dragland/Smart_Home/html/res/posters/0vNBeXZ.png

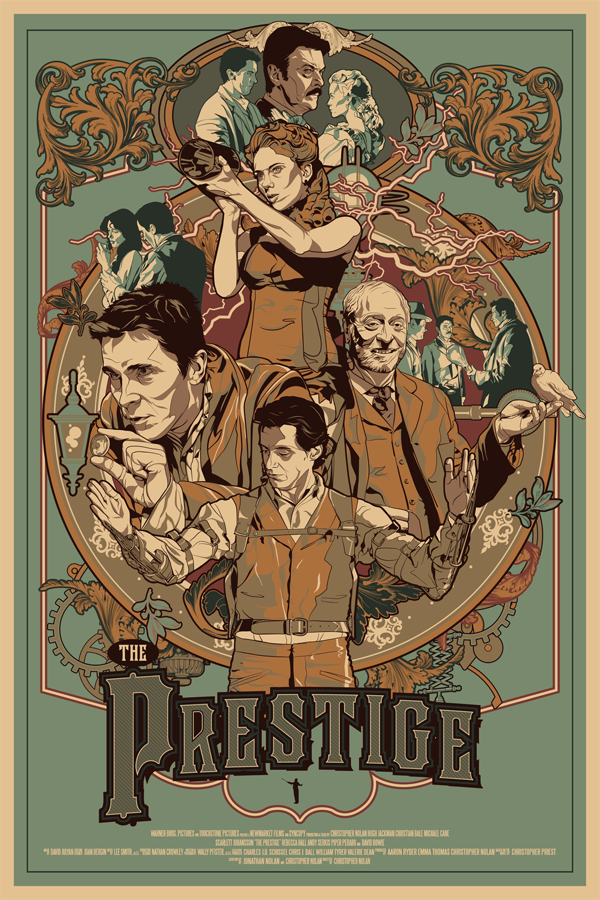
html/res/posters/0vNBeXZ.png
