dragland/Smart_Home/html/res/posters/1m5z1brr5z6y.jpg

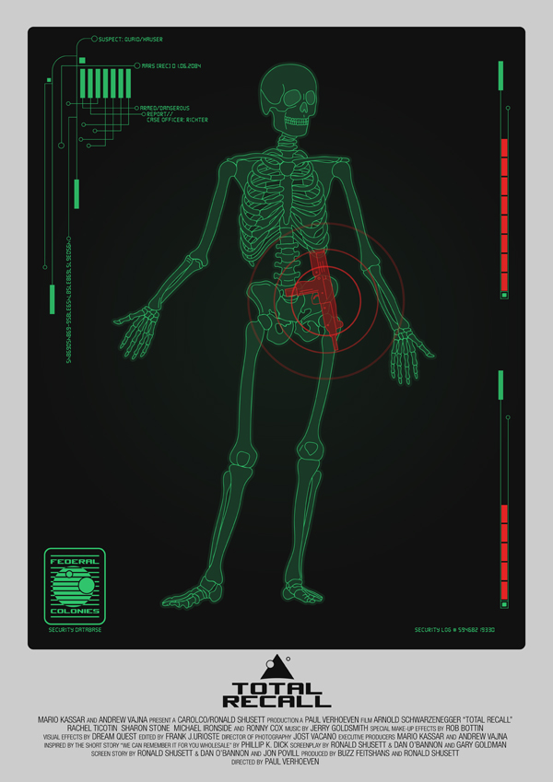
html/res/posters/1m5z1brr5z6y.jpg
