dragland/Smart_Home/html/res/posters/2OzRsxW.jpg

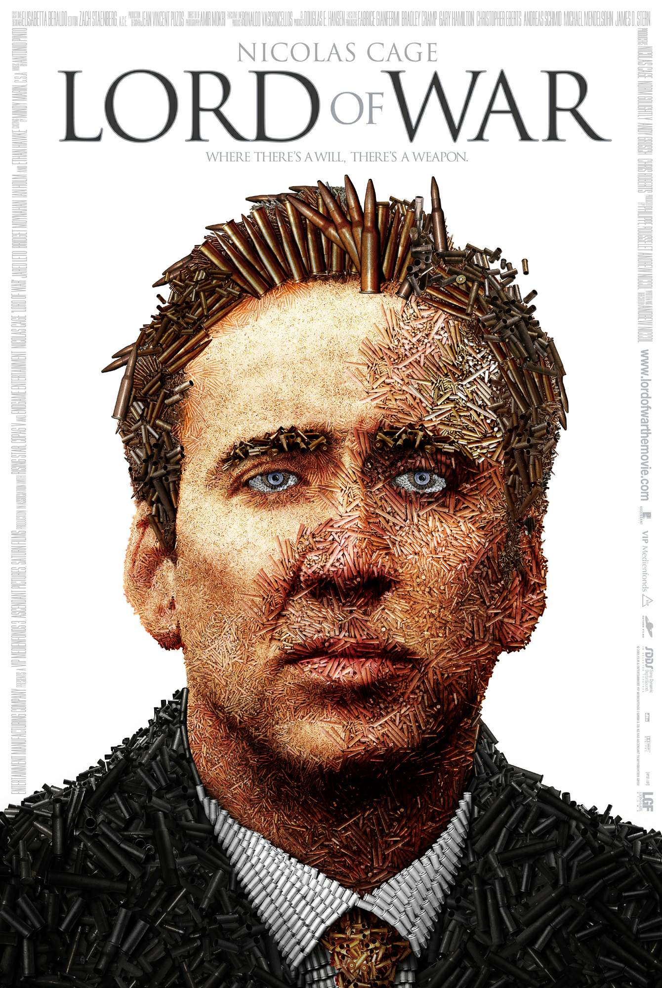
html/res/posters/2OzRsxW.jpg
