dragland/Smart_Home/html/res/posters/3QKCHwL.jpg

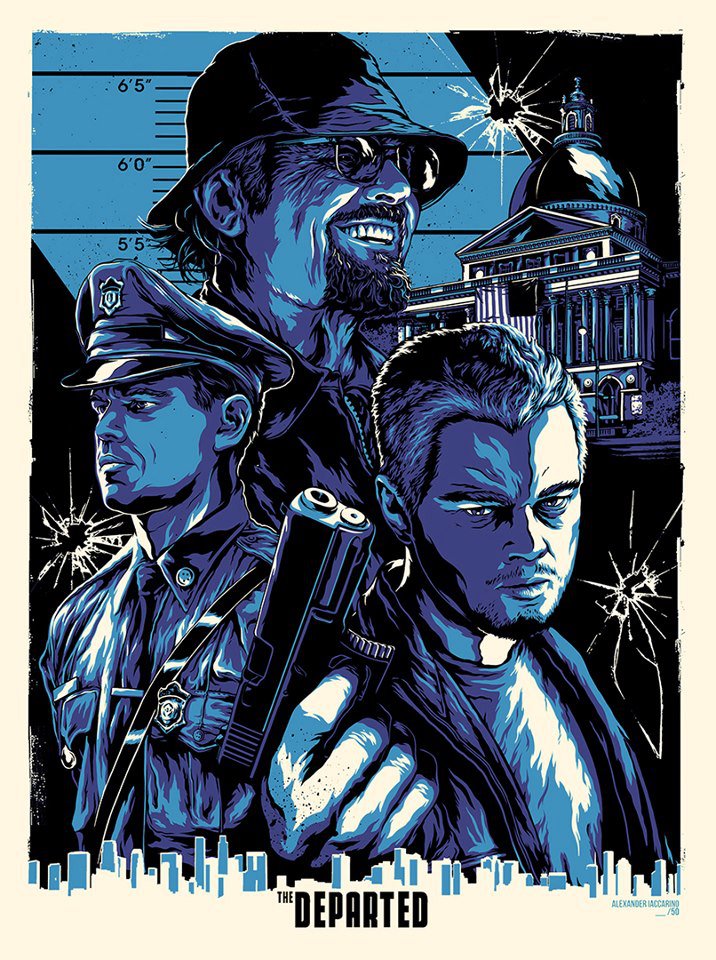
html/res/posters/3QKCHwL.jpg
