dragland/Smart_Home/html/res/posters/3xilfjxztxby.jpg

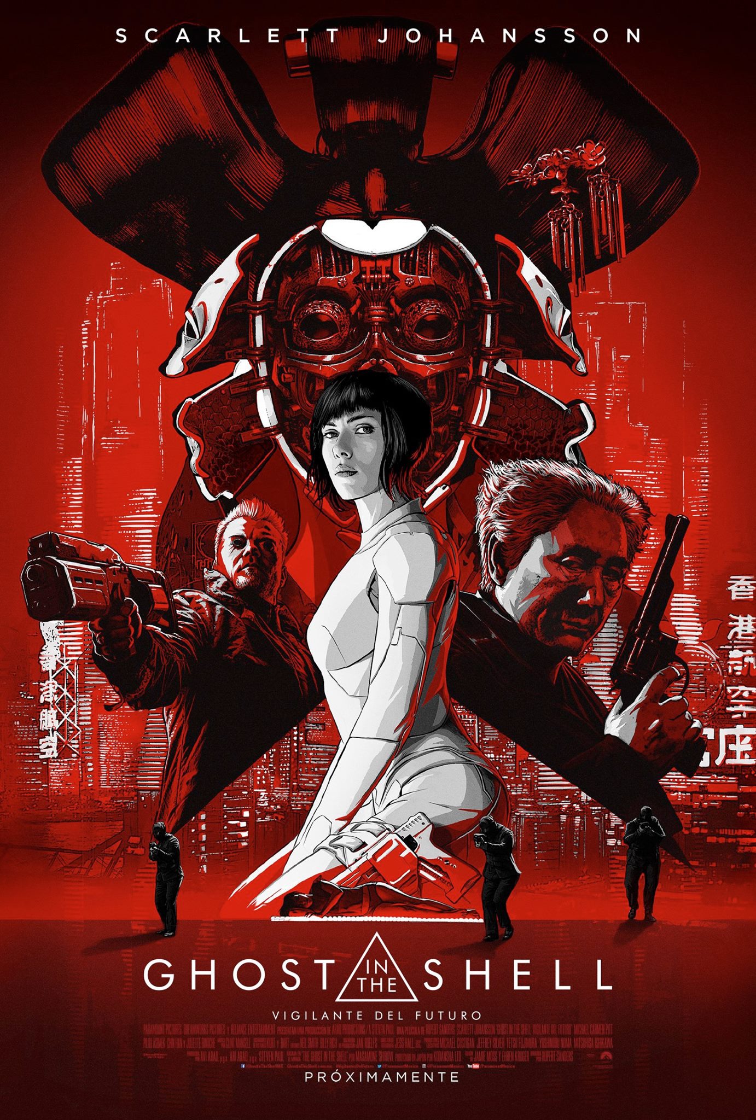
html/res/posters/3xilfjxztxby.jpg
