dragland/Smart_Home/html/res/posters/5fl5qlx6eaix.jpg

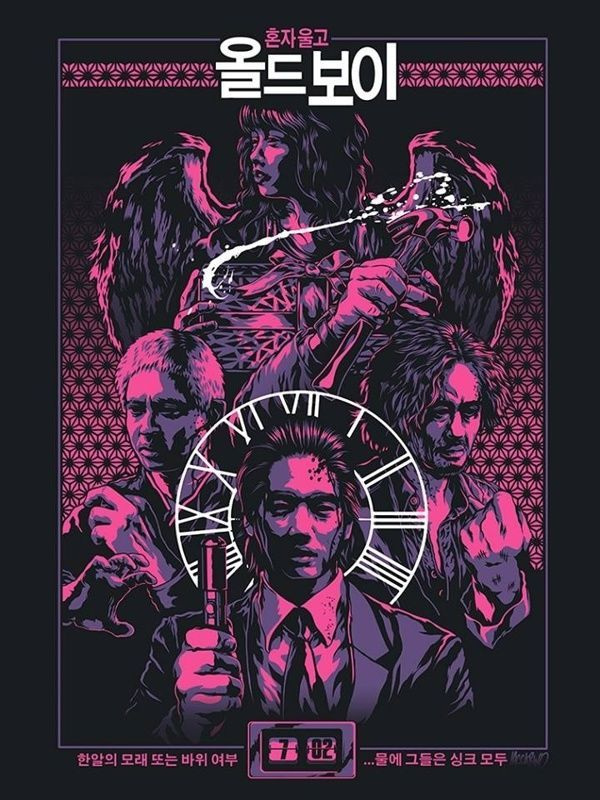
html/res/posters/5fl5qlx6eaix.jpg
