dragland/Smart_Home/html/res/posters/5FTenCP.jpg

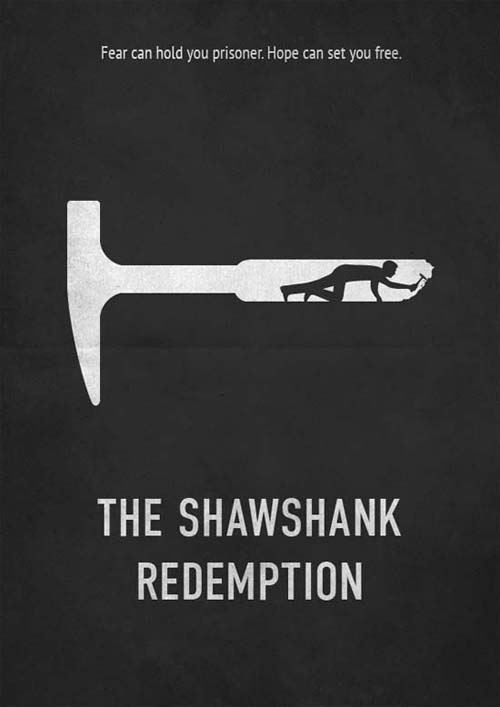
html/res/posters/5FTenCP.jpg
