dragland/Smart_Home/html/res/posters/5hzxofixnedz.jpg

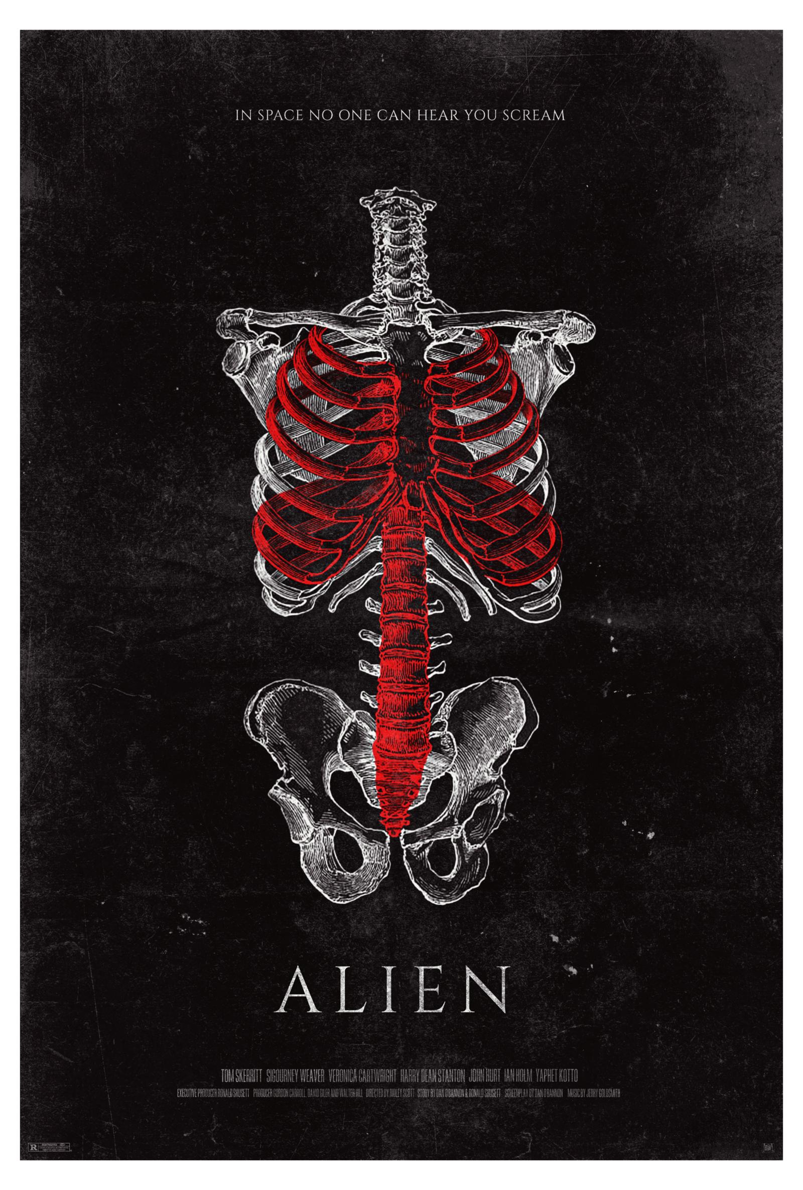
html/res/posters/5hzxofixnedz.jpg
