dragland/Smart_Home/html/res/posters/5mkgyaa8v3fy.jpg

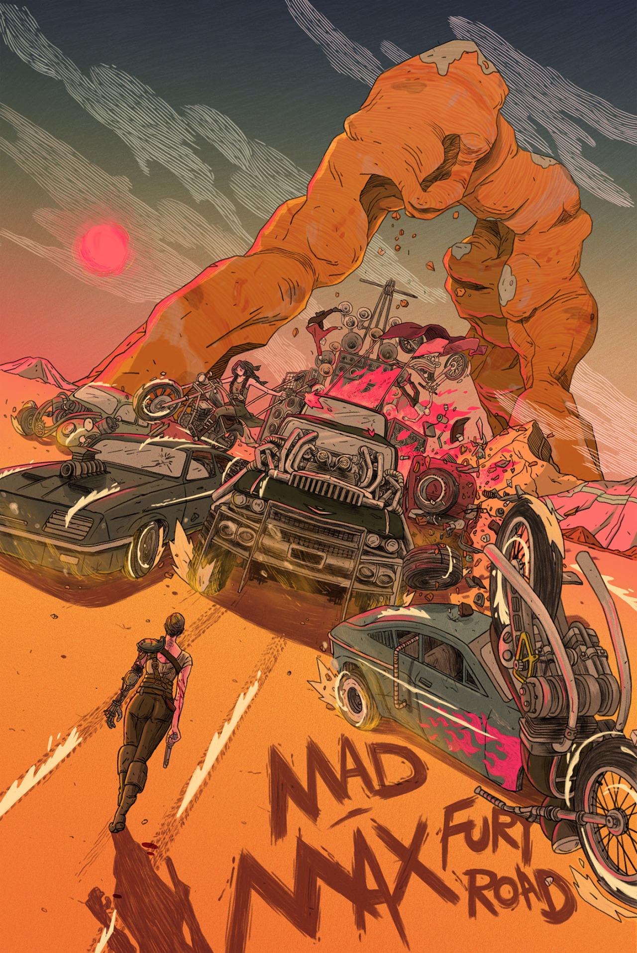
html/res/posters/5mkgyaa8v3fy.jpg
