dragland/Smart_Home/html/res/posters/5u4q2ypwrbdy.jpg

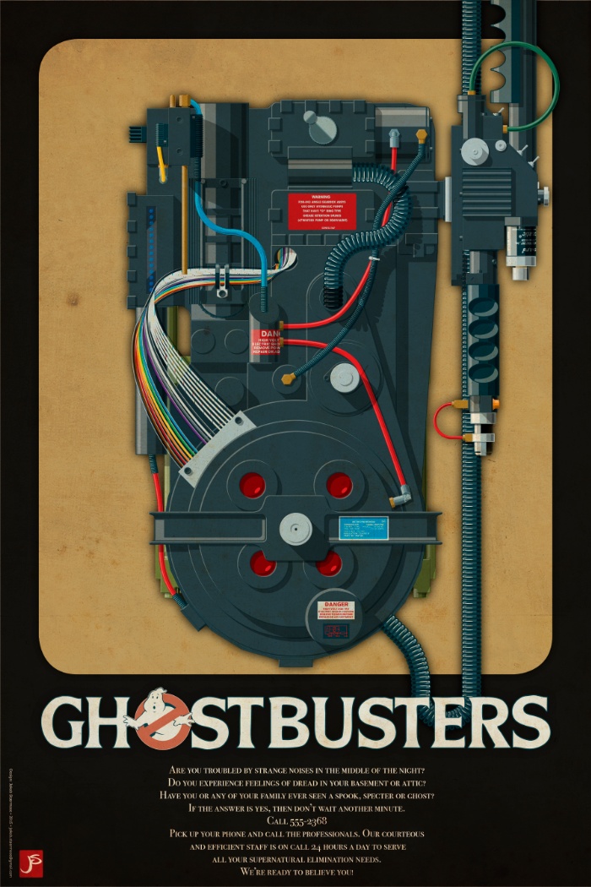
html/res/posters/5u4q2ypwrbdy.jpg
