dragland/Smart_Home/html/res/posters/6rzdQ8F.jpg

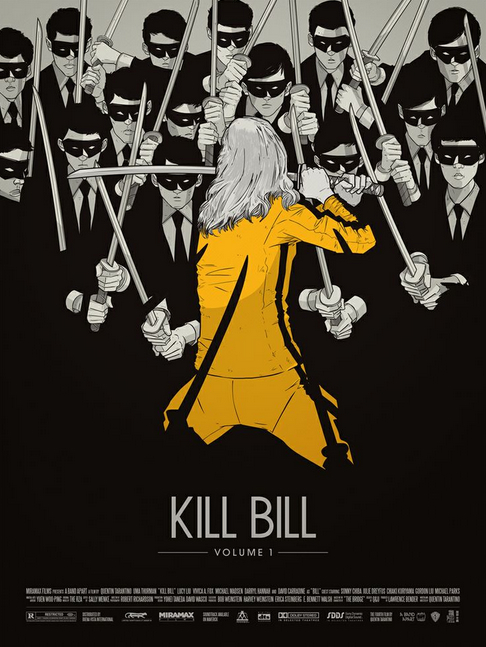
html/res/posters/6rzdQ8F.jpg
