dragland/Smart_Home/html/res/posters/7GJIbHS.jpg

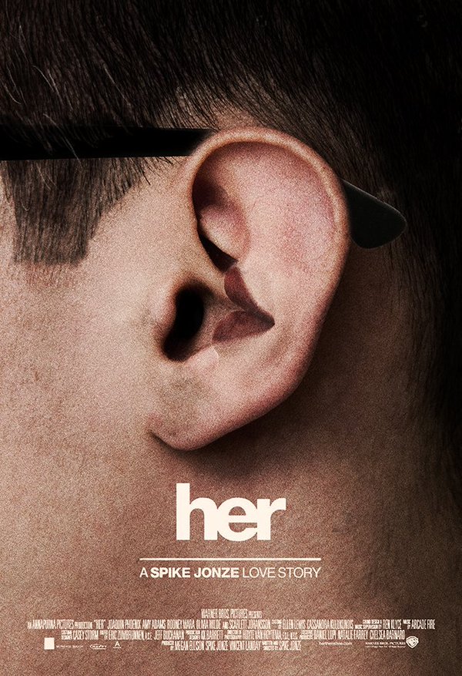
html/res/posters/7GJIbHS.jpg
