dragland/Smart_Home/html/res/posters/7szZ7dO.jpg

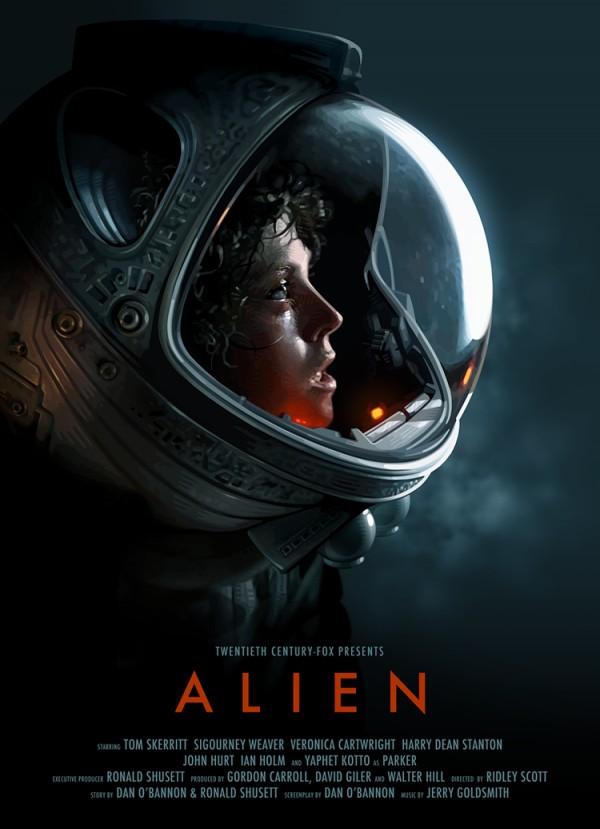
html/res/posters/7szZ7dO.jpg
