dragland/Smart_Home/html/res/posters/7UIQOzs.jpg

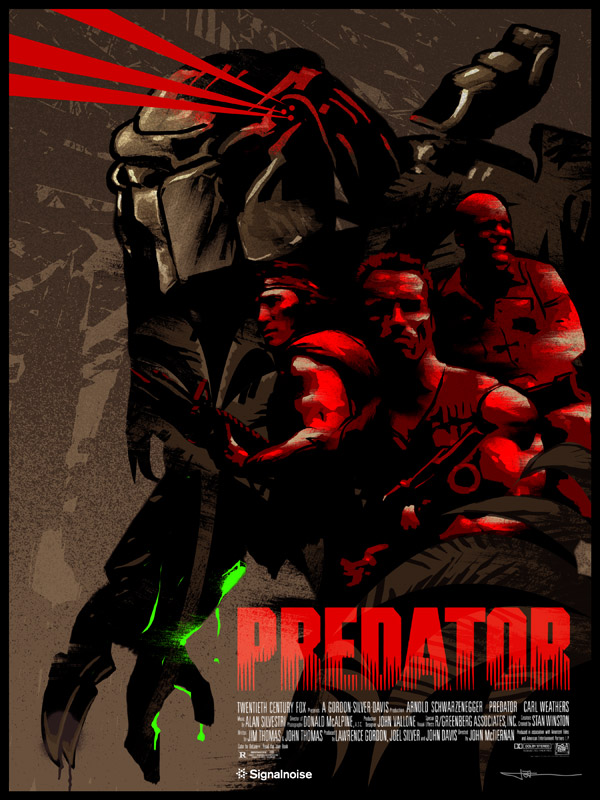
html/res/posters/7UIQOzs.jpg
