dragland/Smart_Home/html/res/posters/8h3PNZk.jpg

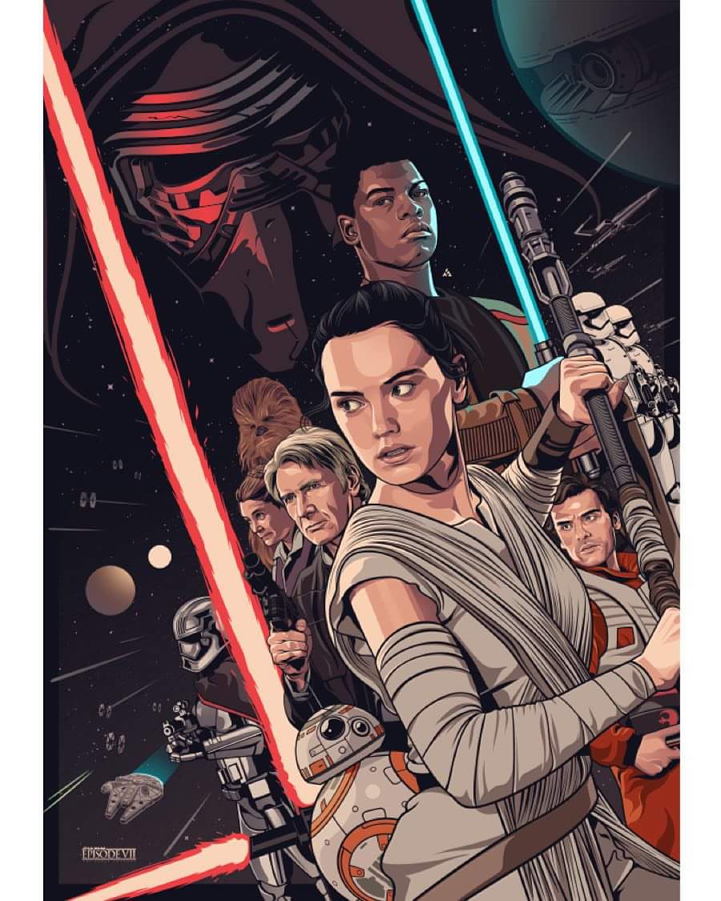
html/res/posters/8h3PNZk.jpg
