dragland/Smart_Home/html/res/posters/8u6Kgh6.jpg

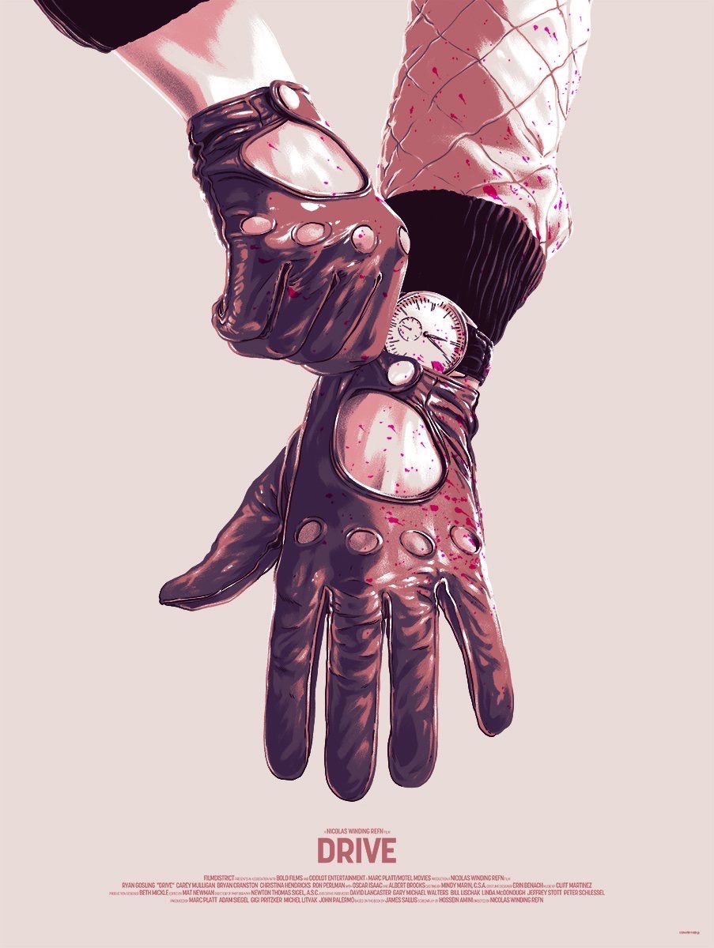
html/res/posters/8u6Kgh6.jpg
