dragland/Smart_Home/html/res/posters/8v36jp2fifhx.jpg

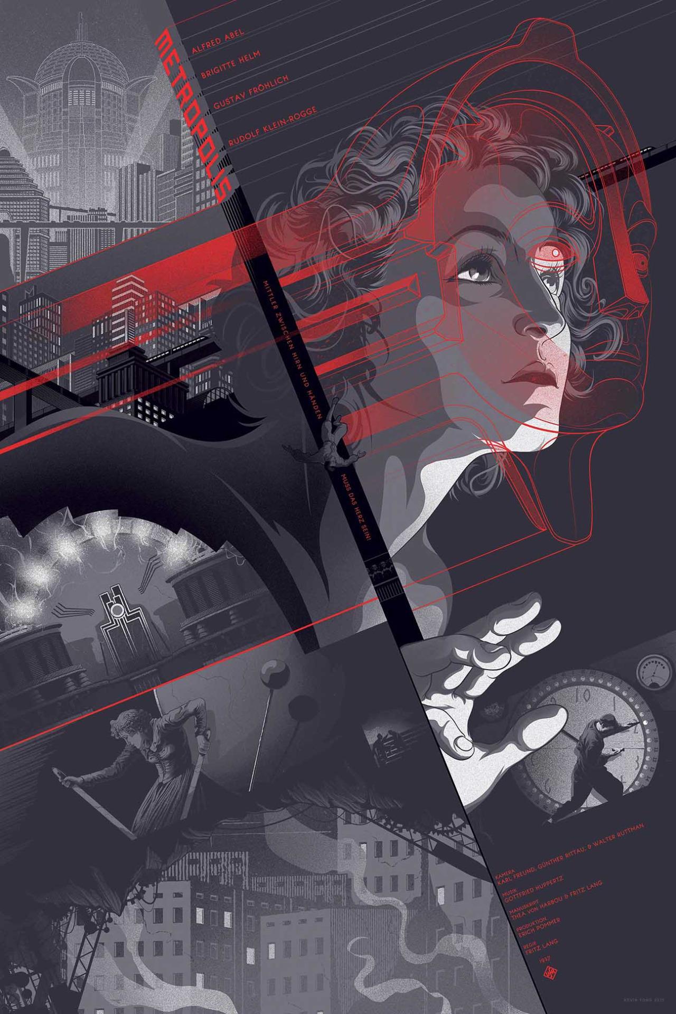
html/res/posters/8v36jp2fifhx.jpg
