dragland/Smart_Home/html/res/posters/8YTfZOx.jpg

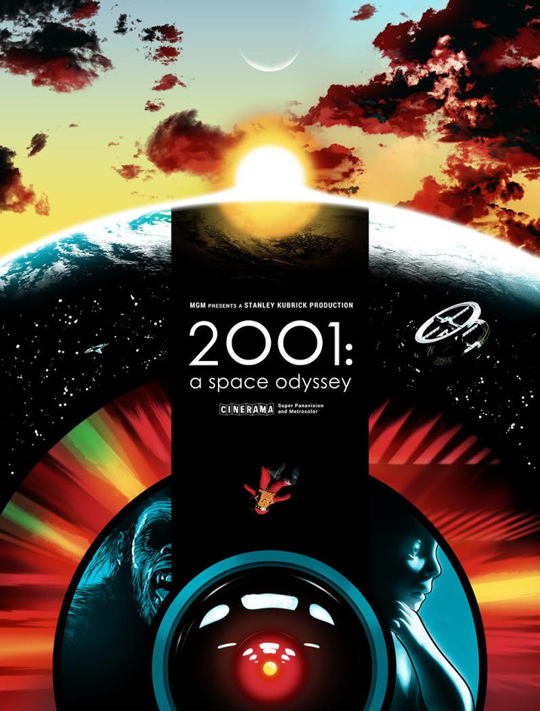
html/res/posters/8YTfZOx.jpg
