dragland/Smart_Home/html/res/posters/9OWsjfE.jpg

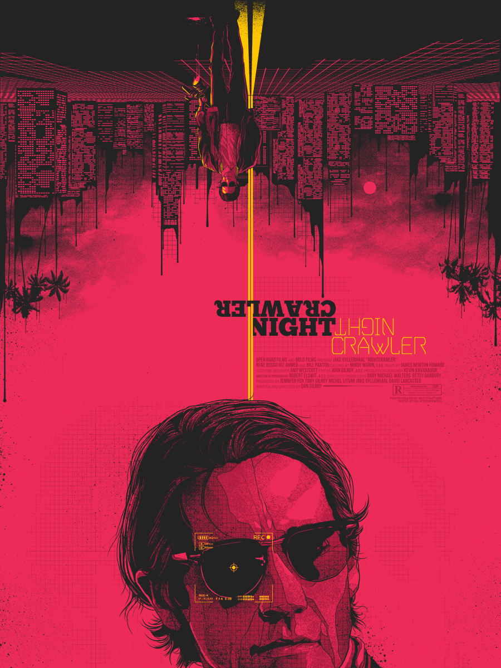
html/res/posters/9OWsjfE.jpg
