dragland/Smart_Home/html/res/posters/17-dorian_gray_1318896471.jpg

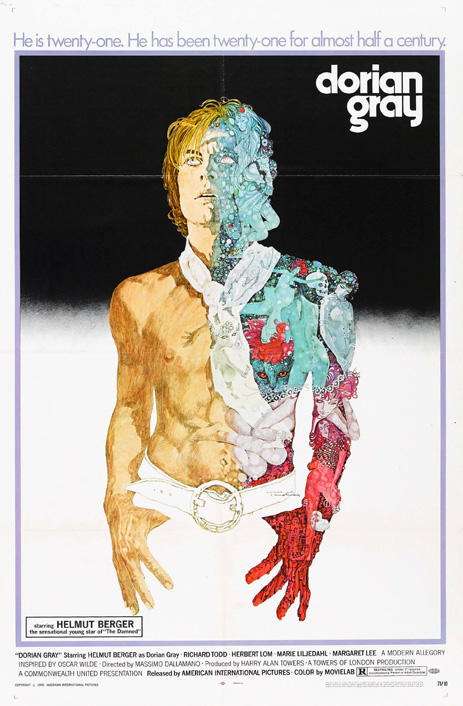
html/res/posters/17-dorian_gray_1318896471.jpg
