dragland/Smart_Home/html/res/posters/22Planet-Terror_1318898957.jpg

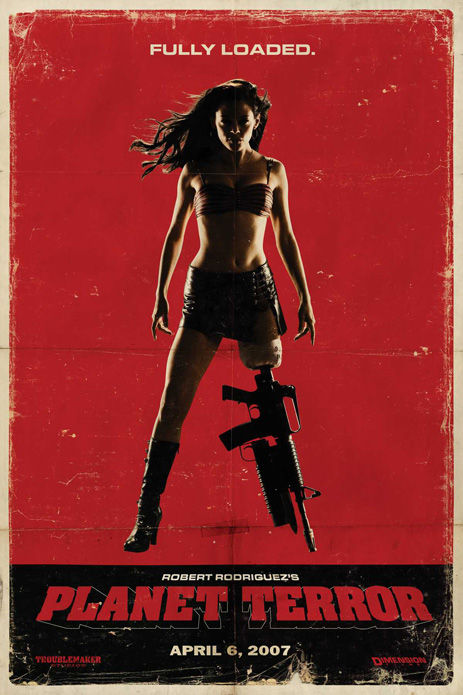
html/res/posters/22Planet-Terror_1318898957.jpg
