dragland/Smart_Home/html/res/posters/95XXI0x.png

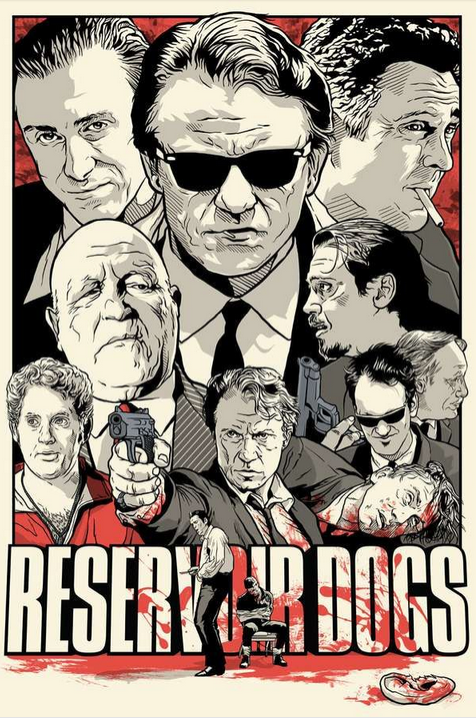
html/res/posters/95XXI0x.png
