dragland/Smart_Home/html/res/posters/97qwrleojhqz.jpg

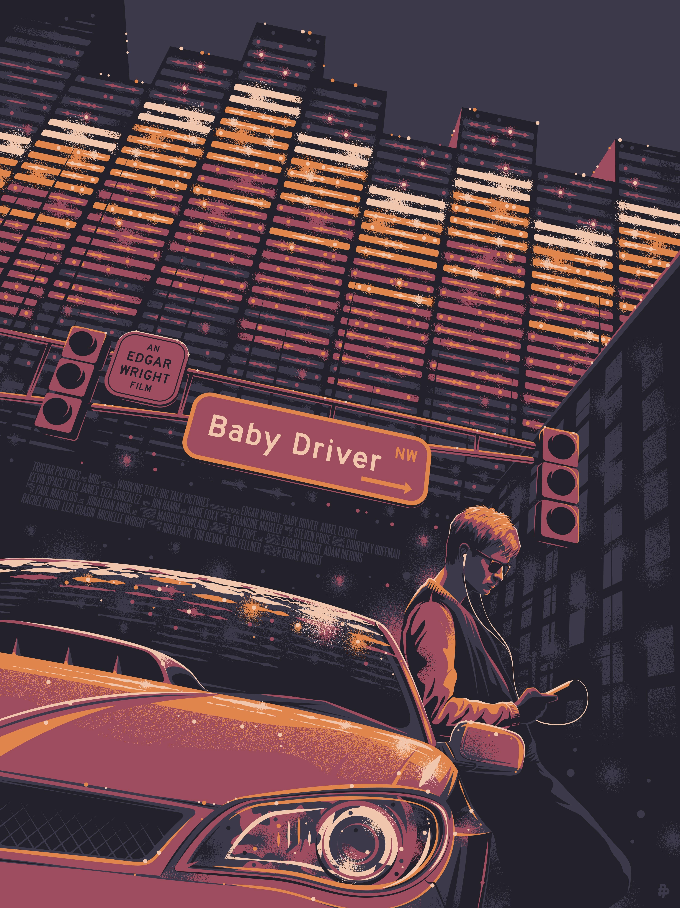
html/res/posters/97qwrleojhqz.jpg
