dragland/Smart_Home/html/res/posters/117d4e74bebbcbab08955fc3b9b594b3.jpg

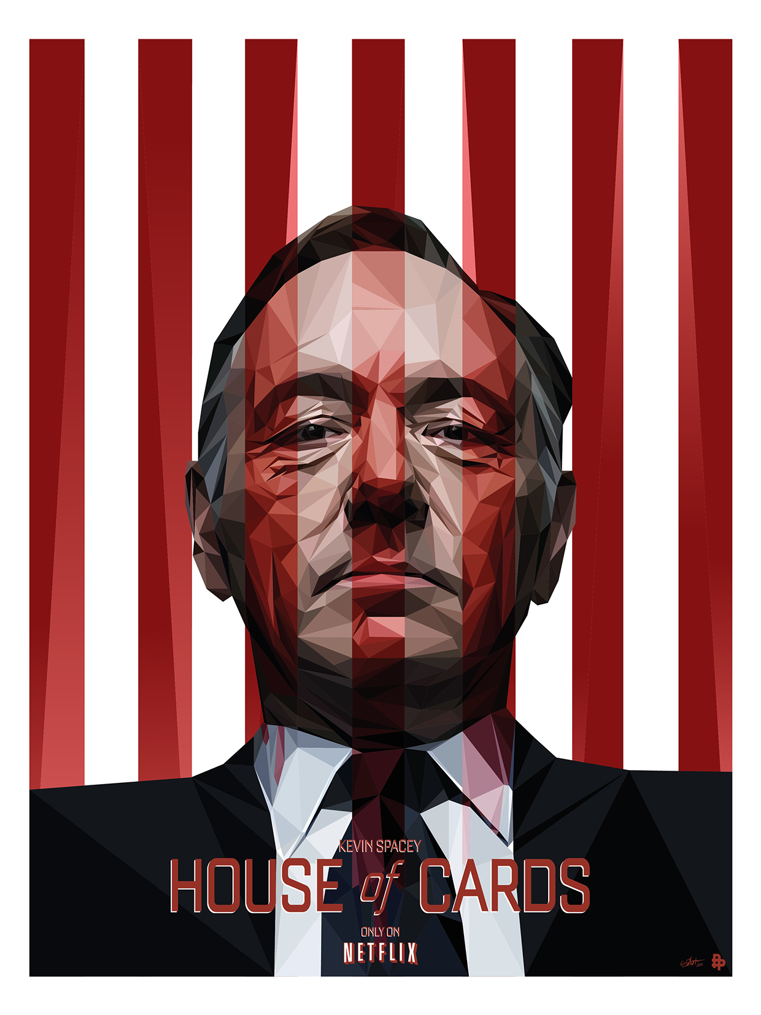
html/res/posters/117d4e74bebbcbab08955fc3b9b594b3.jpg
