dragland/Smart_Home/html/res/posters/243ViFD.jpg

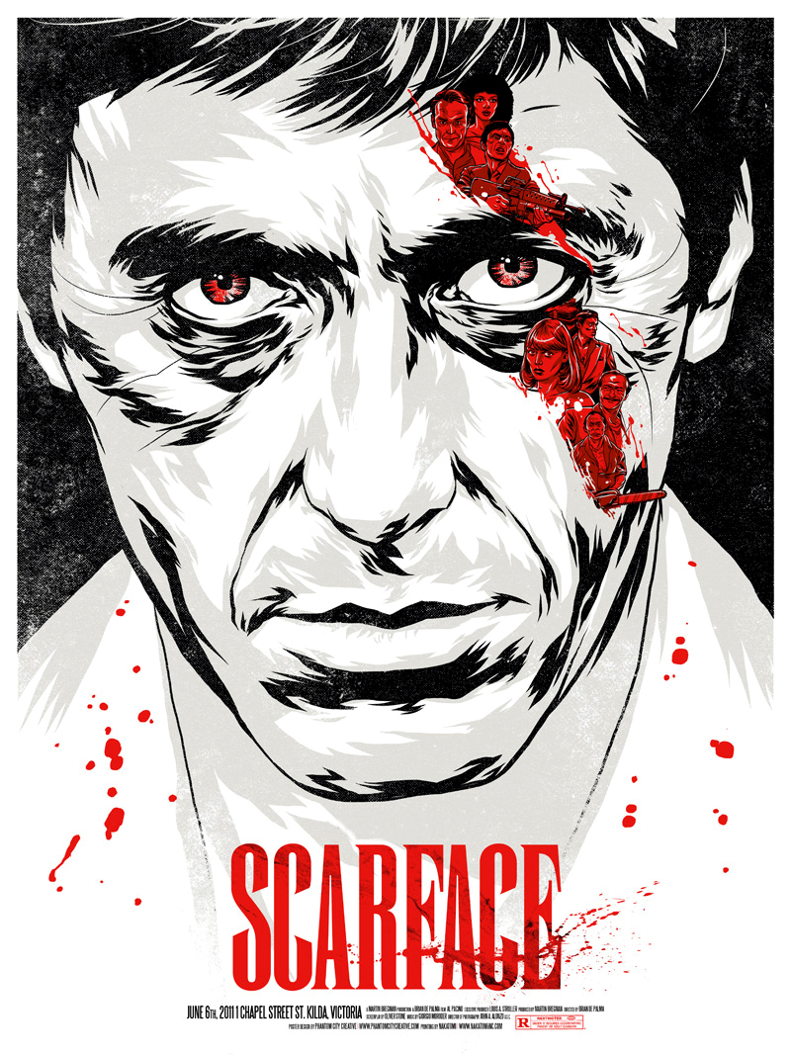
html/res/posters/243ViFD.jpg
