dragland/Smart_Home/html/res/posters/466Aien.jpg

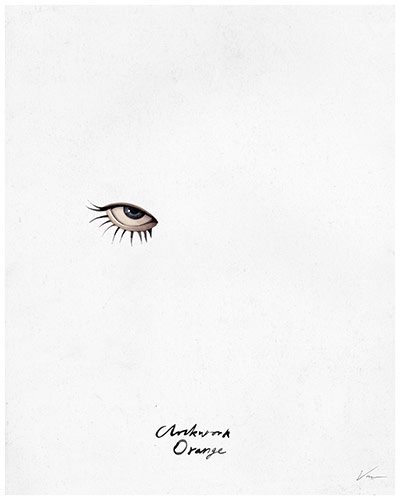
html/res/posters/466Aien.jpg
