dragland/Smart_Home/html/res/posters/2001_colortest14_72.jpg

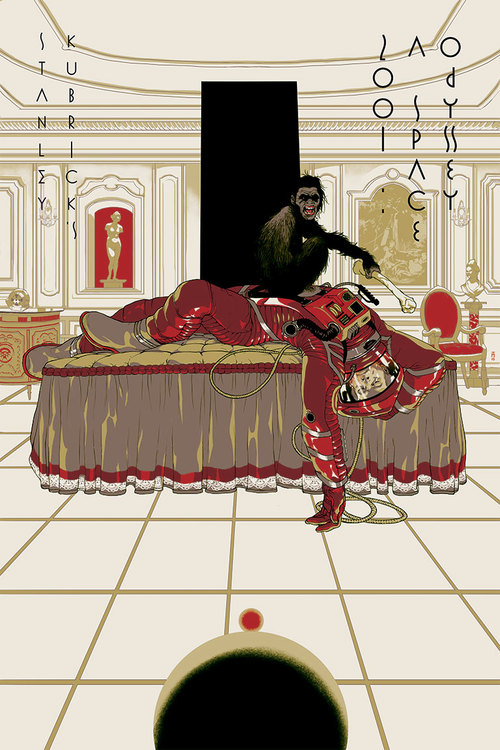
html/res/posters/2001_colortest14_72.jpg
