dragland/Smart_Home/html/res/posters/a6Sbj0L.jpg

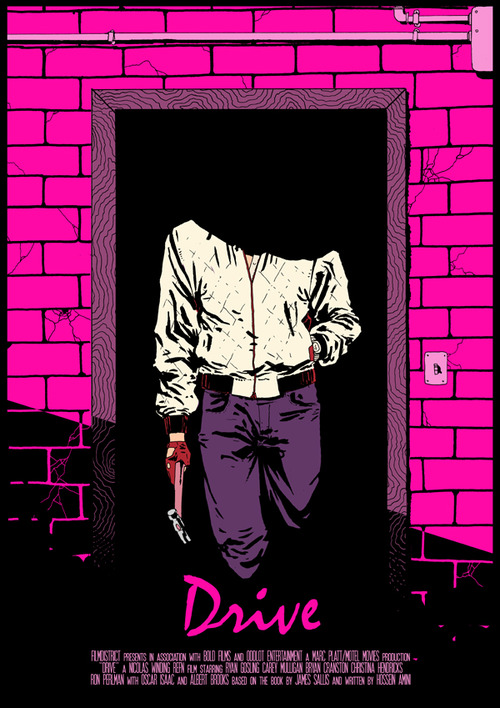
html/res/posters/a6Sbj0L.jpg
