dragland/Smart_Home/html/res/posters/akD52Hh.jpg

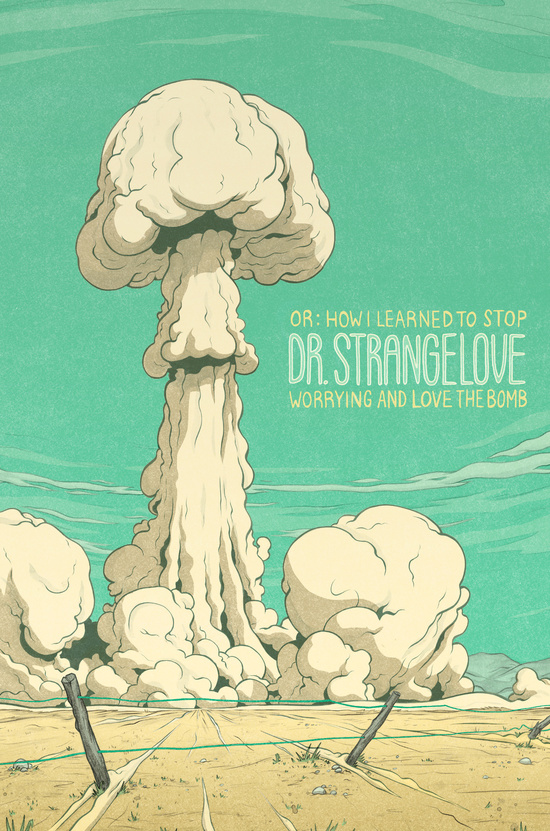
html/res/posters/akD52Hh.jpg
