dragland/Smart_Home/html/res/posters/AUyTsgM.jpg

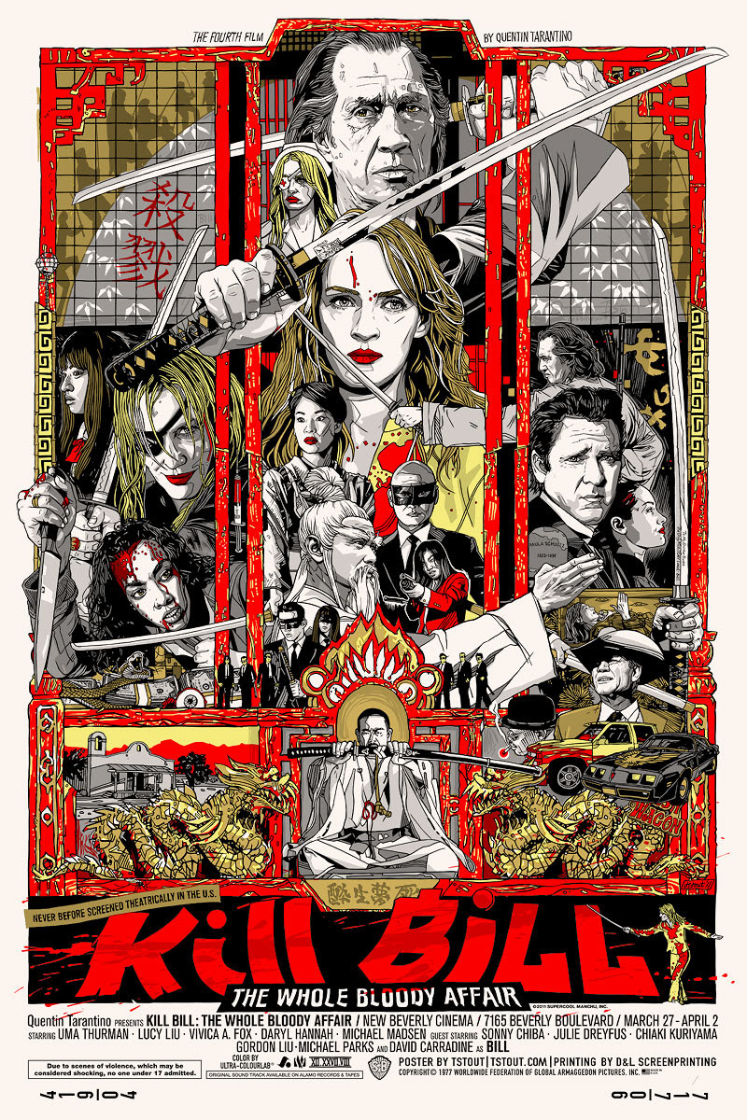
html/res/posters/AUyTsgM.jpg
