dragland/Smart_Home/html/res/posters/AVhfCm4.gif

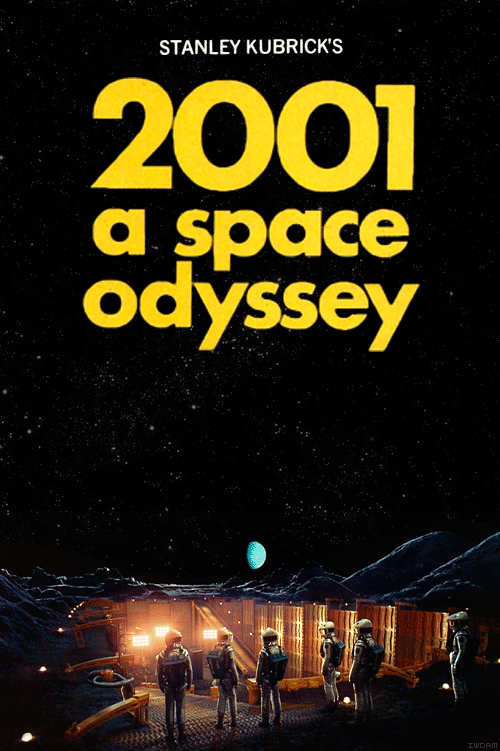
html/res/posters/AVhfCm4.gif
