dragland/Smart_Home/html/res/posters/AxIKC2x.jpg

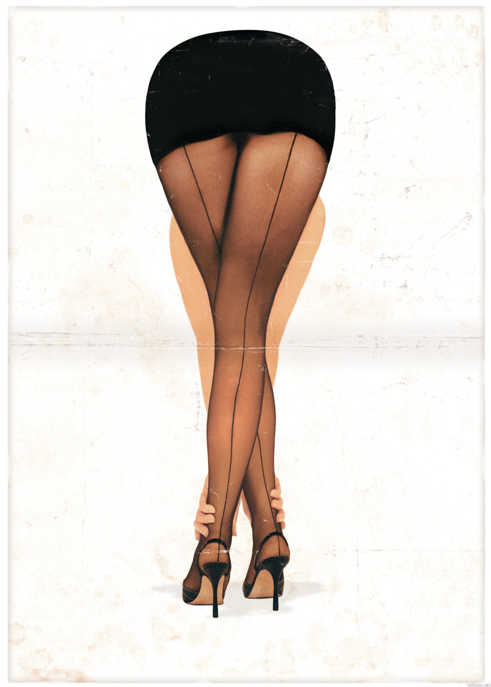
html/res/posters/AxIKC2x.jpg
