dragland/Smart_Home/html/res/posters/B9yhGLI.jpg

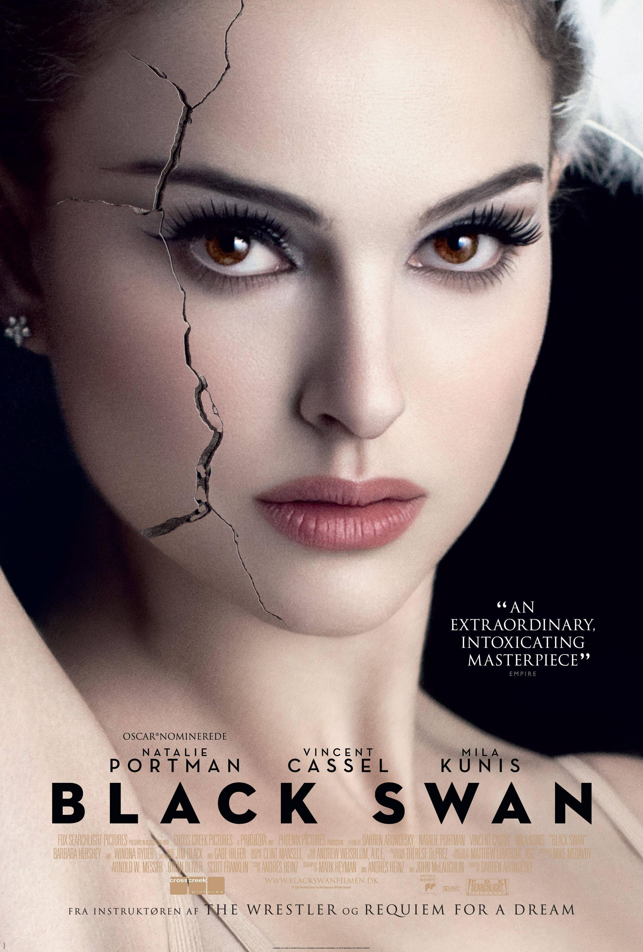
html/res/posters/B9yhGLI.jpg
