dragland/Smart_Home/html/res/posters/bbhpdsby42fy.jpg

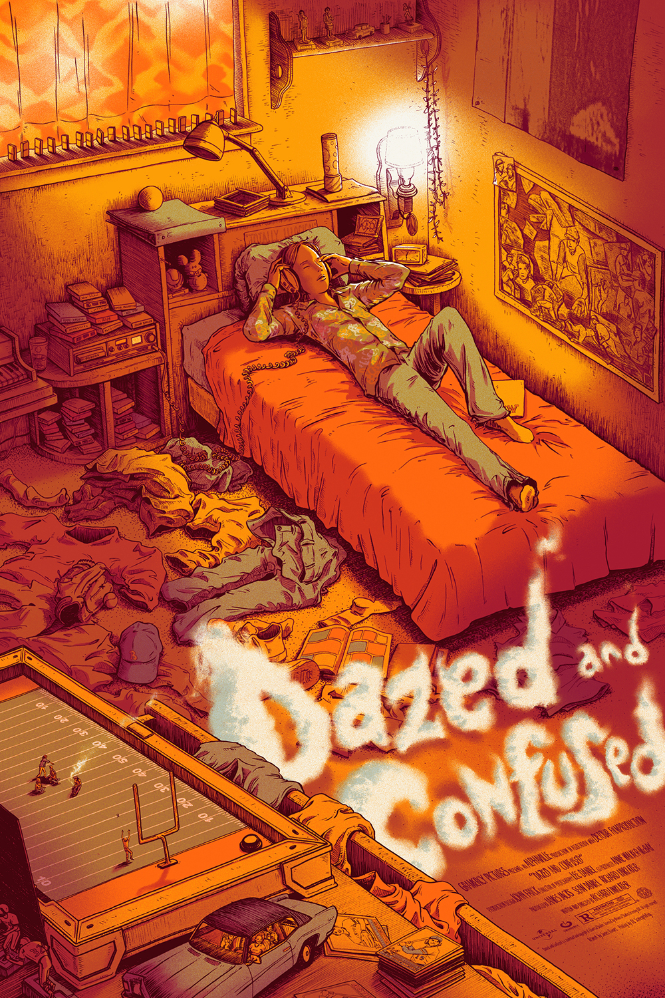
html/res/posters/bbhpdsby42fy.jpg
