dragland/Smart_Home/html/res/posters/BOQX4Tj.jpg

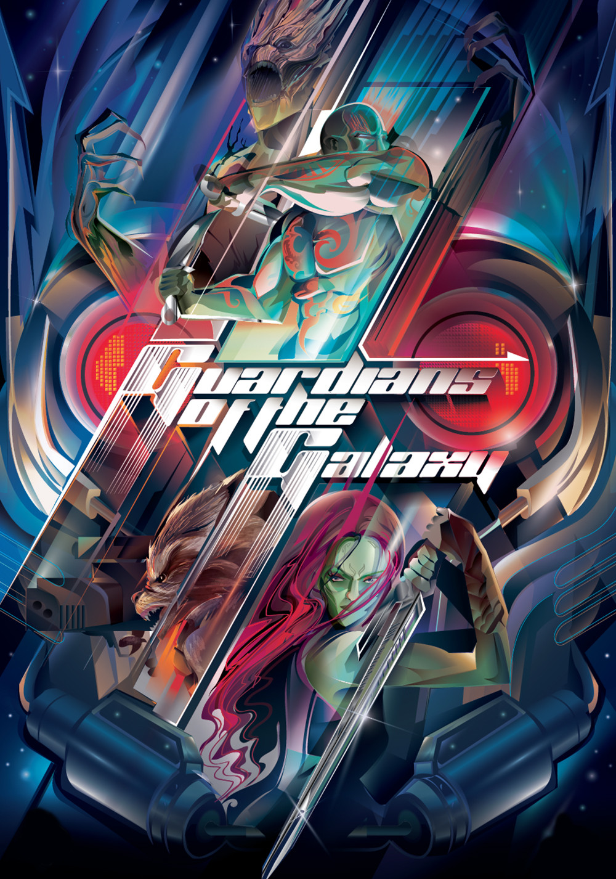
html/res/posters/BOQX4Tj.jpg
