dragland/Smart_Home/html/res/posters/BsjfuuV.jpg

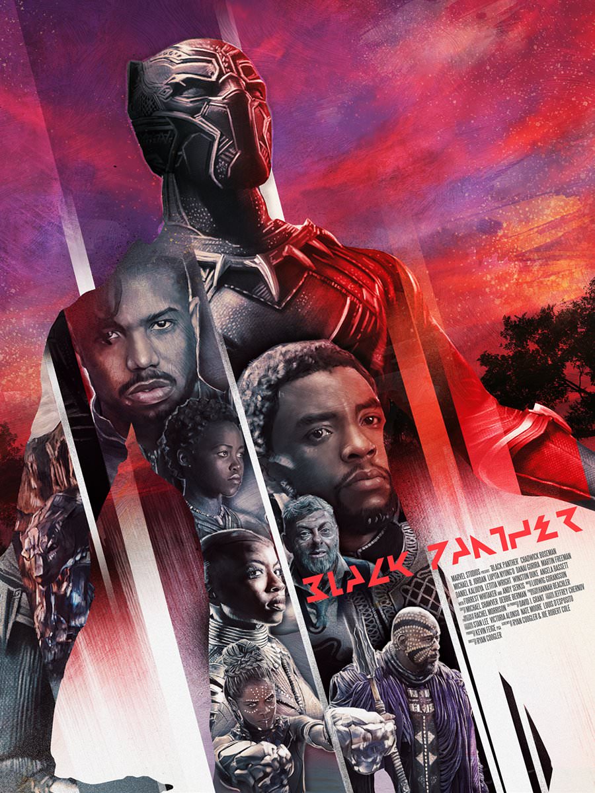
html/res/posters/BsjfuuV.jpg
