dragland/Smart_Home/html/res/posters/BuRFT4l.jpg

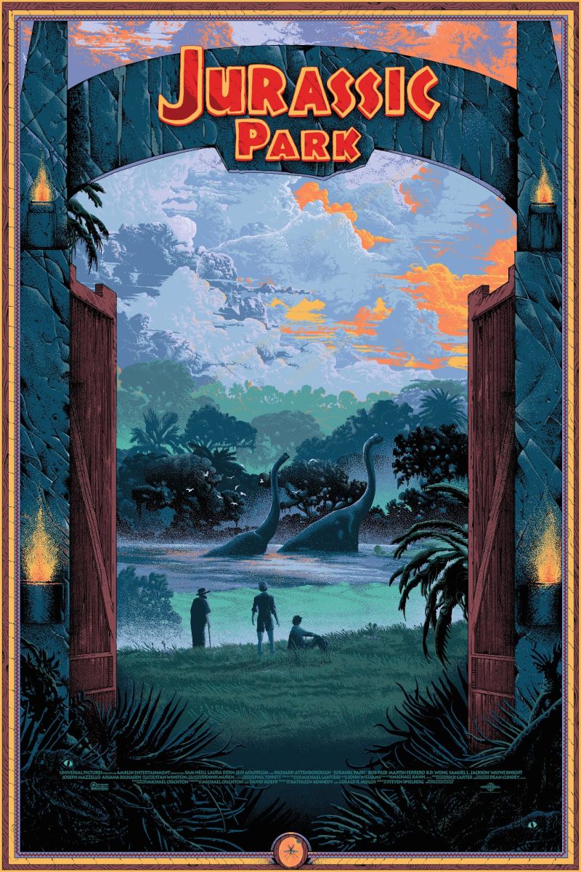
html/res/posters/BuRFT4l.jpg
