dragland/Smart_Home/html/res/posters/BX0jPmZ.jpg

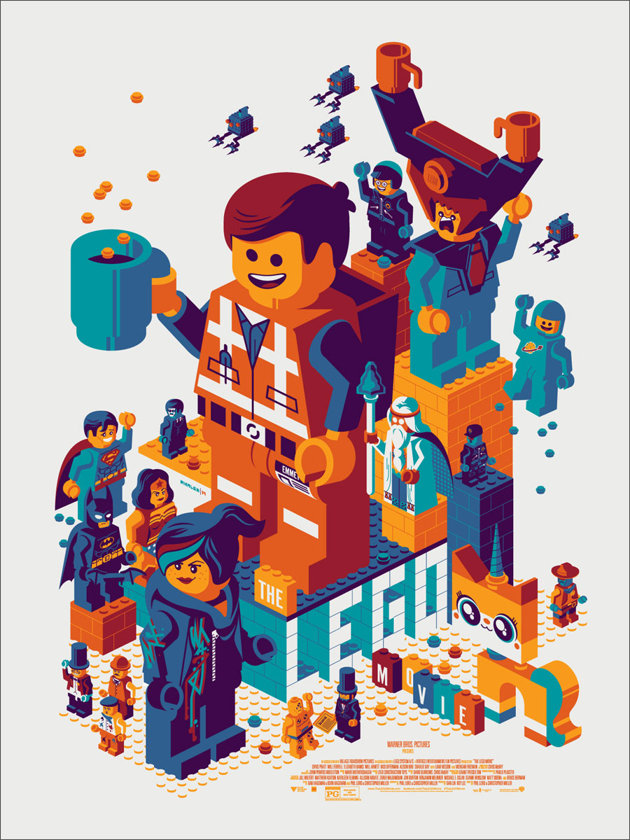
html/res/posters/BX0jPmZ.jpg
