dragland/Smart_Home/html/res/posters/c3B0WUv.jpg

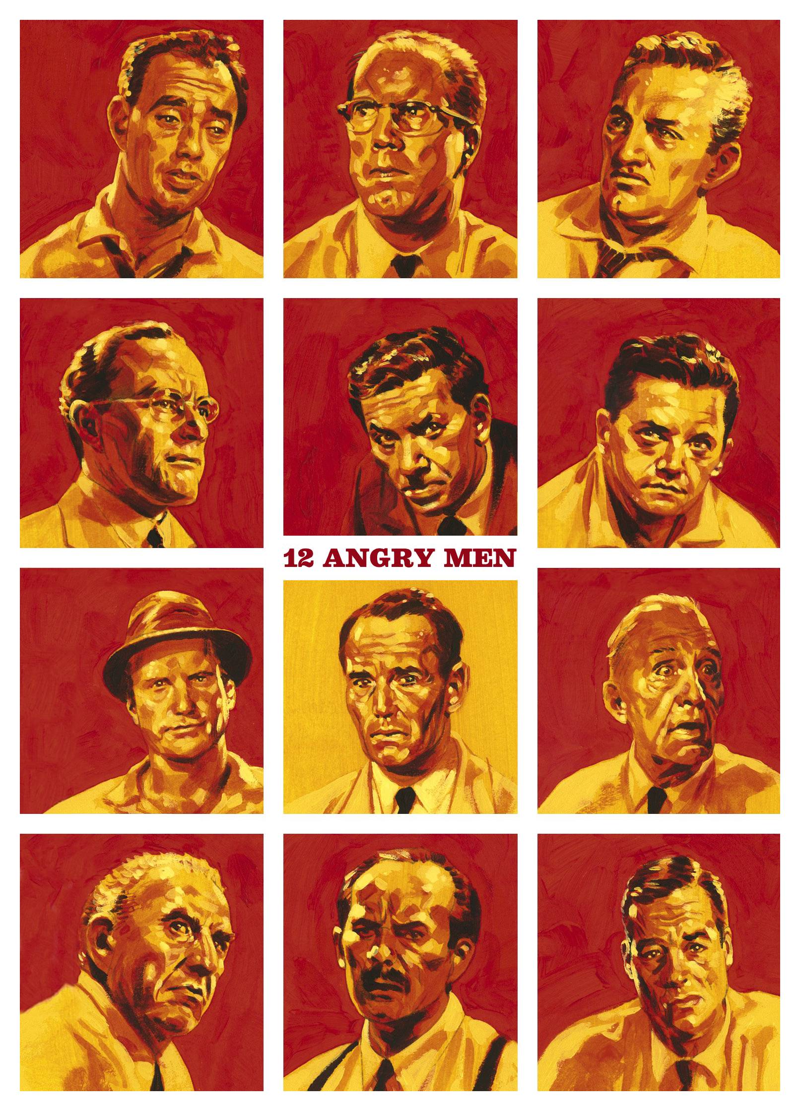
html/res/posters/c3B0WUv.jpg
