dragland/Smart_Home/html/res/posters/C55mEIe.jpg

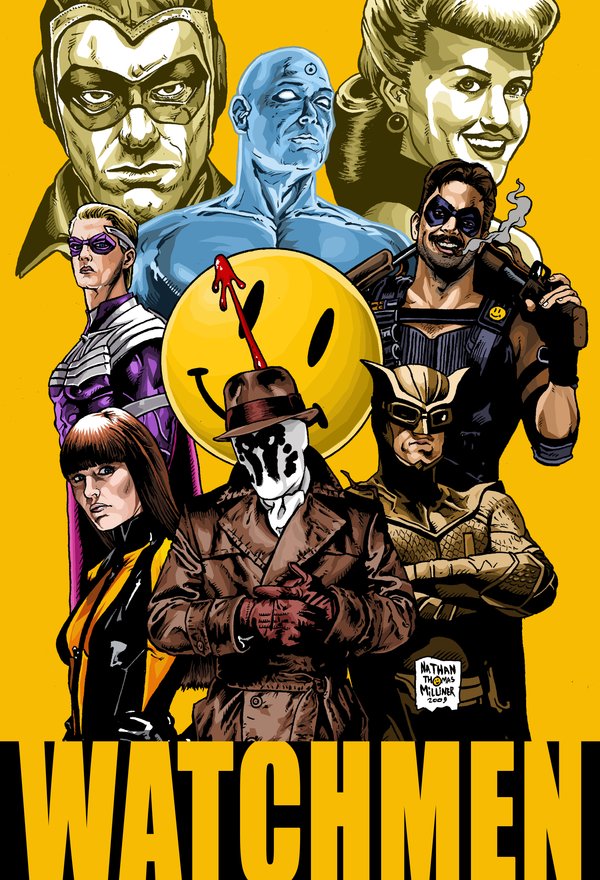
html/res/posters/C55mEIe.jpg
