dragland/Smart_Home/html/res/posters/ca1UNns.jpg

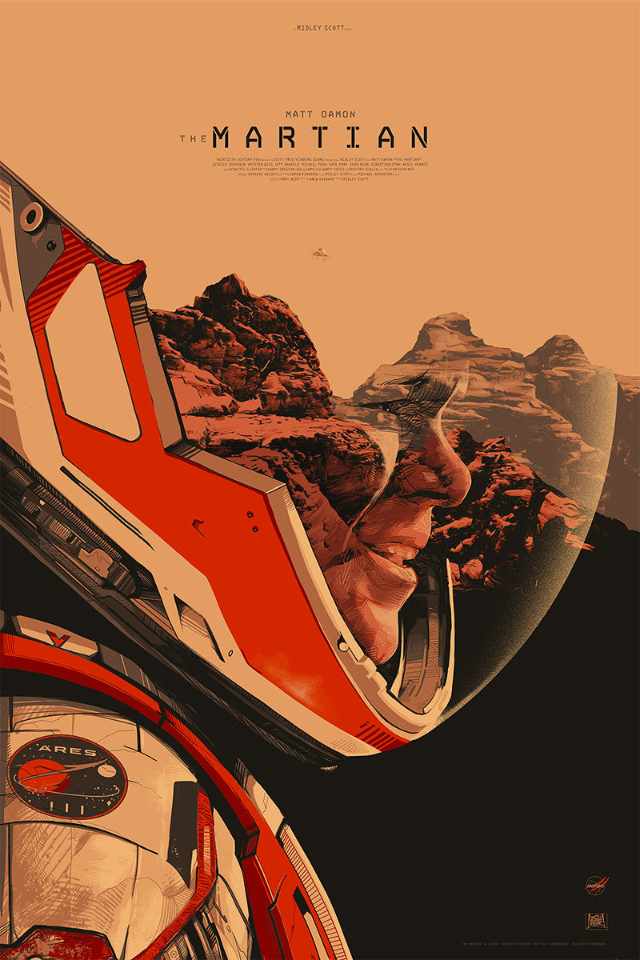
html/res/posters/ca1UNns.jpg
