dragland/Smart_Home/html/res/posters/CDFd3uM.jpg

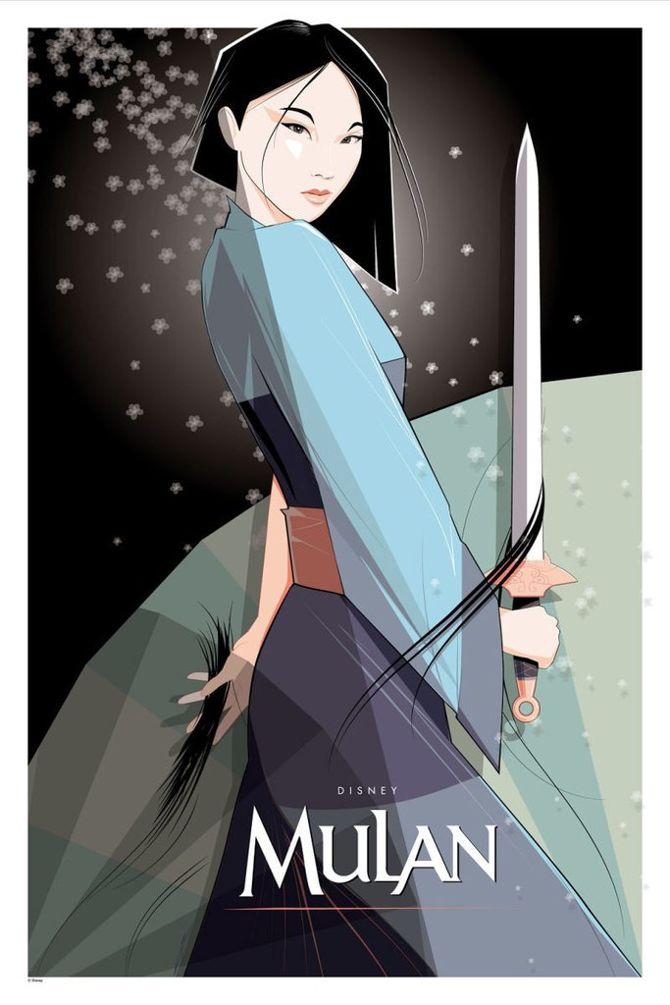
html/res/posters/CDFd3uM.jpg
