dragland/Smart_Home/html/res/posters/CfLugaL.jpg

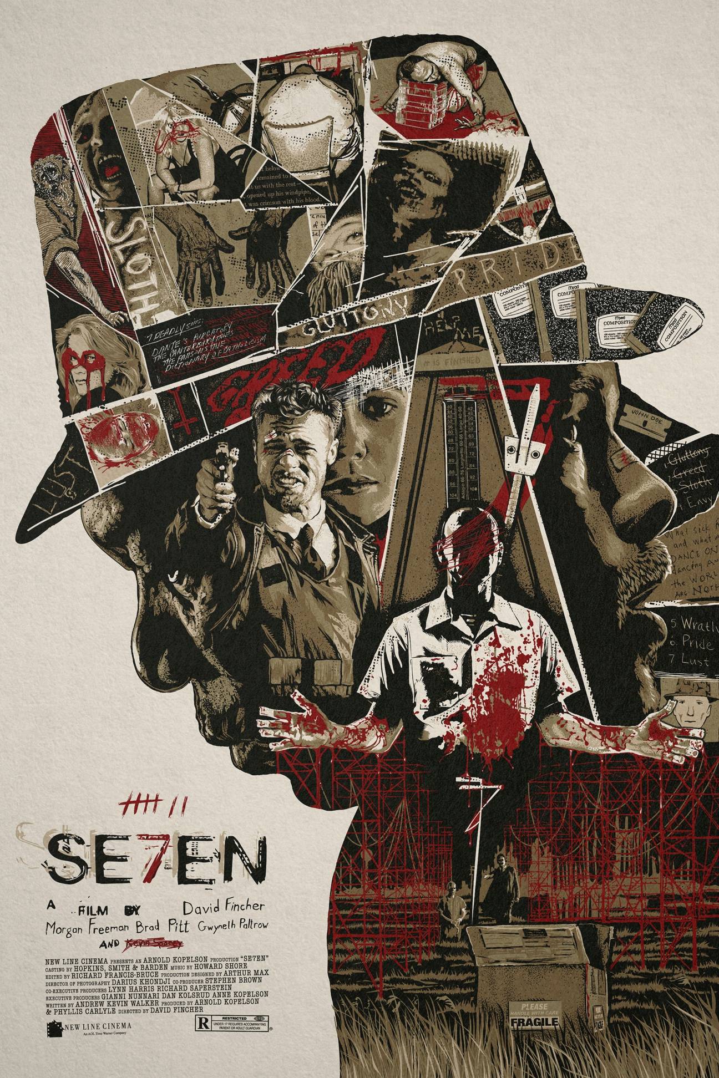
html/res/posters/CfLugaL.jpg
