dragland/Smart_Home/html/res/posters/cGziJeJ.jpg

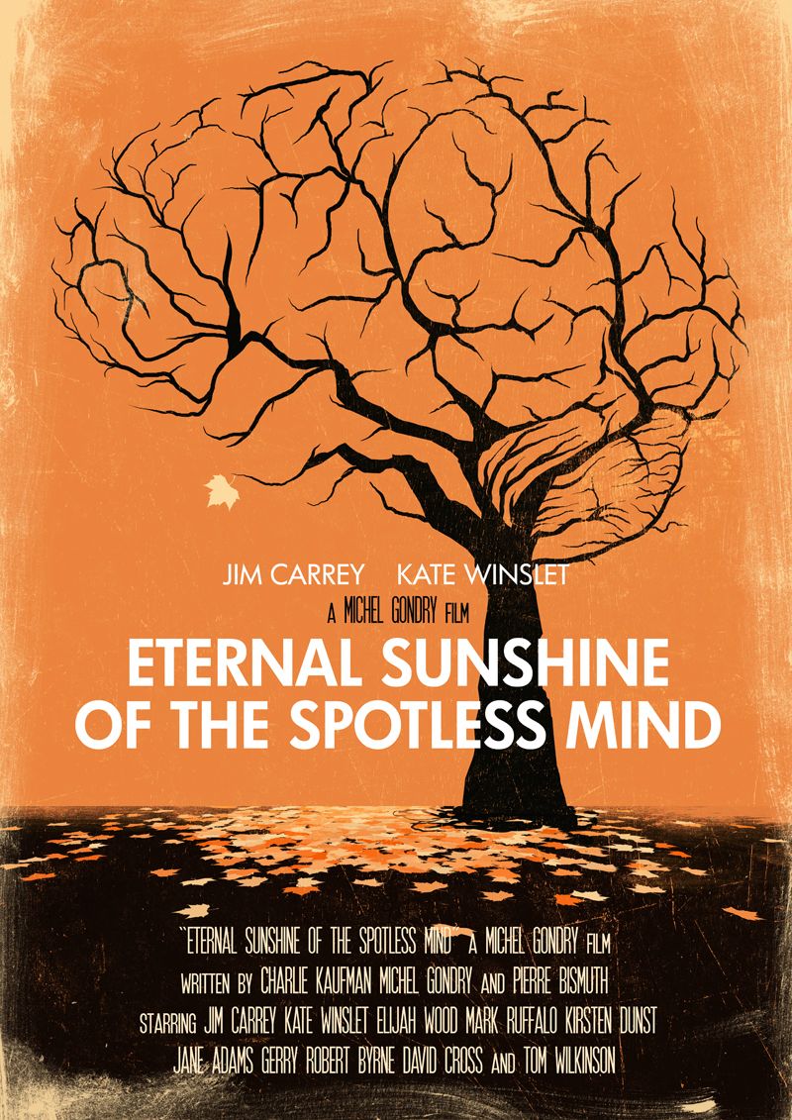
html/res/posters/cGziJeJ.jpg
