dragland/Smart_Home/html/res/posters/CJj4x1b.jpg

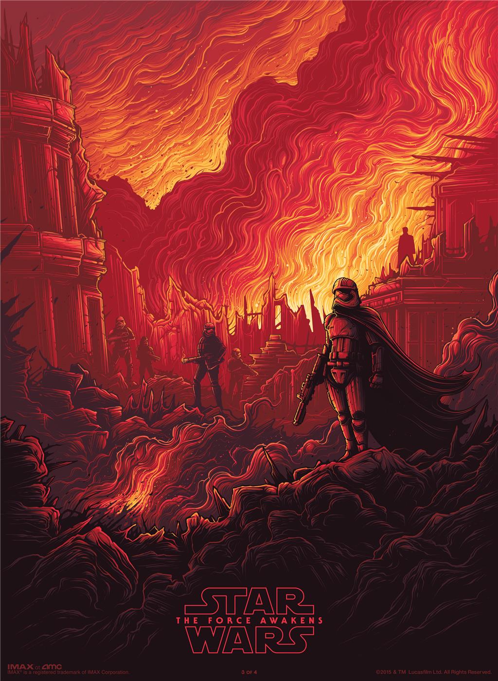
html/res/posters/CJj4x1b.jpg
