dragland/Smart_Home/html/res/posters/CjNTmT0.jpg

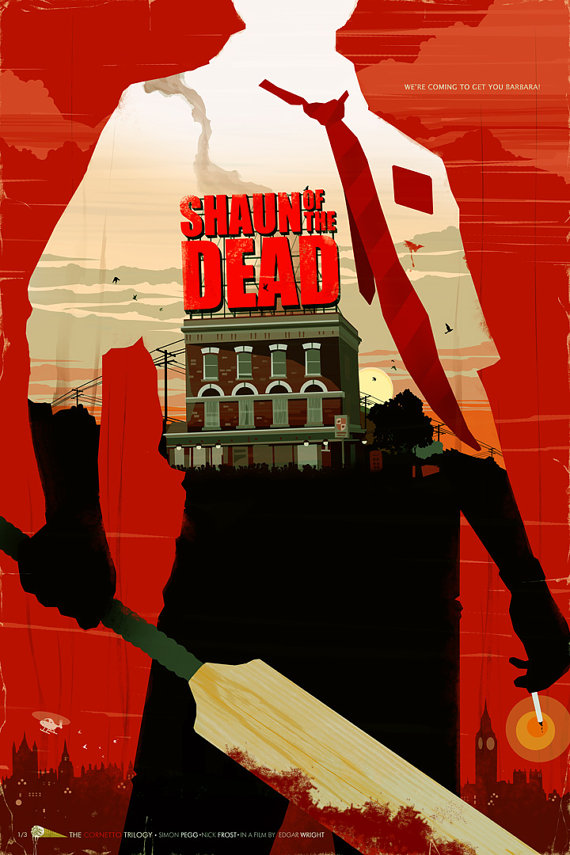
html/res/posters/CjNTmT0.jpg
