dragland/Smart_Home/html/res/posters/CmvlKyt.jpg

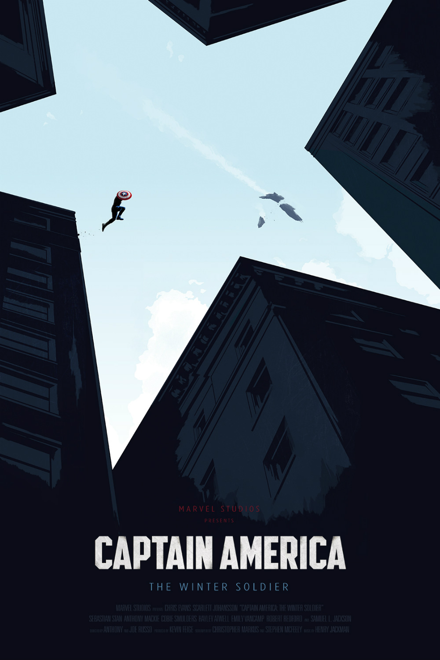
html/res/posters/CmvlKyt.jpg
