dragland/Smart_Home/html/res/posters/d373gbw10s7y.jpg

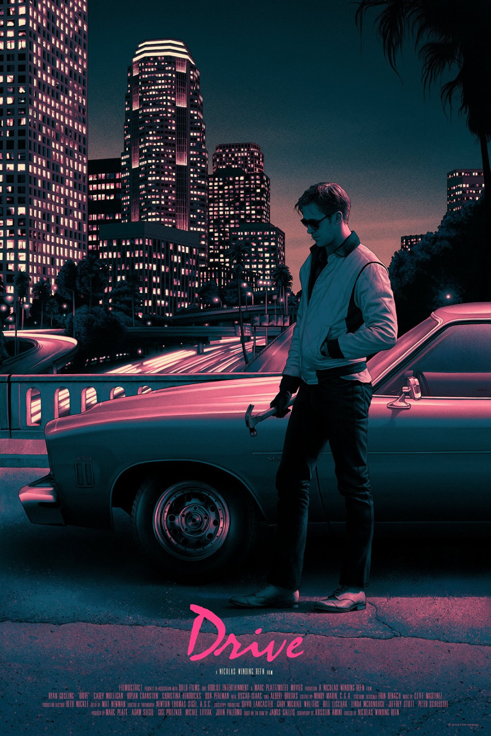
html/res/posters/d373gbw10s7y.jpg
