dragland/Smart_Home/html/res/posters/dG3m8fx.jpg

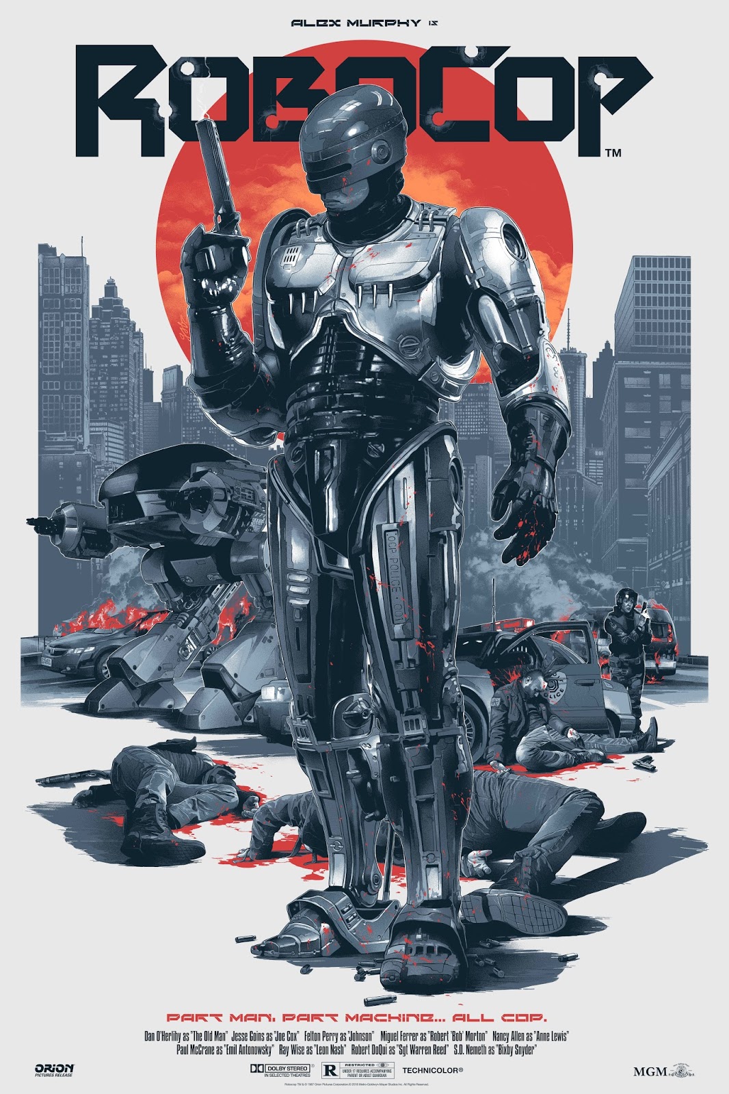
html/res/posters/dG3m8fx.jpg
