dragland/Smart_Home/html/res/posters/drMsYBR.jpg

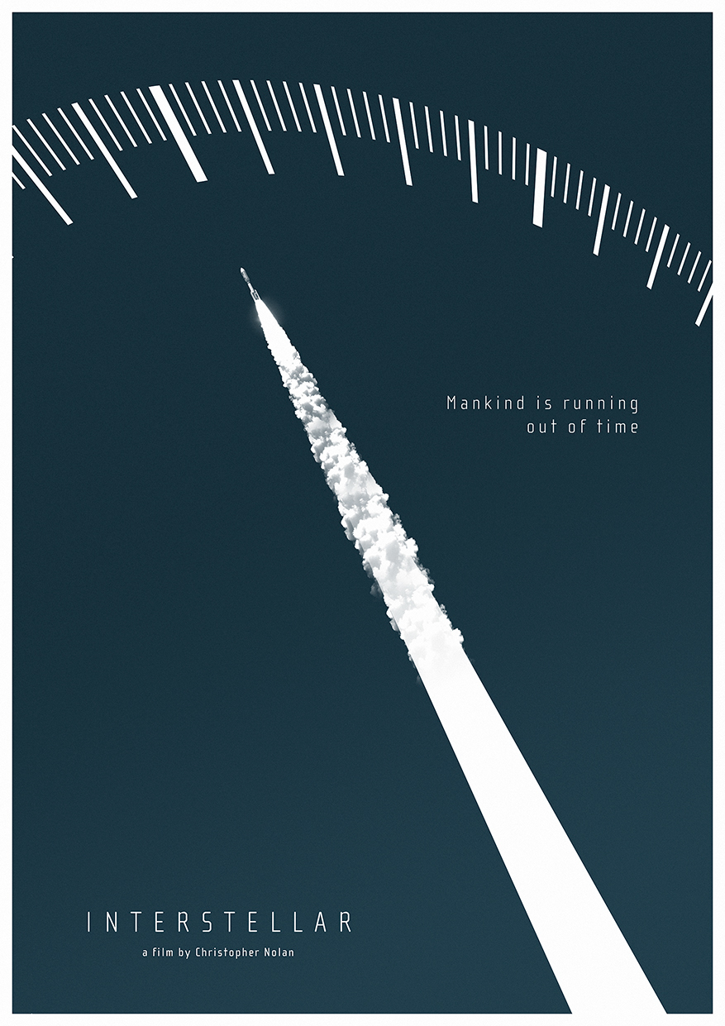
html/res/posters/drMsYBR.jpg
