dragland/Smart_Home/html/res/posters/dSWAhs4.jpg

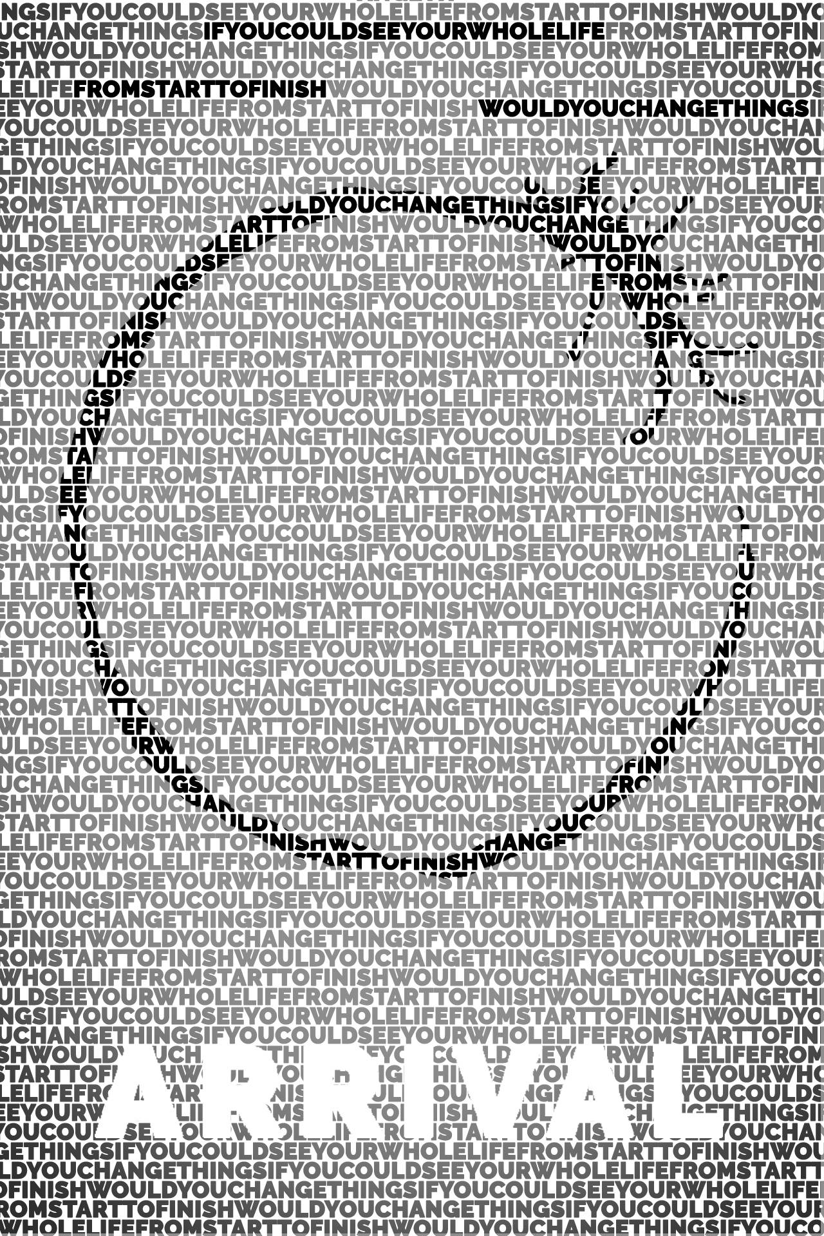
html/res/posters/dSWAhs4.jpg
