dragland/Smart_Home/html/res/posters/dz1m6znmknix.jpg

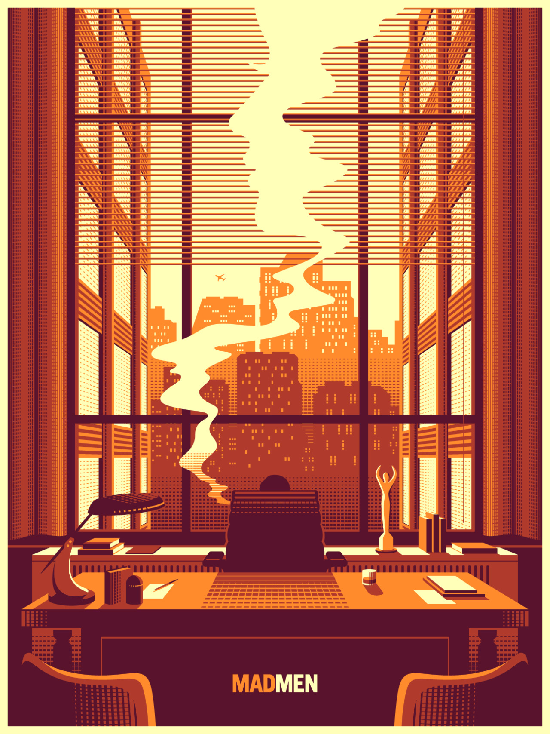
html/res/posters/dz1m6znmknix.jpg
