dragland/Smart_Home/html/res/posters/EiJpCkv.jpg

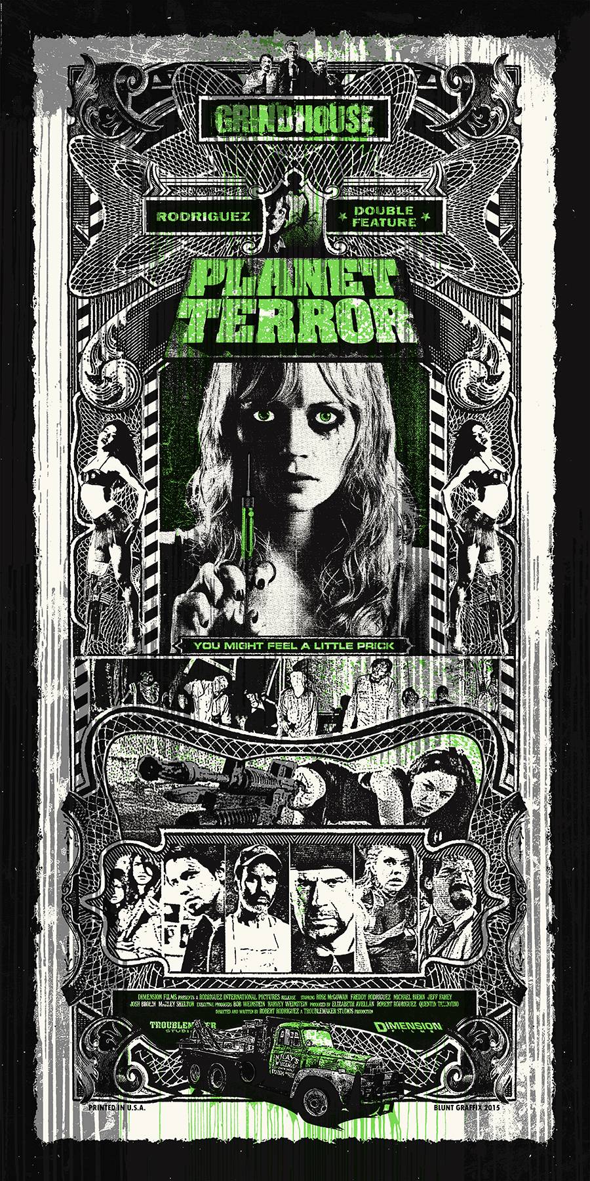
html/res/posters/EiJpCkv.jpg
