dragland/Smart_Home/html/res/posters/eoBPiSy.jpg

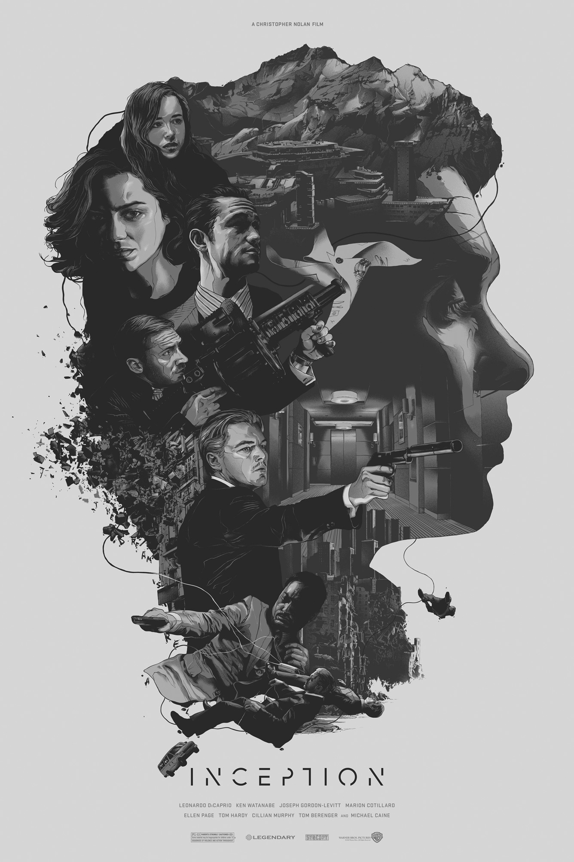
html/res/posters/eoBPiSy.jpg
