dragland/Smart_Home/html/res/posters/fsLKamg.jpg

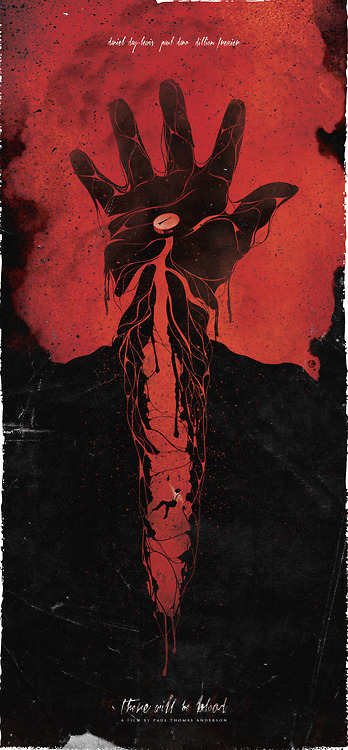
html/res/posters/fsLKamg.jpg
