dragland/Smart_Home/html/res/posters/ft5d8n32cc8y.jpg

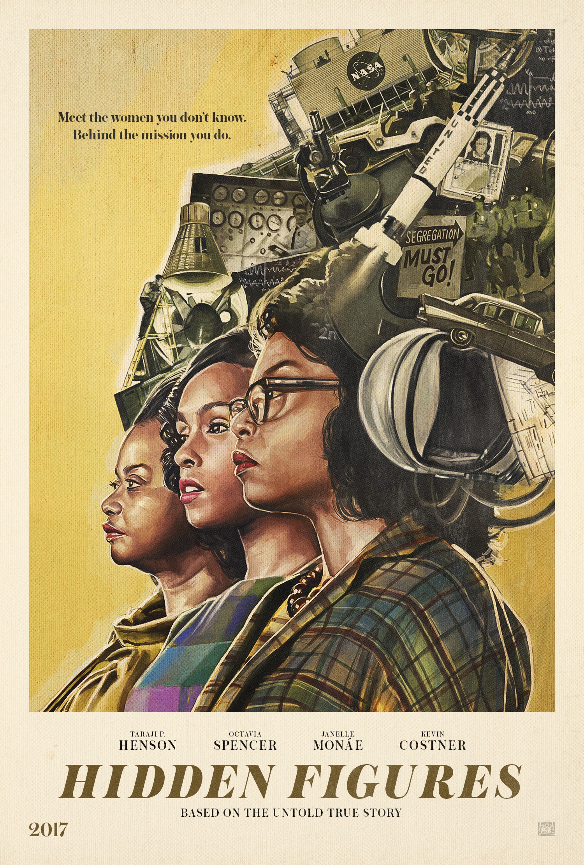
html/res/posters/ft5d8n32cc8y.jpg
