dragland/Smart_Home/html/res/posters/fWNnu.jpg

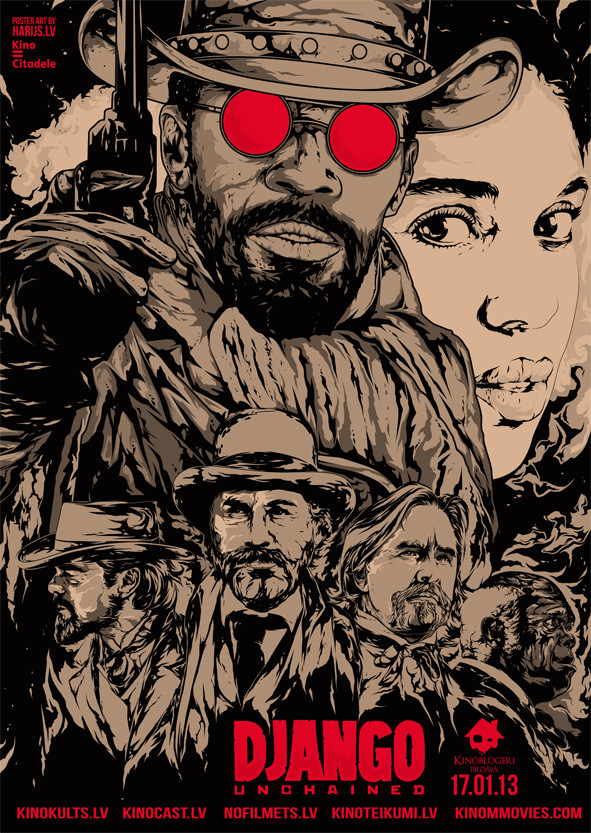
html/res/posters/fWNnu.jpg
