dragland/Smart_Home/html/res/posters/FYa5P.jpg

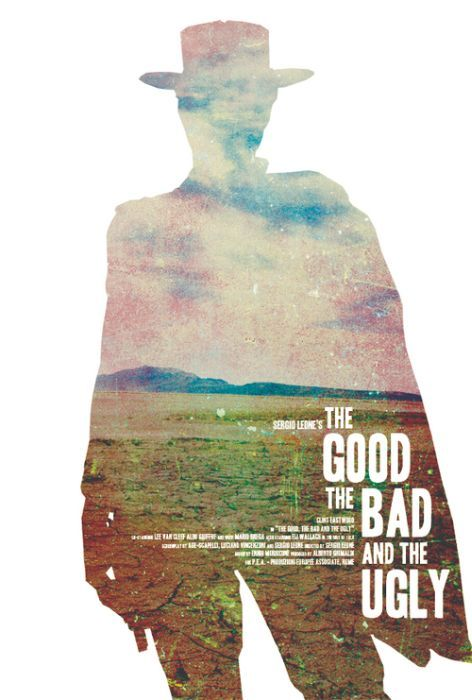
html/res/posters/FYa5P.jpg
