dragland/Smart_Home/html/res/posters/G6PXi5I.jpg

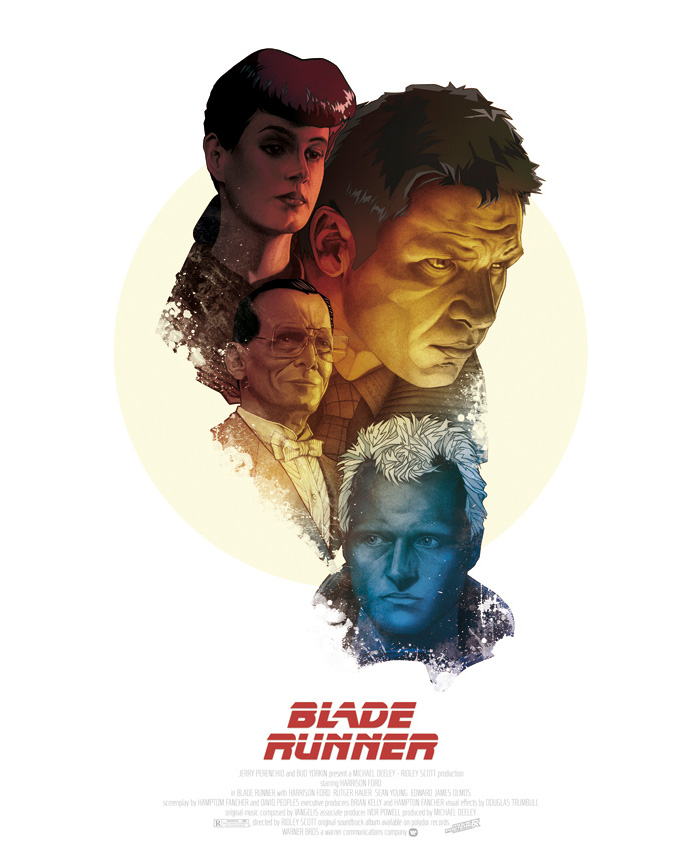
html/res/posters/G6PXi5I.jpg
