dragland/Smart_Home/html/res/posters/GJKLxiT.jpg

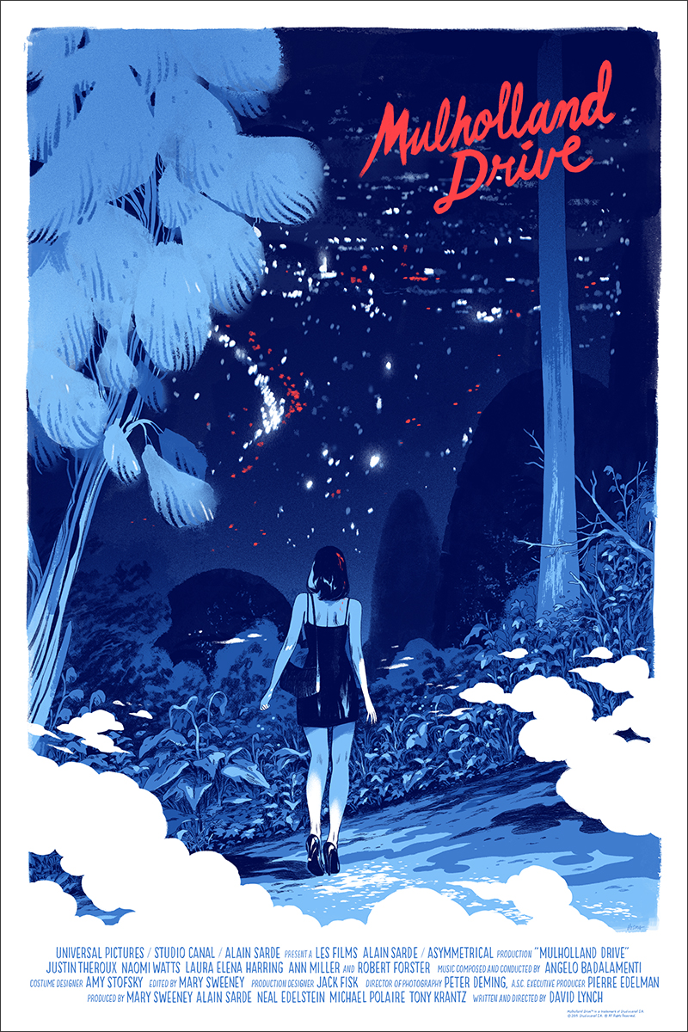
html/res/posters/GJKLxiT.jpg
