dragland/Smart_Home/html/res/posters/Gvbp0a4.jpg

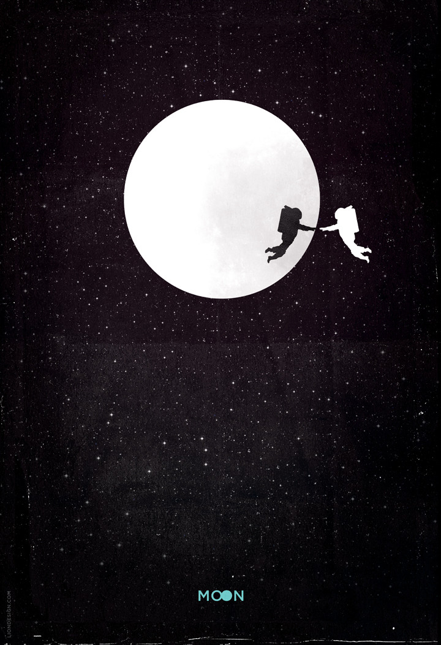
html/res/posters/Gvbp0a4.jpg
