dragland/Smart_Home/html/res/posters/h1Y3gDj.jpg

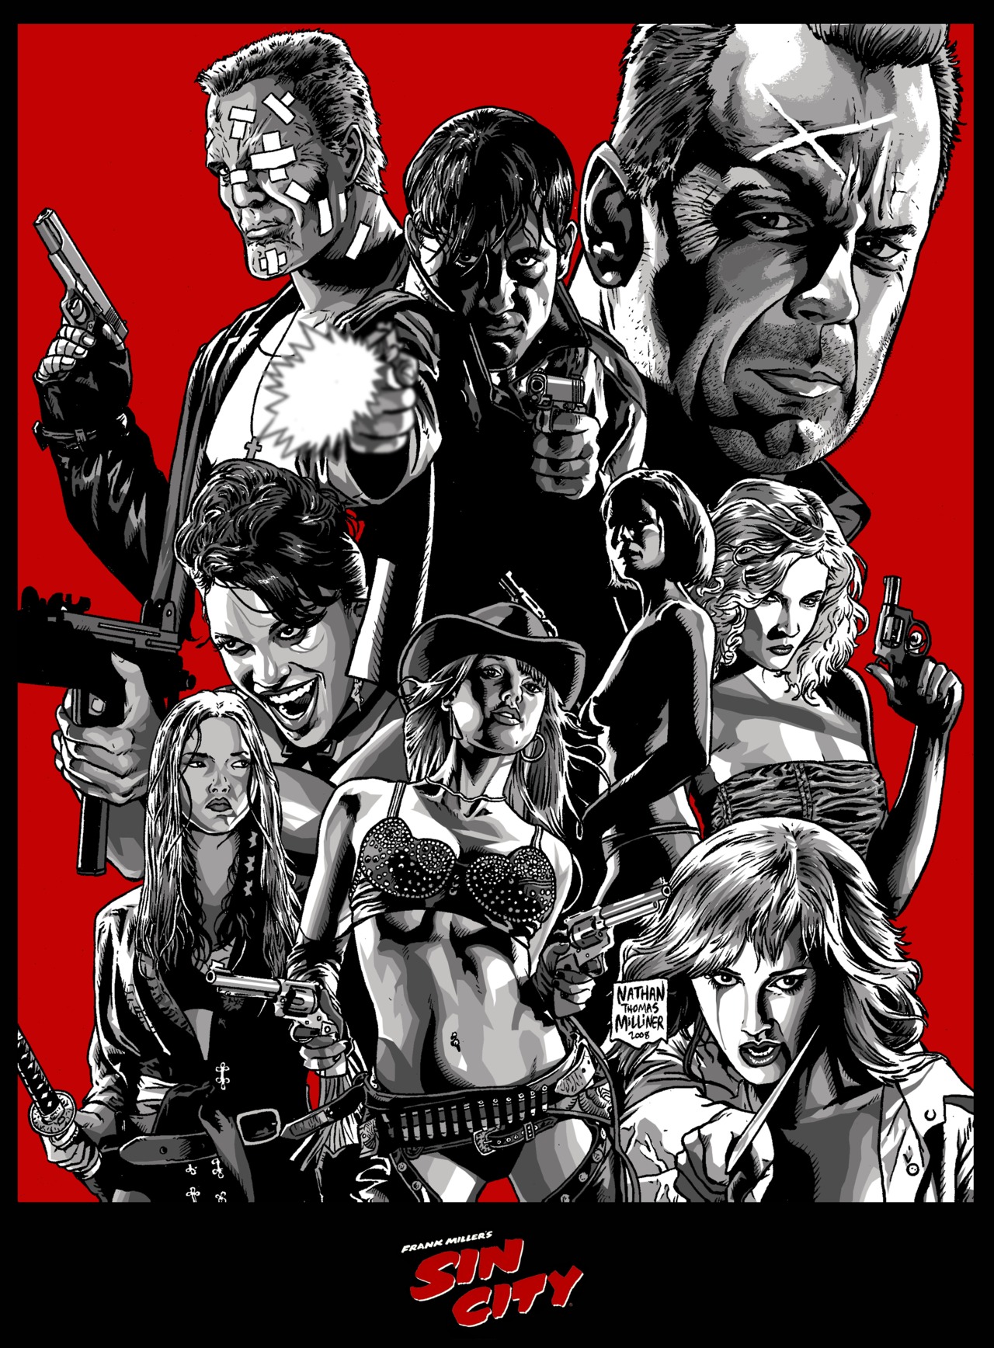
html/res/posters/h1Y3gDj.jpg
