dragland/Smart_Home/html/res/posters/H9eh8nX.gif

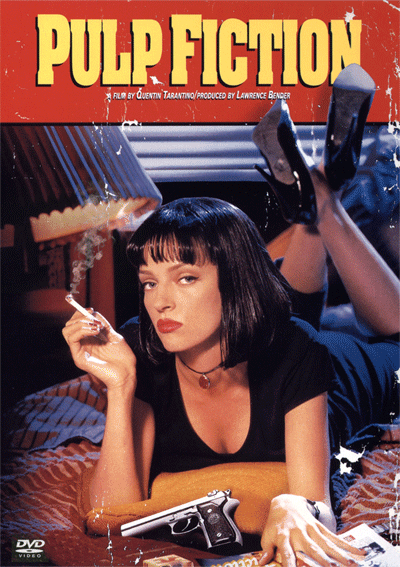
html/res/posters/H9eh8nX.gif
