dragland/Smart_Home/html/res/posters/H9QEdws.jpg

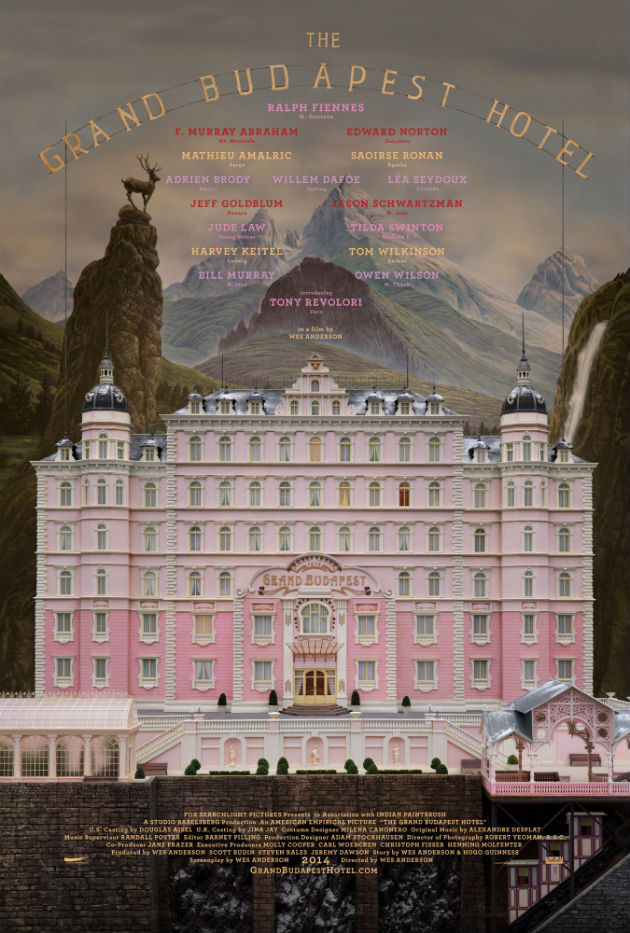
html/res/posters/H9QEdws.jpg
