dragland/Smart_Home/html/res/posters/HIXZ555.jpg

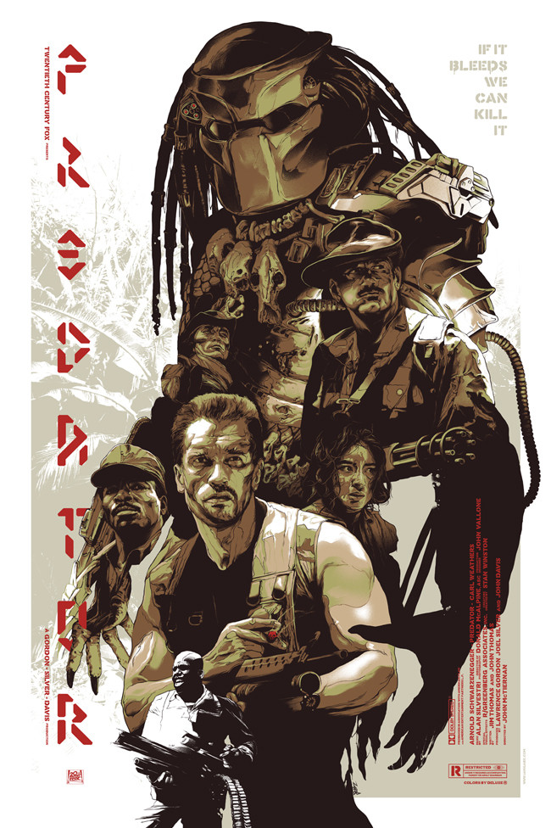
html/res/posters/HIXZ555.jpg
