dragland/Smart_Home/html/res/posters/i9yurd7dcoax.png

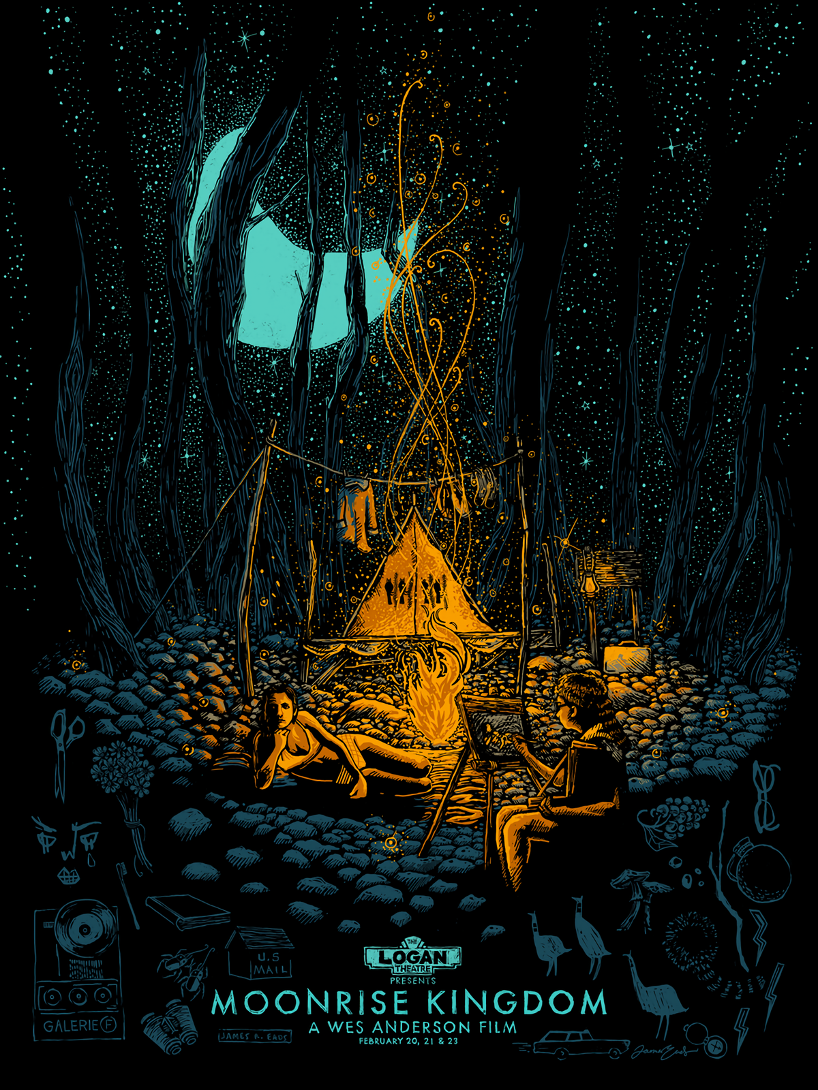
html/res/posters/i9yurd7dcoax.png
