dragland/Smart_Home/html/res/posters/IayzdsU.jpg

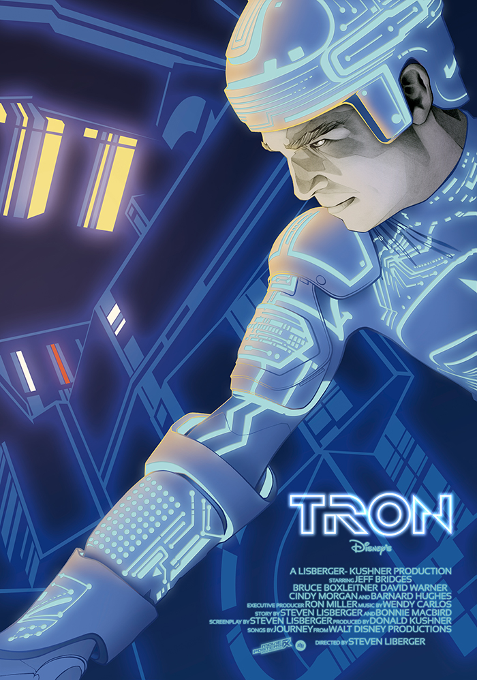
html/res/posters/IayzdsU.jpg
