dragland/Smart_Home/html/res/posters/iSyJcBR.jpg

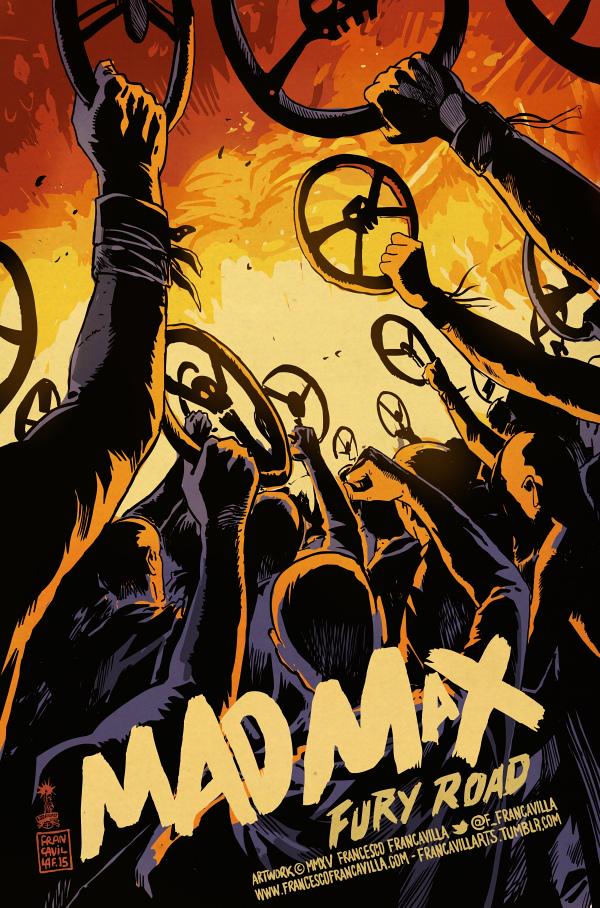
html/res/posters/iSyJcBR.jpg
