dragland/Smart_Home/html/res/posters/j4nu1c6sus1y.jpg

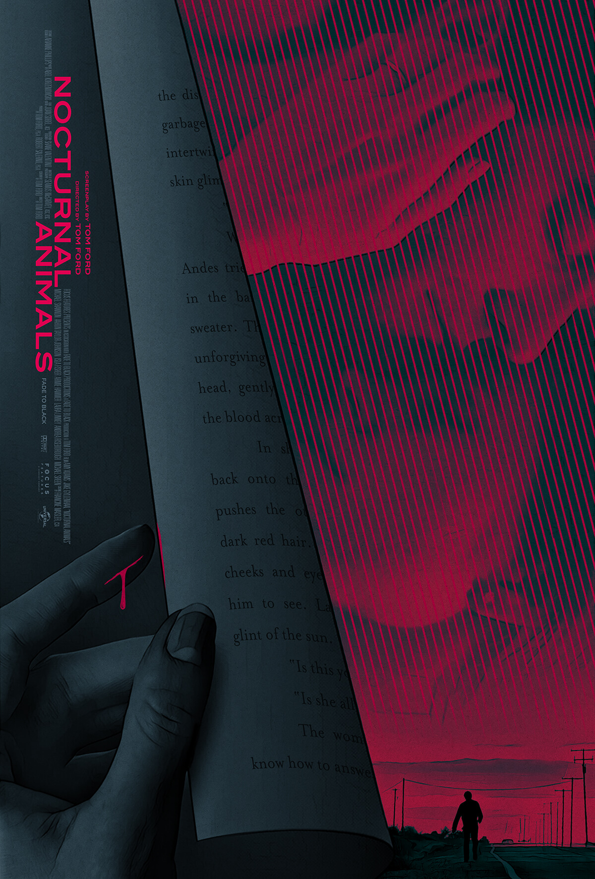
html/res/posters/j4nu1c6sus1y.jpg
