dragland/Smart_Home/html/res/posters/jg7p8ejho2jy.png

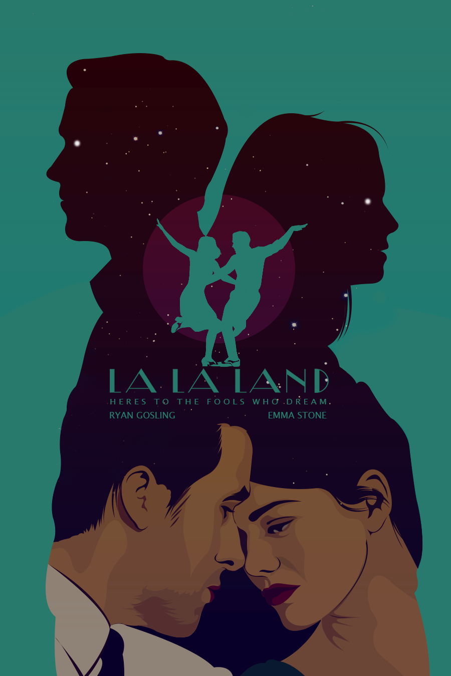
html/res/posters/jg7p8ejho2jy.png
