dragland/Smart_Home/html/res/posters/jlagk5pa3jdy.png

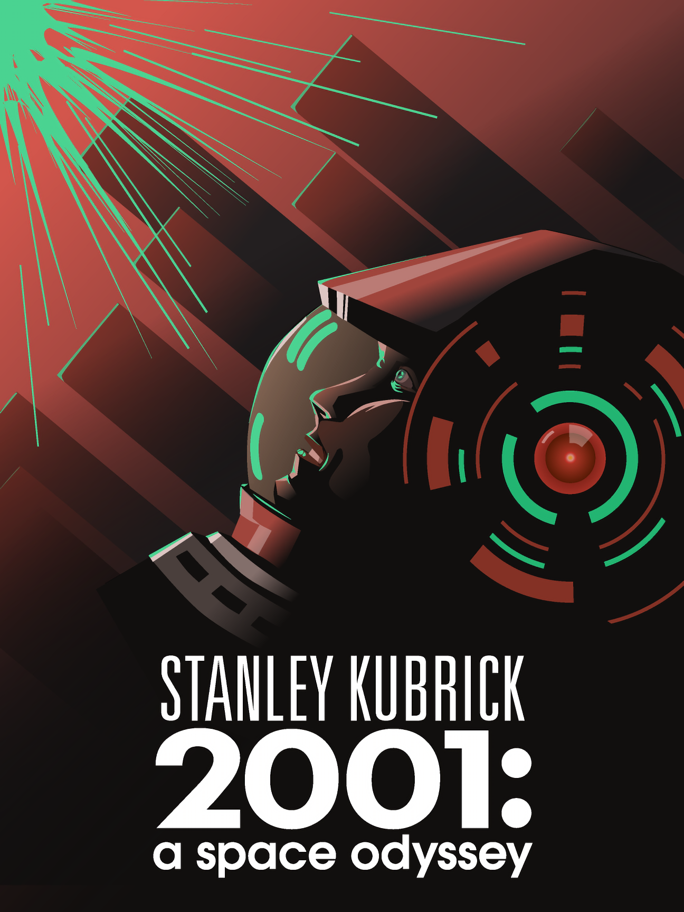
html/res/posters/jlagk5pa3jdy.png
