dragland/Smart_Home/html/res/posters/jrPekYr.jpg

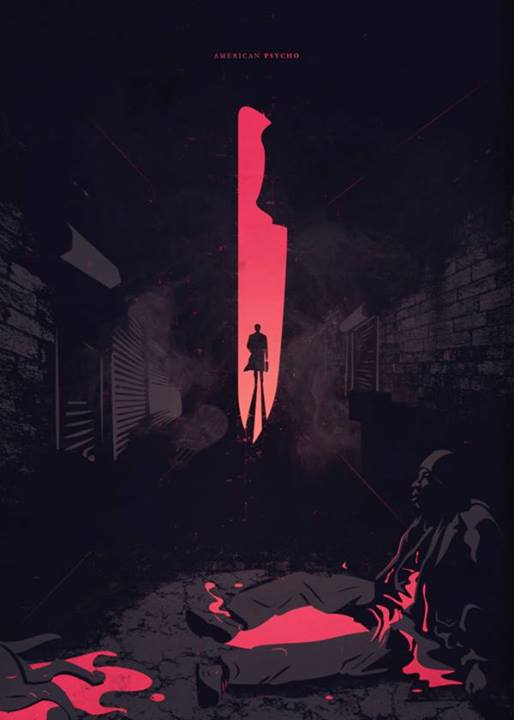
html/res/posters/jrPekYr.jpg
