dragland/Smart_Home/html/res/posters/jSOY6bm.jpg

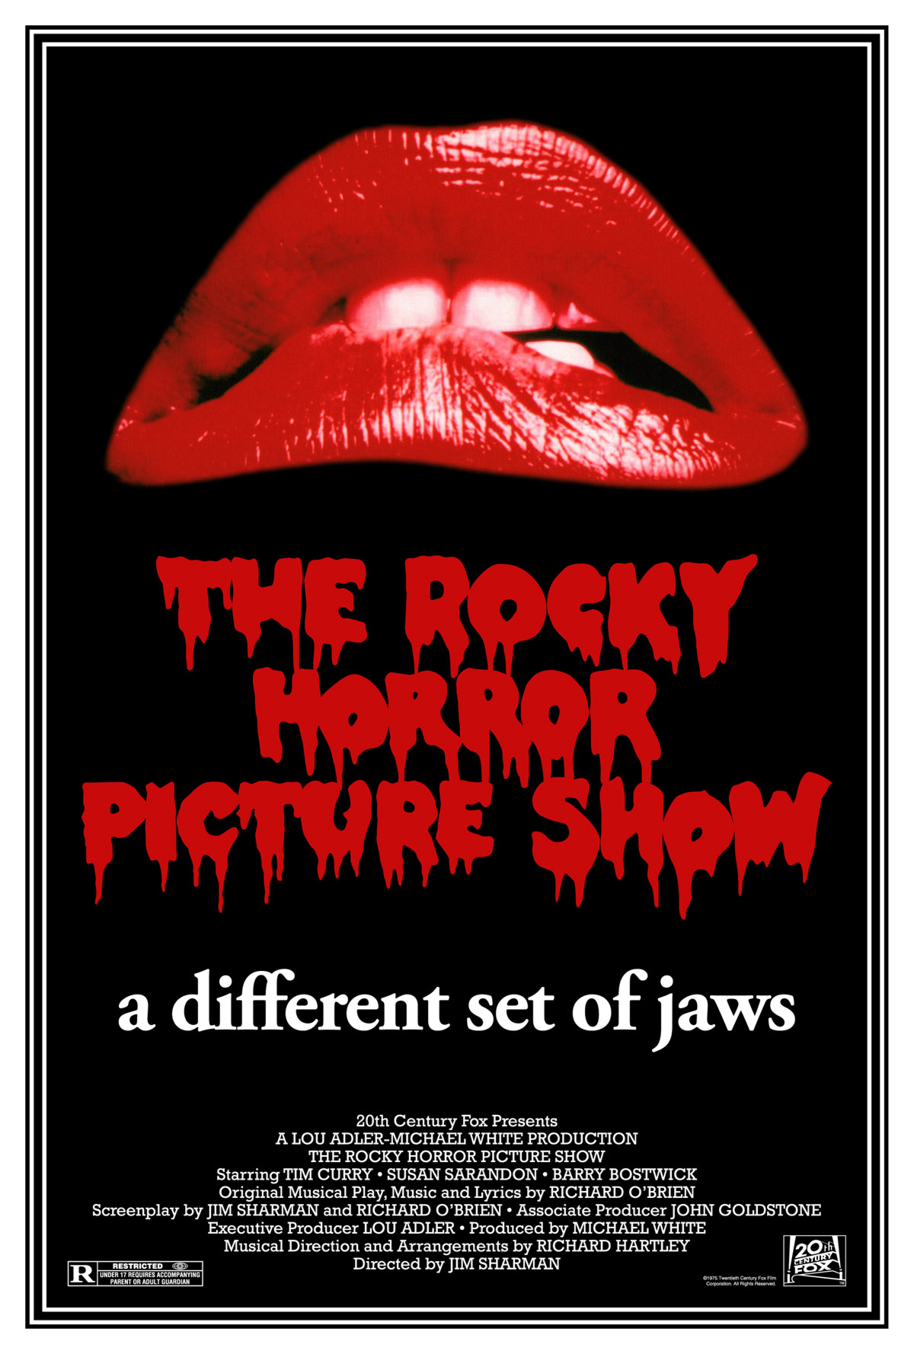
html/res/posters/jSOY6bm.jpg
