dragland/Smart_Home/html/res/posters/k1ymewv7o57y.png

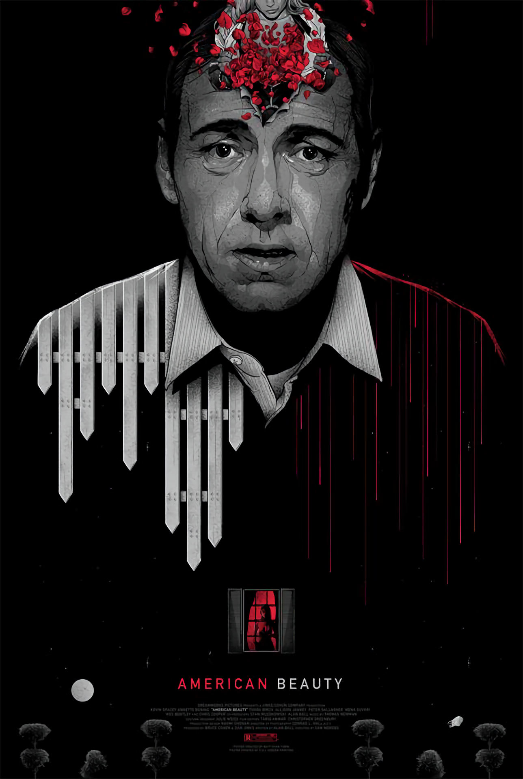
html/res/posters/k1ymewv7o57y.png
