dragland/Smart_Home/html/res/posters/KjG7f.jpg

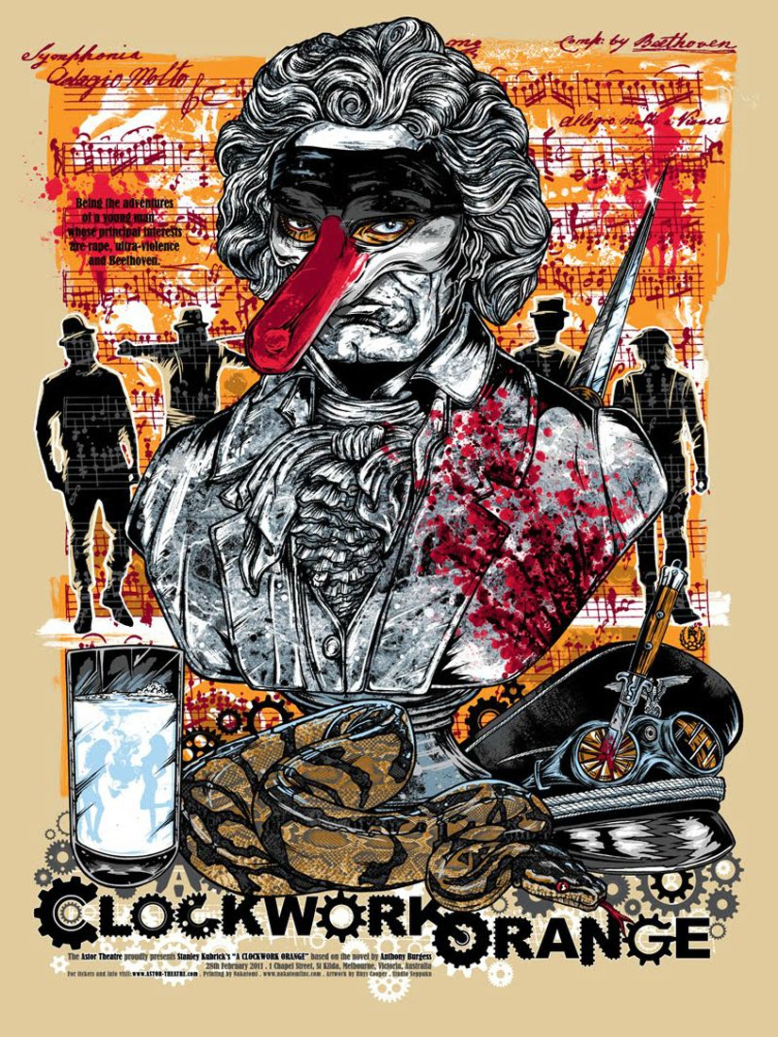
html/res/posters/KjG7f.jpg
