dragland/Smart_Home/html/res/posters/kRW9NBC.jpg

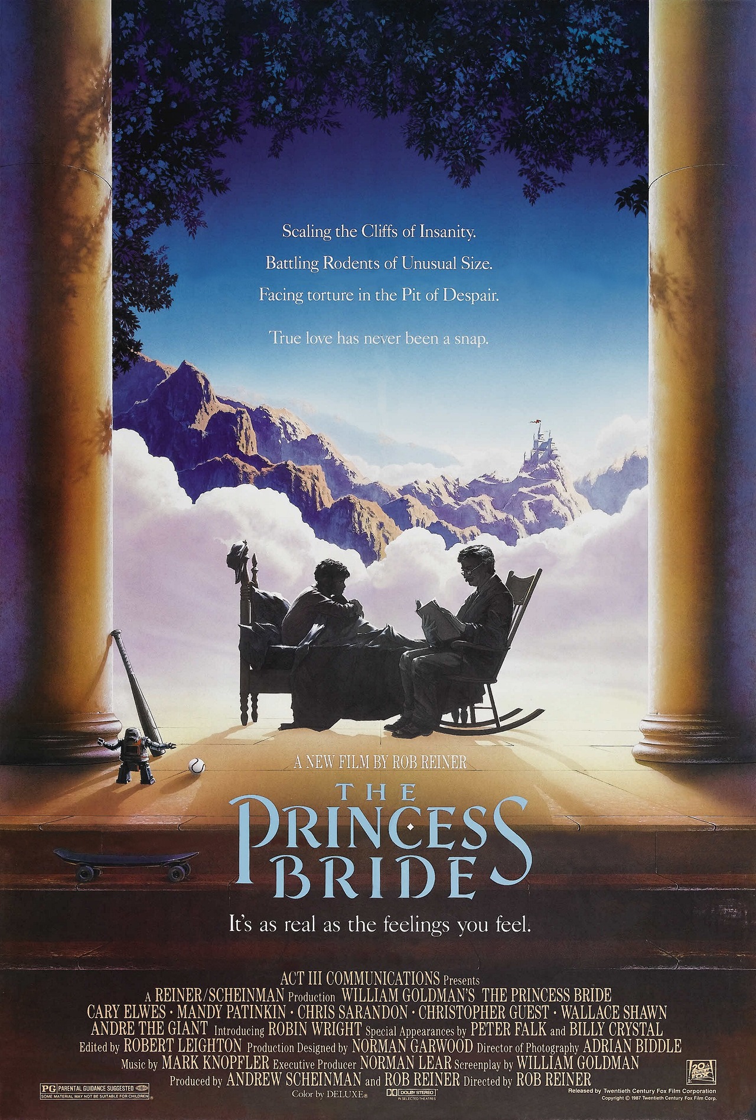
html/res/posters/kRW9NBC.jpg
