dragland/Smart_Home/html/res/posters/l4dNg92.png

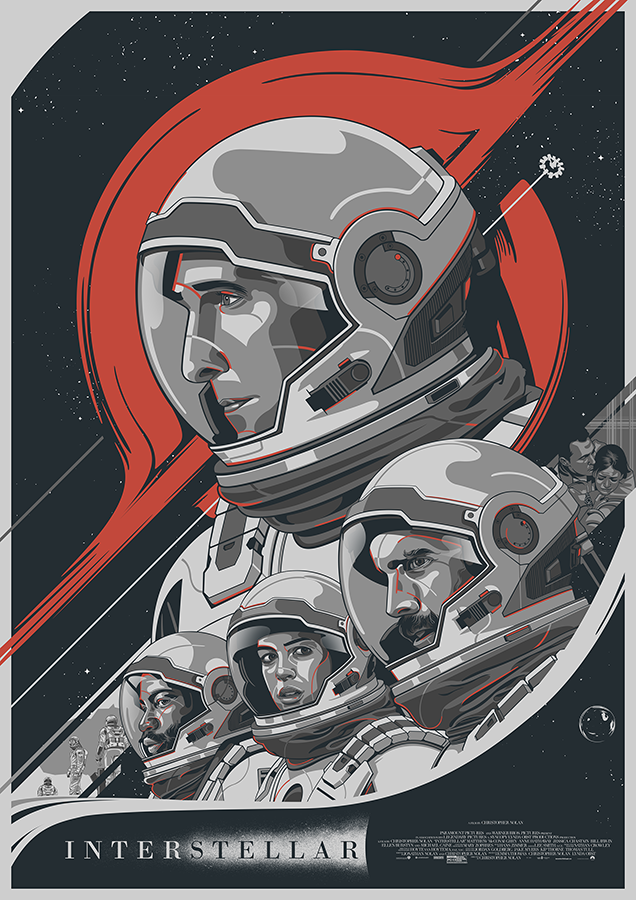
html/res/posters/l4dNg92.png
