dragland/Smart_Home/html/res/posters/Lj0V0Cz.jpg

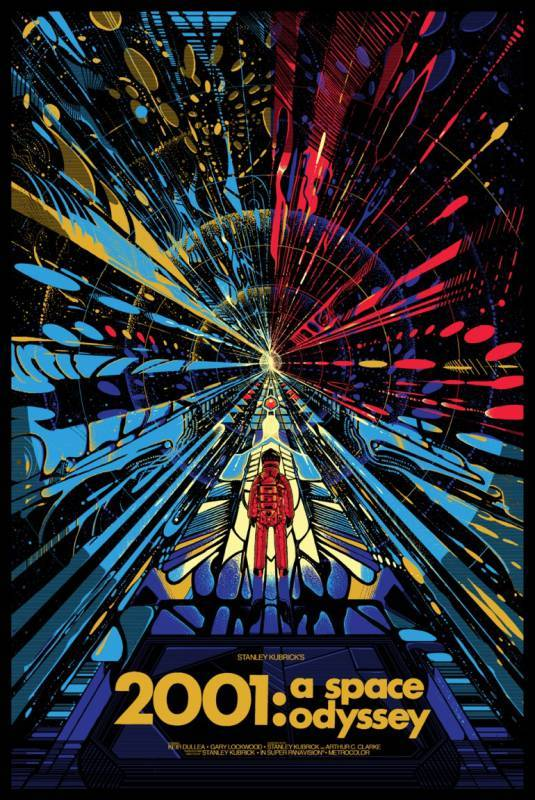
html/res/posters/Lj0V0Cz.jpg
