dragland/Smart_Home/html/res/posters/lj4v47jknwey.jpg

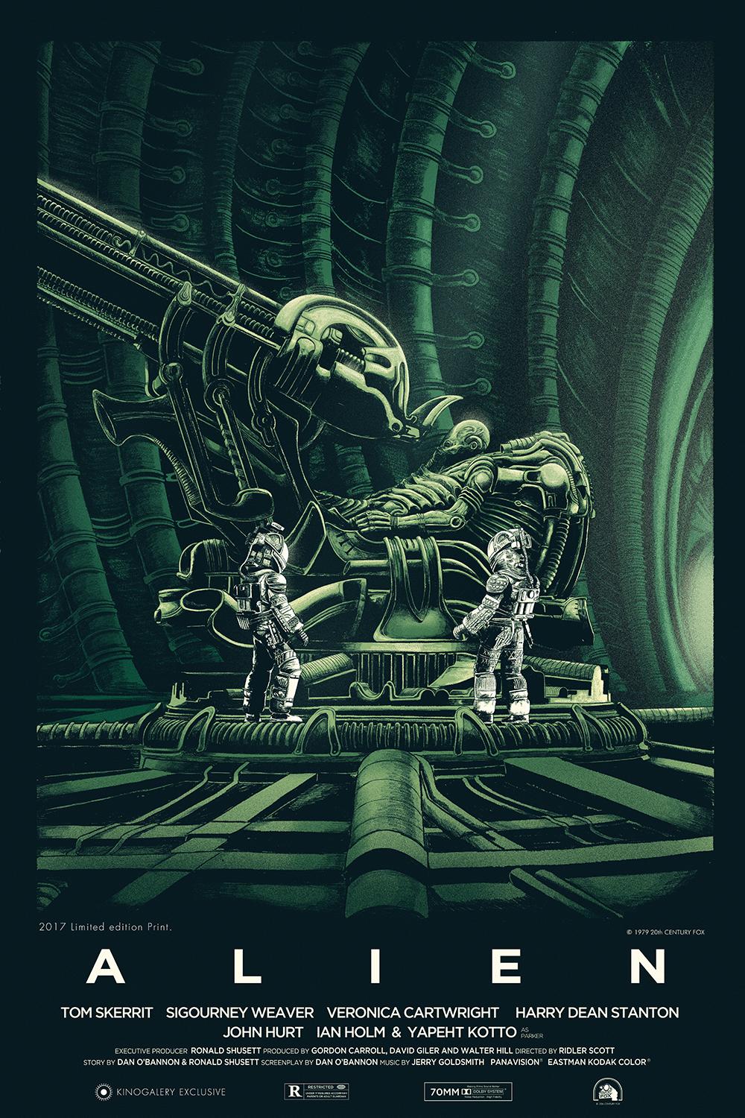
html/res/posters/lj4v47jknwey.jpg
