dragland/Smart_Home/html/res/posters/lM9YZmy.png

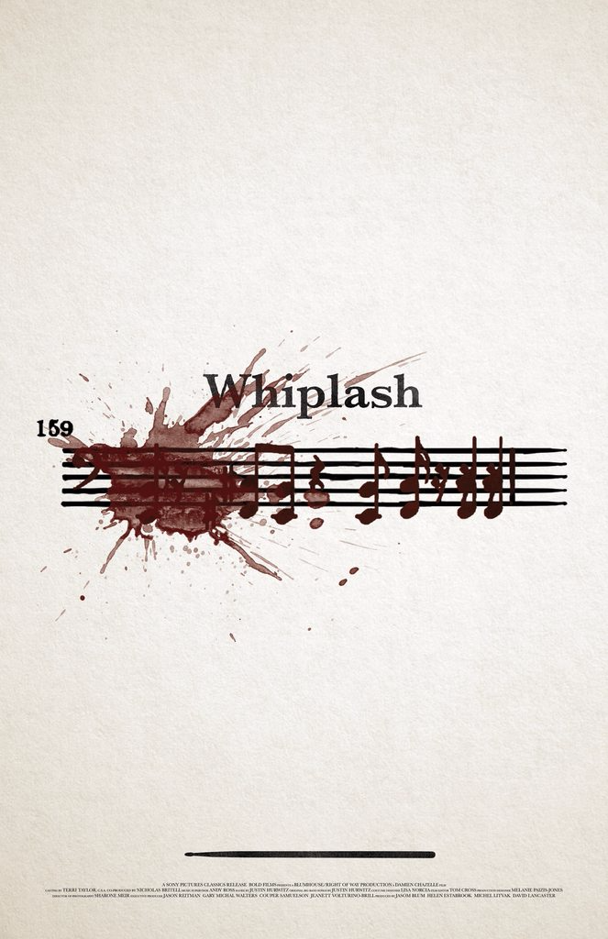
html/res/posters/lM9YZmy.png
