dragland/Smart_Home/html/res/posters/loa2pgzrpvey.png

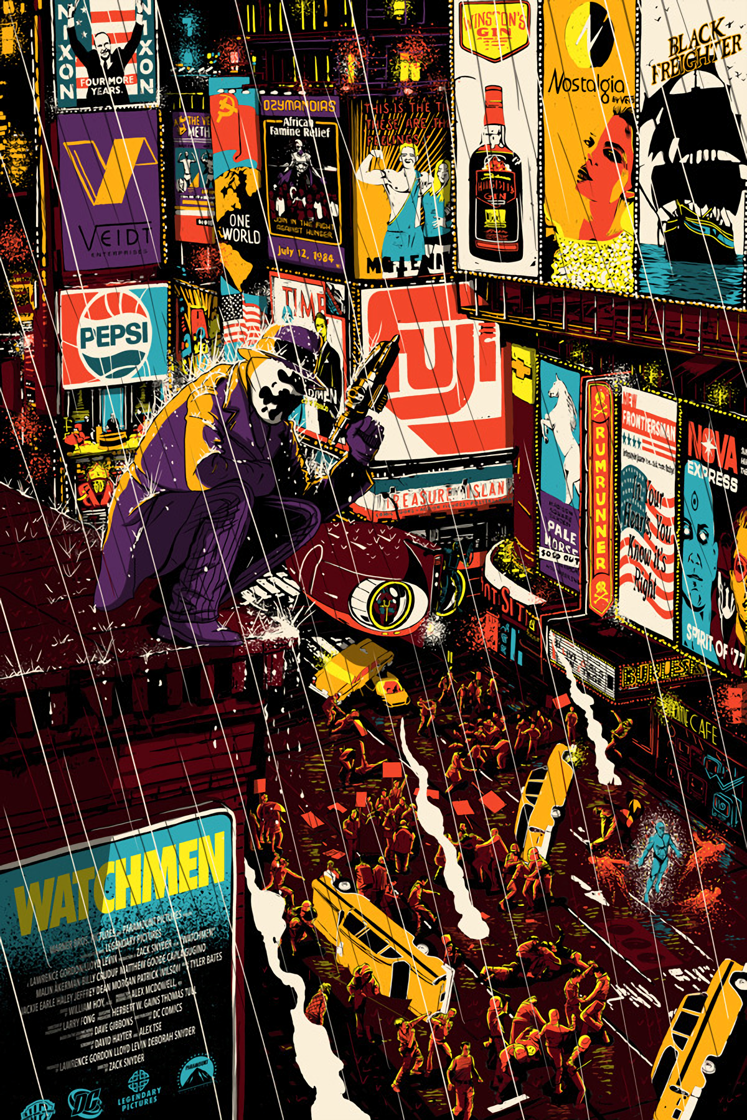
html/res/posters/loa2pgzrpvey.png
