dragland/Smart_Home/html/res/posters/M1AJgg5.jpg

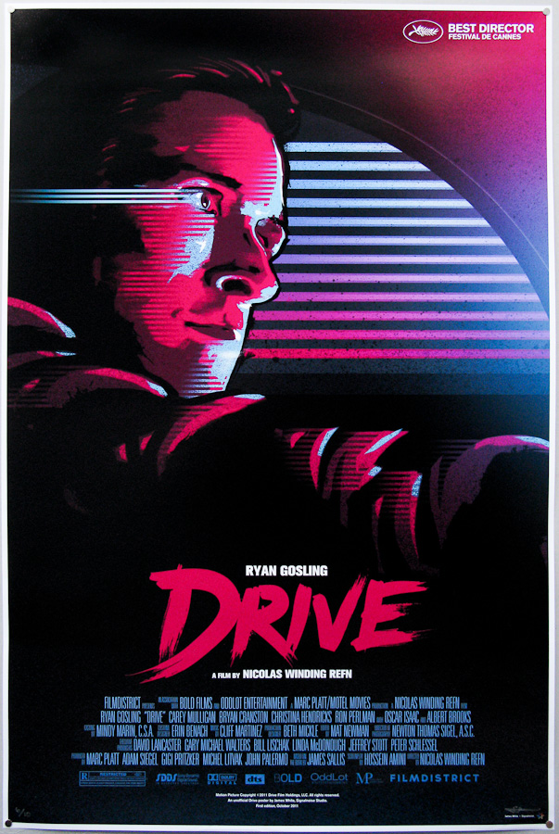
html/res/posters/M1AJgg5.jpg
