dragland/Smart_Home/html/res/posters/Mneb8ix.jpg

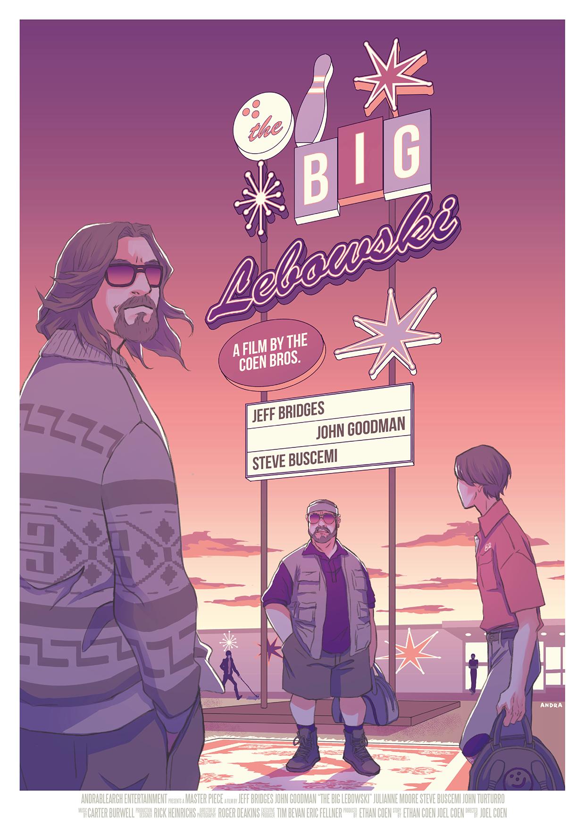
html/res/posters/Mneb8ix.jpg
