dragland/Smart_Home/html/res/posters/MW7zGto.jpg

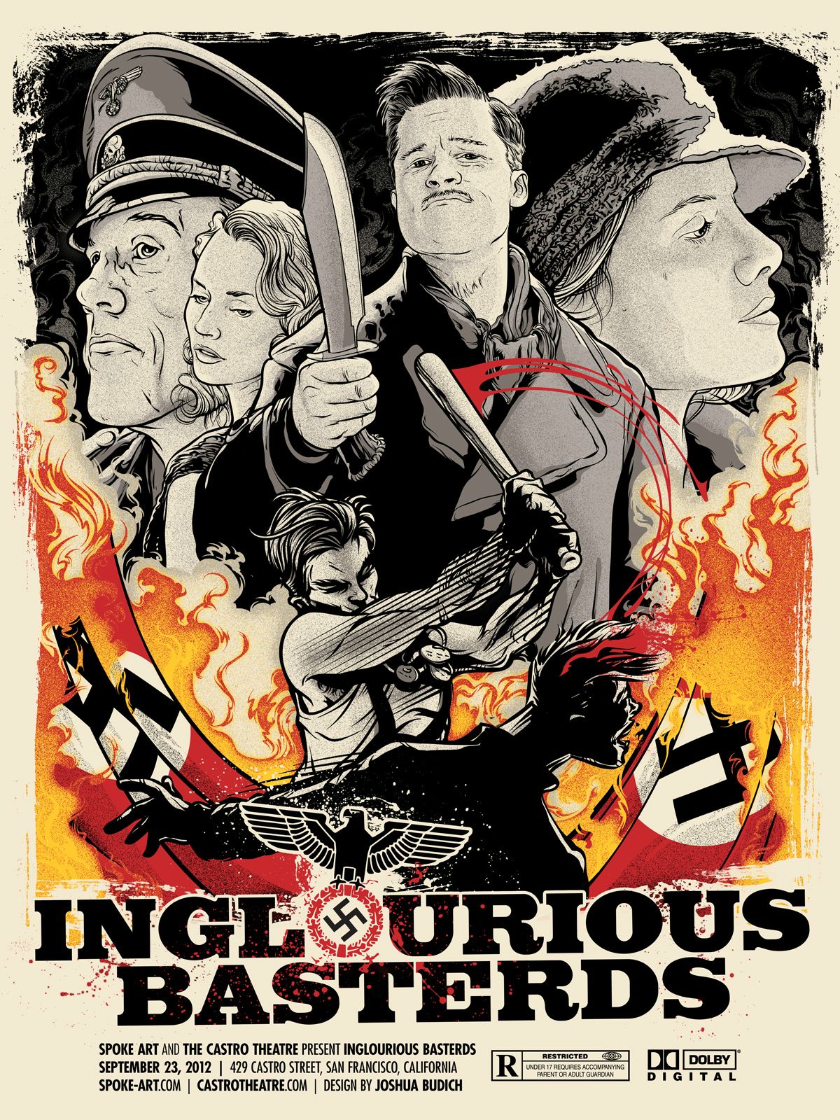
html/res/posters/MW7zGto.jpg
