dragland/Smart_Home/html/res/posters/n6zwmr11m7zz.jpg

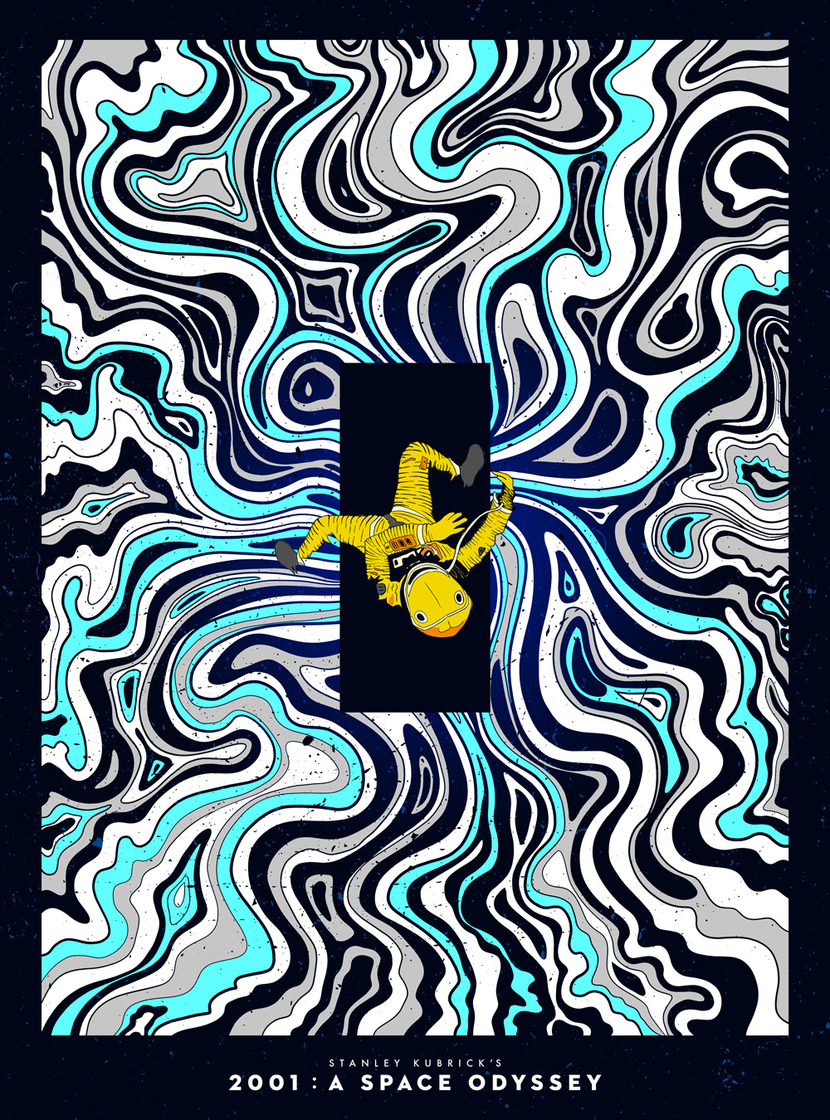
html/res/posters/n6zwmr11m7zz.jpg
