dragland/Smart_Home/html/res/posters/NC4CACC.jpg

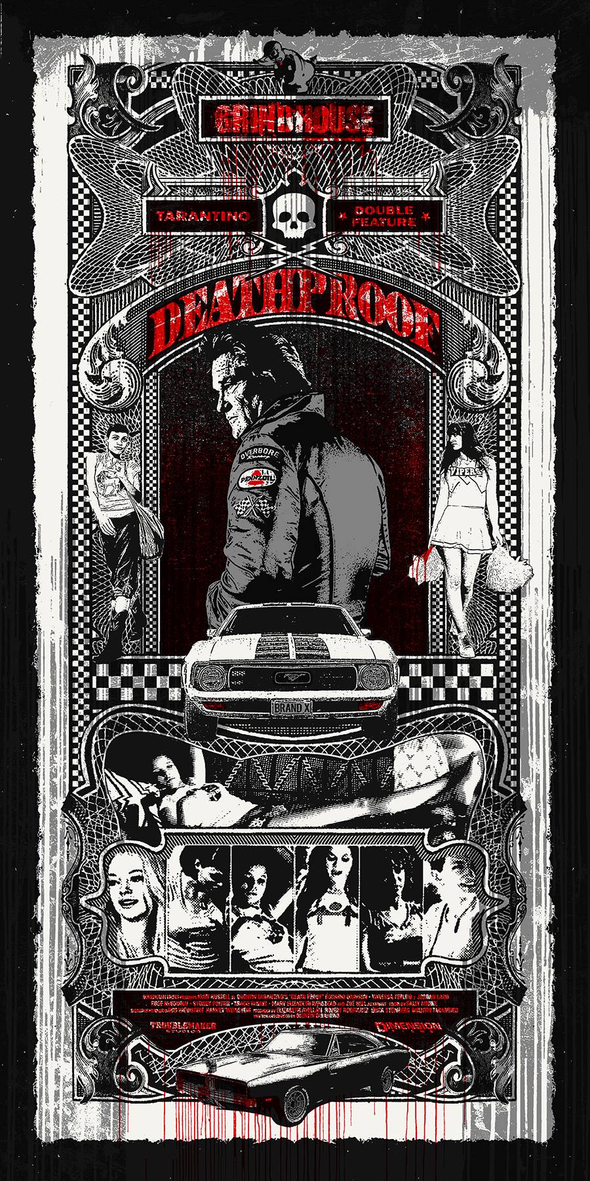
html/res/posters/NC4CACC.jpg
