dragland/Smart_Home/html/res/posters/O34HziE.jpg

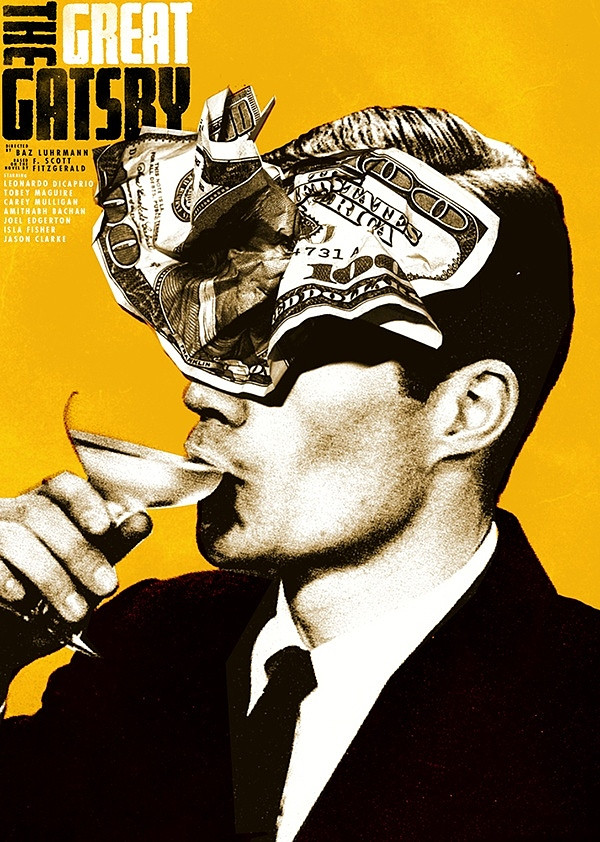
html/res/posters/O34HziE.jpg
