dragland/Smart_Home/html/res/posters/Od0Do.jpg

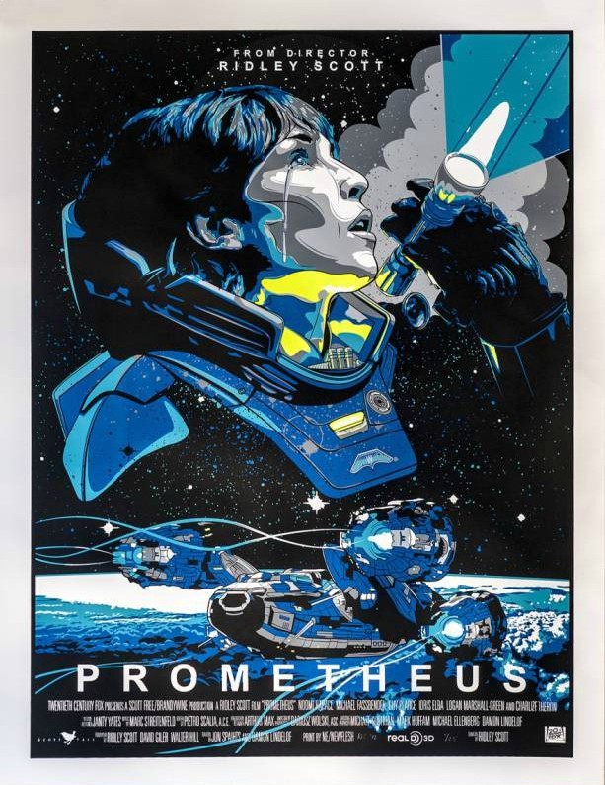
html/res/posters/Od0Do.jpg
