dragland/Smart_Home/html/res/posters/p8py6b9vho9x.png

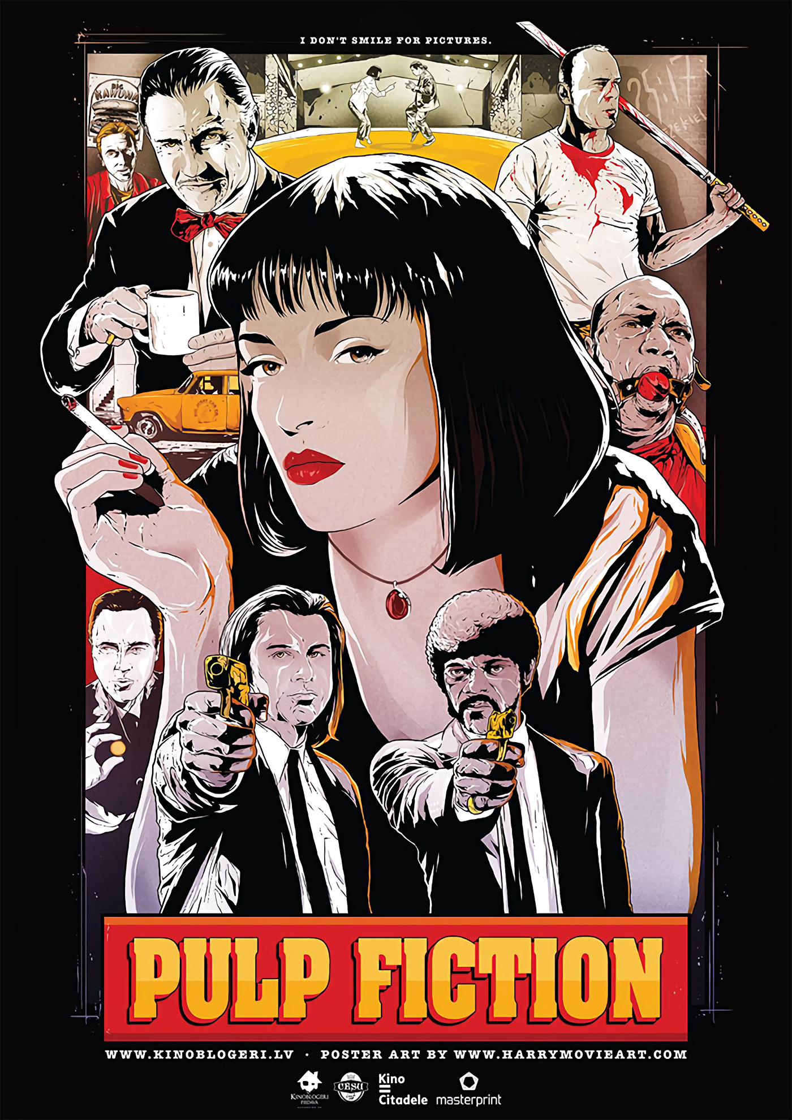
html/res/posters/p8py6b9vho9x.png
