dragland/Smart_Home/html/res/posters/P811zZE.jpg

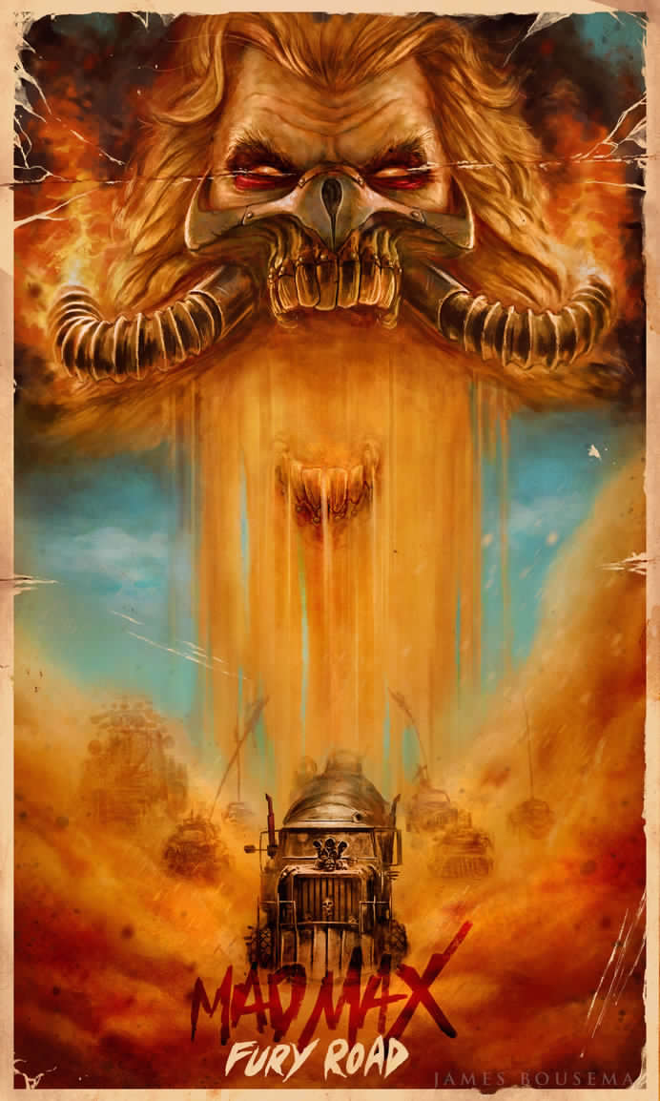
html/res/posters/P811zZE.jpg
