dragland/Smart_Home/html/res/posters/pcEMZ69.jpg

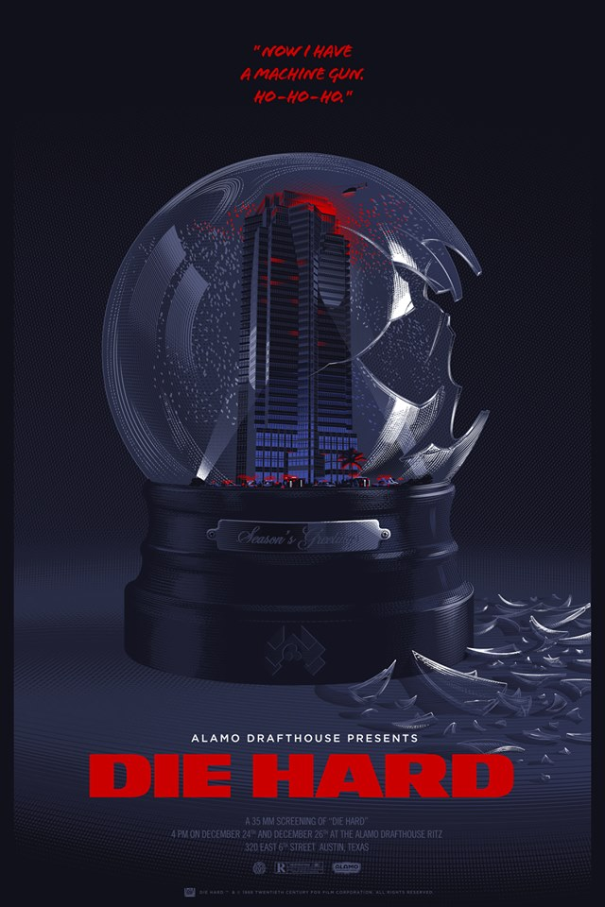
html/res/posters/pcEMZ69.jpg
