dragland/Smart_Home/html/res/posters/PI8g1Lt.gif

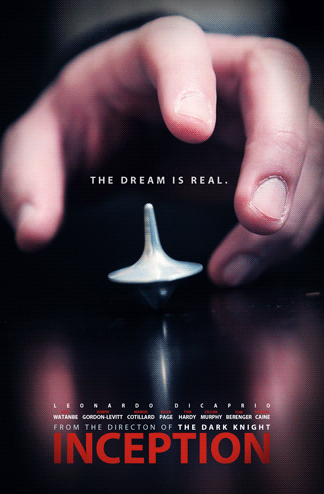
html/res/posters/PI8g1Lt.gif
