dragland/Smart_Home/html/res/posters/Q7G64Ux.jpg

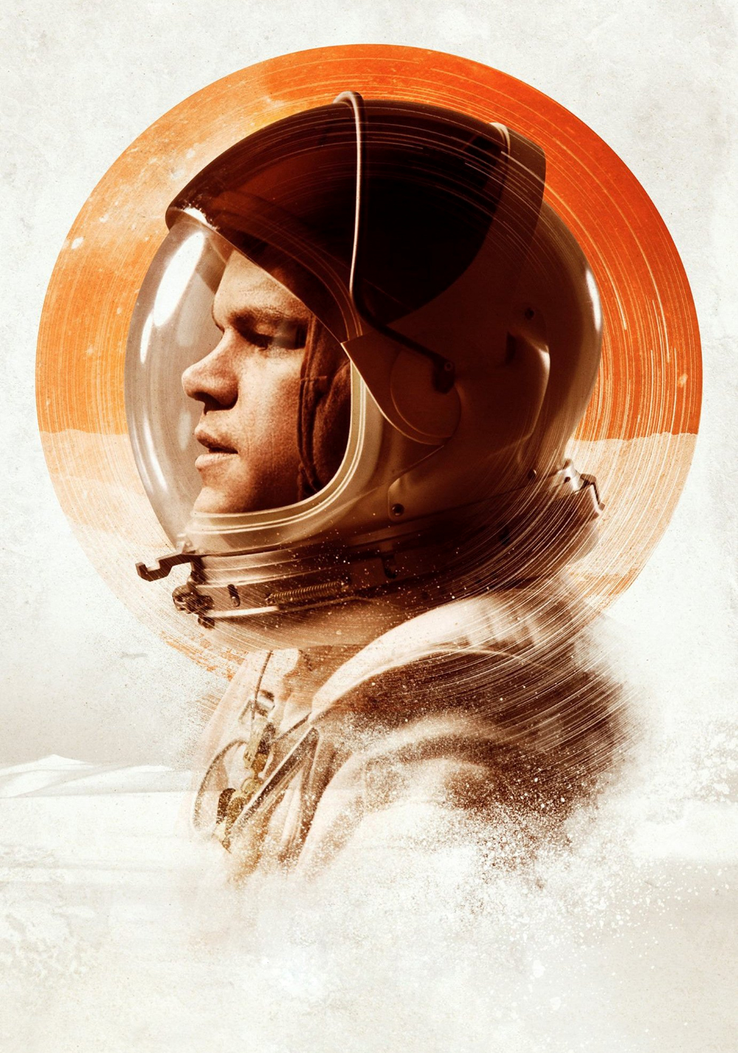
html/res/posters/Q7G64Ux.jpg
