dragland/Smart_Home/html/res/posters/Q9TdXEM.jpg

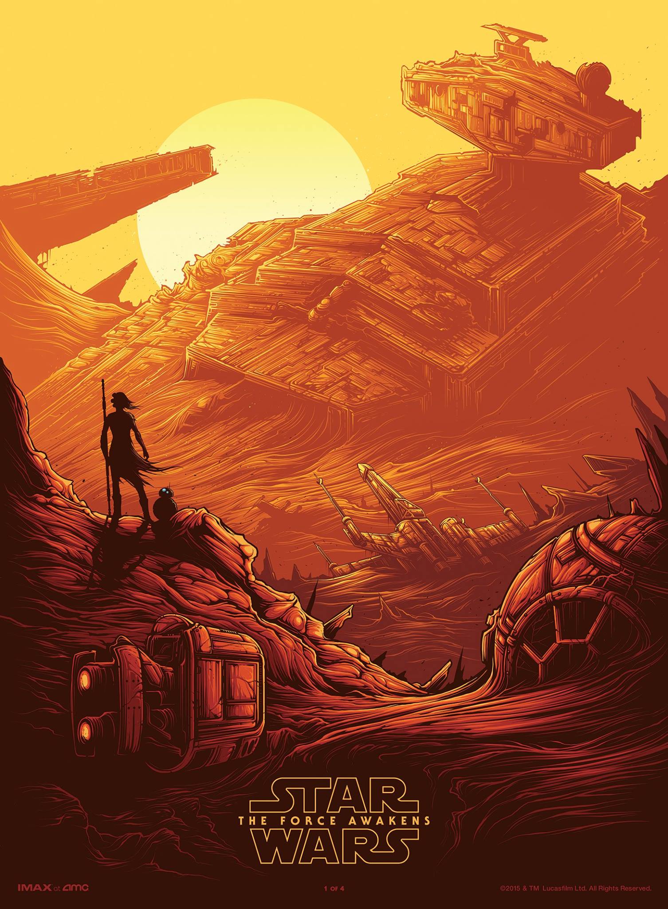
html/res/posters/Q9TdXEM.jpg
