dragland/Smart_Home/html/res/posters/qbldpt1hs3sx.jpg

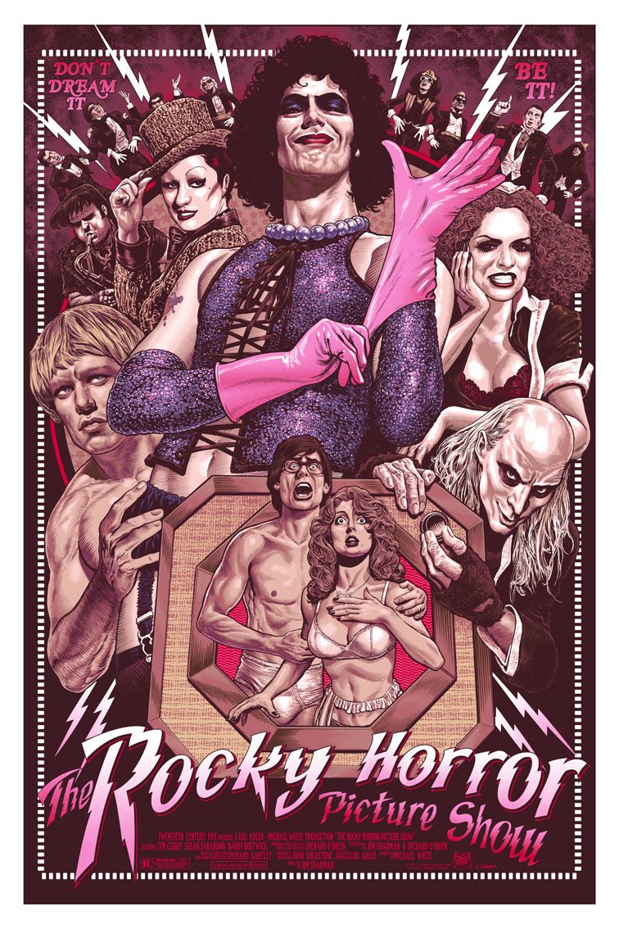
html/res/posters/qbldpt1hs3sx.jpg
