dragland/Smart_Home/html/res/posters/QDNsG.jpg

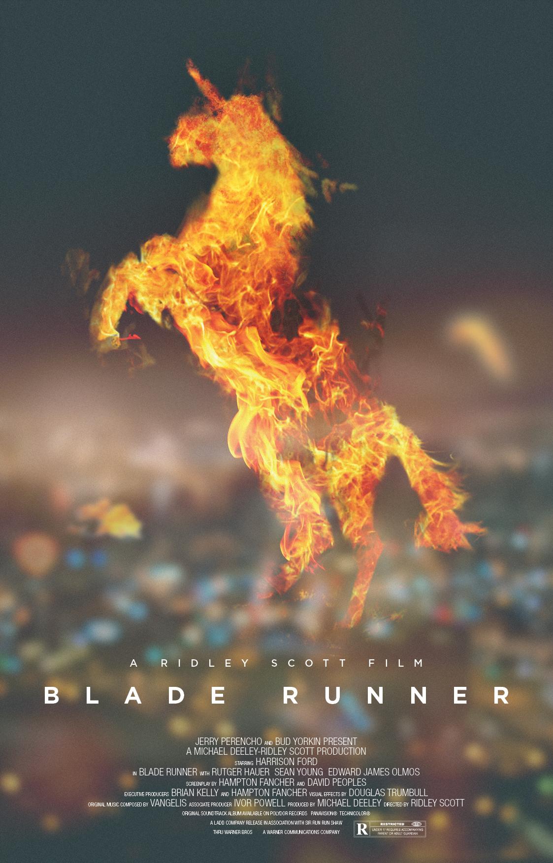
html/res/posters/QDNsG.jpg
