dragland/Smart_Home/html/res/posters/r1ign8w4onbx.png

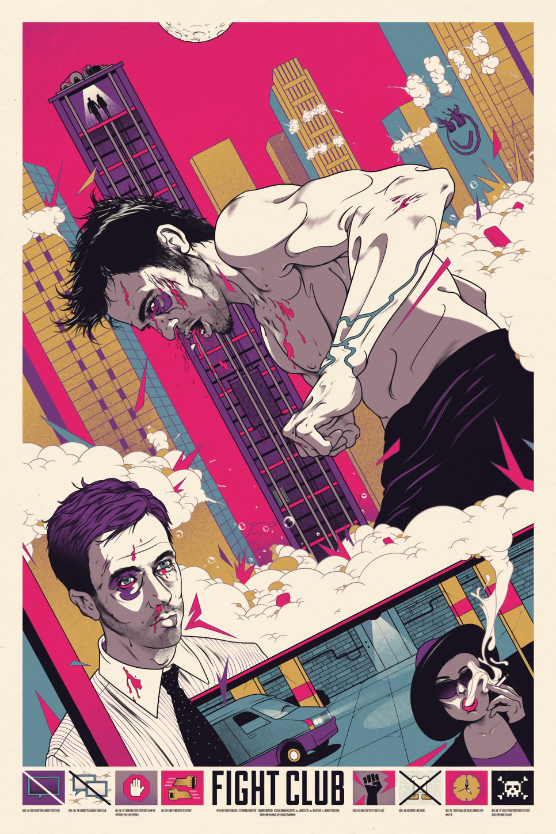
html/res/posters/r1ign8w4onbx.png
