dragland/Smart_Home/html/res/posters/RIAQVu8.jpg

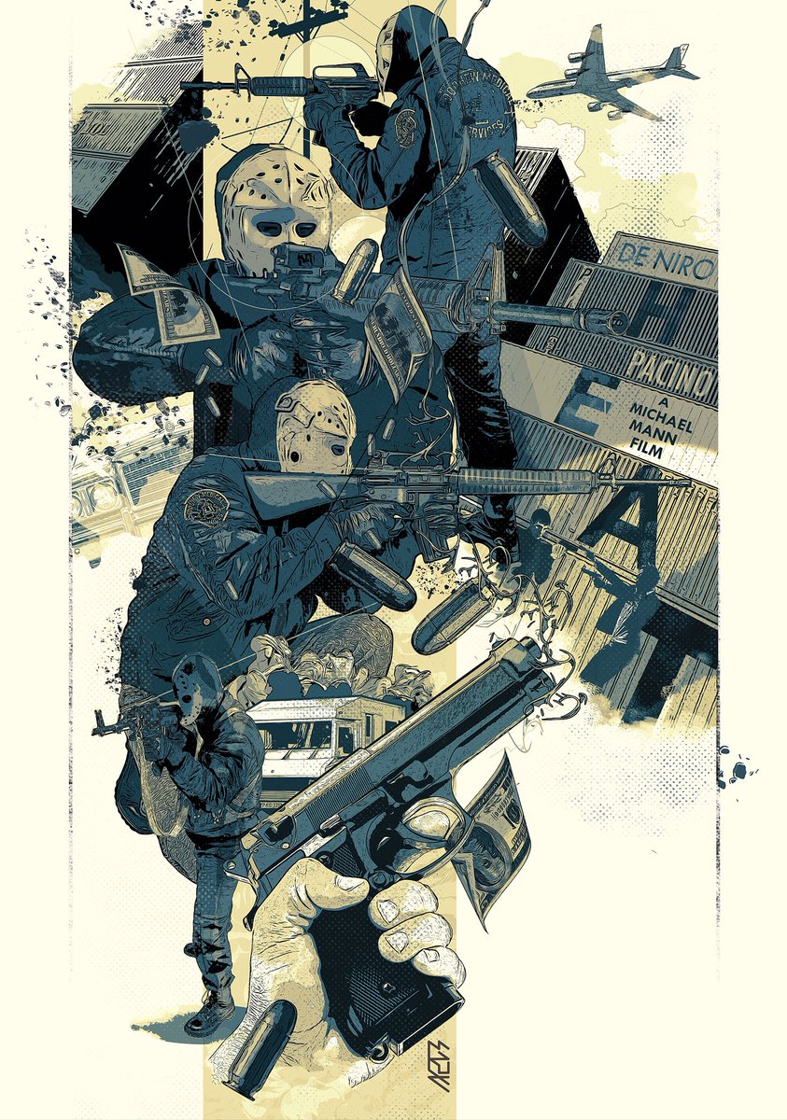
html/res/posters/RIAQVu8.jpg
