dragland/Smart_Home/html/res/posters/RP7rS.jpg

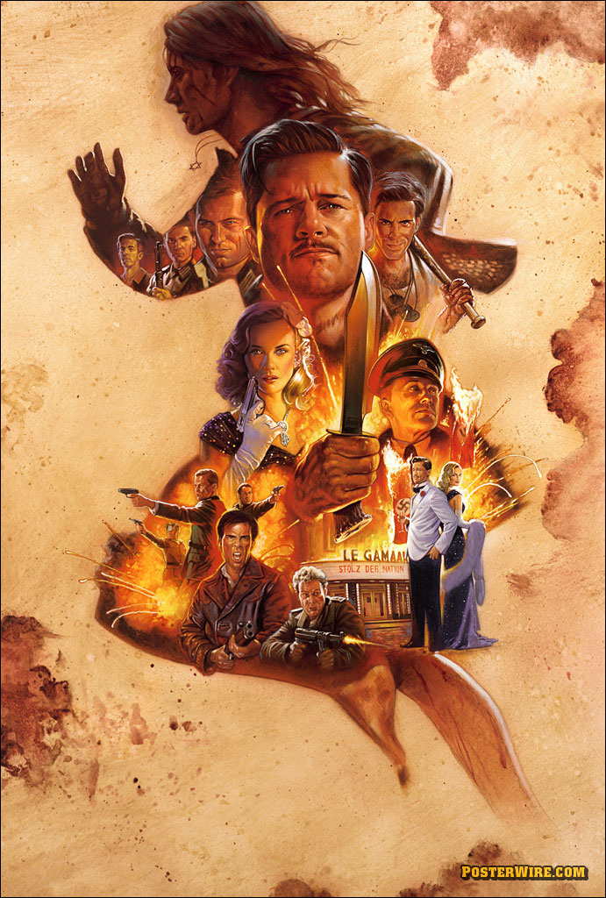
html/res/posters/RP7rS.jpg
