dragland/Smart_Home/html/res/posters/rPbIPAP.jpg

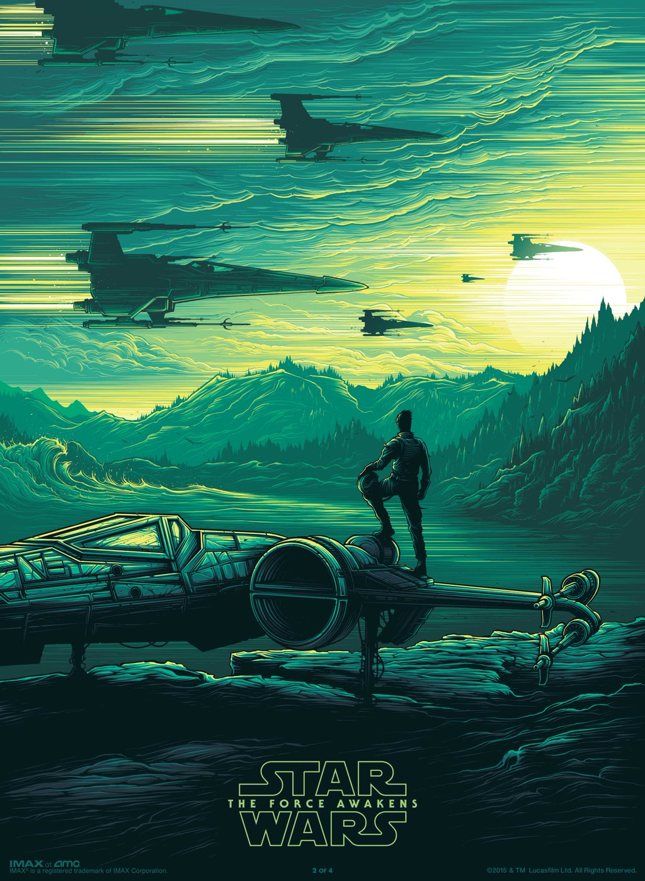
html/res/posters/rPbIPAP.jpg
