dragland/Smart_Home/html/res/posters/RQq9jie.jpg

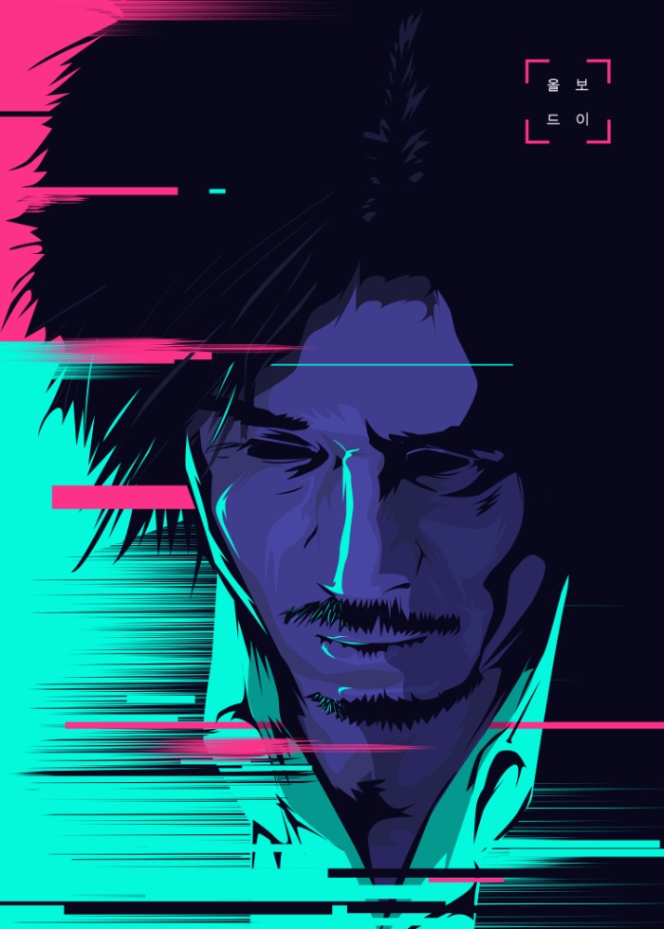
html/res/posters/RQq9jie.jpg
