dragland/Smart_Home/html/res/posters/RSO7sOE.jpg

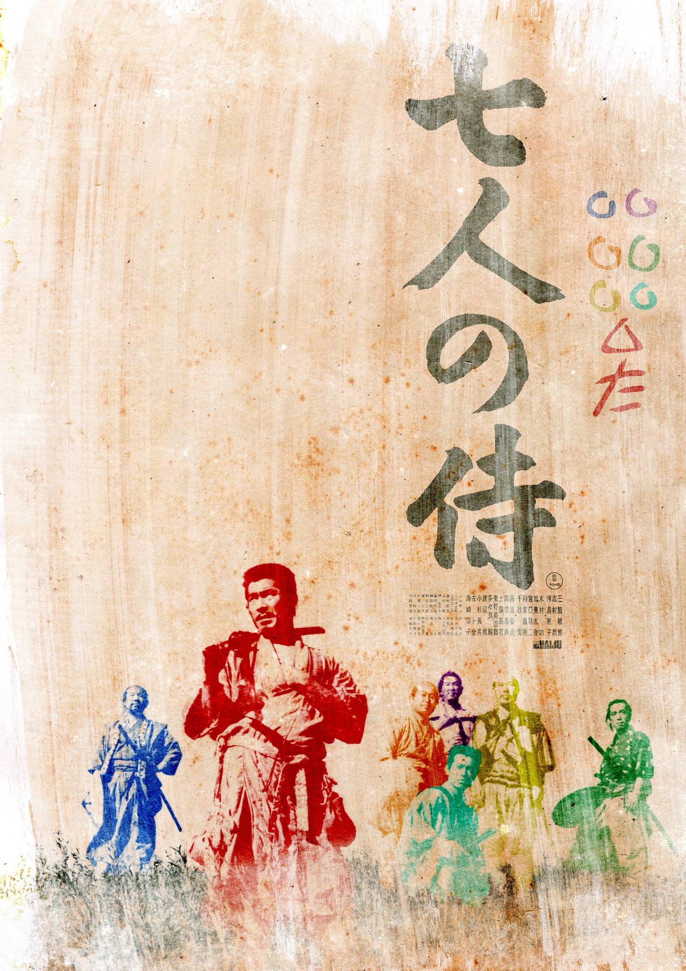
html/res/posters/RSO7sOE.jpg
