dragland/Smart_Home/html/res/posters/S3RDN3Z.jpg

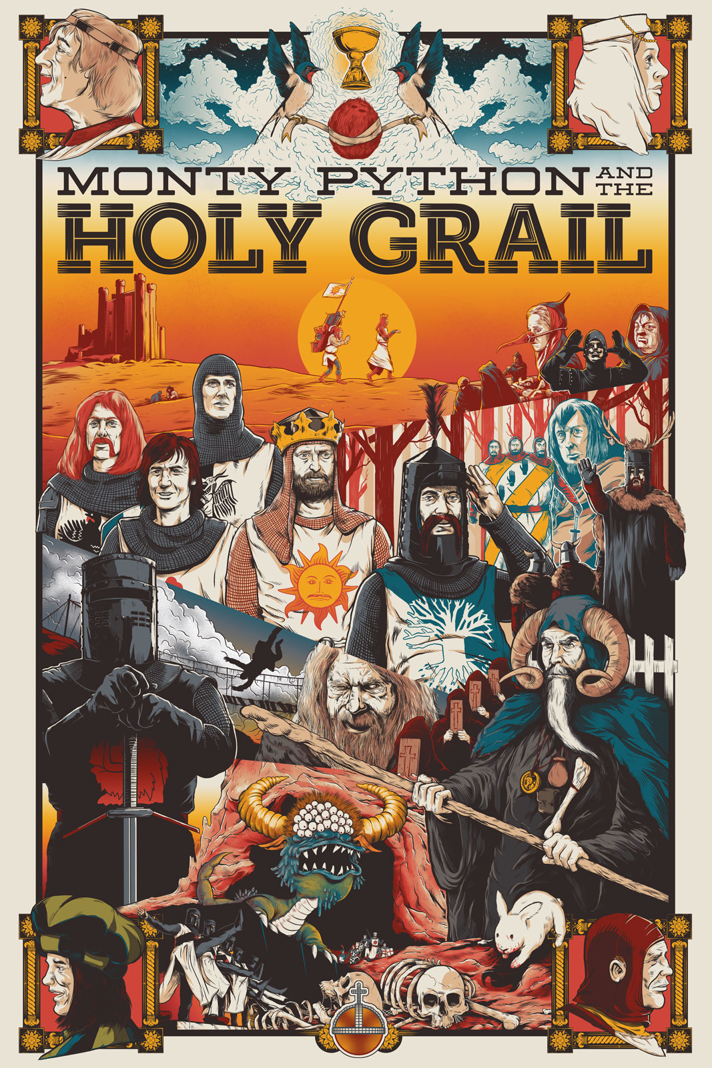
html/res/posters/S3RDN3Z.jpg
