dragland/Smart_Home/html/res/posters/saf7f9k.jpg

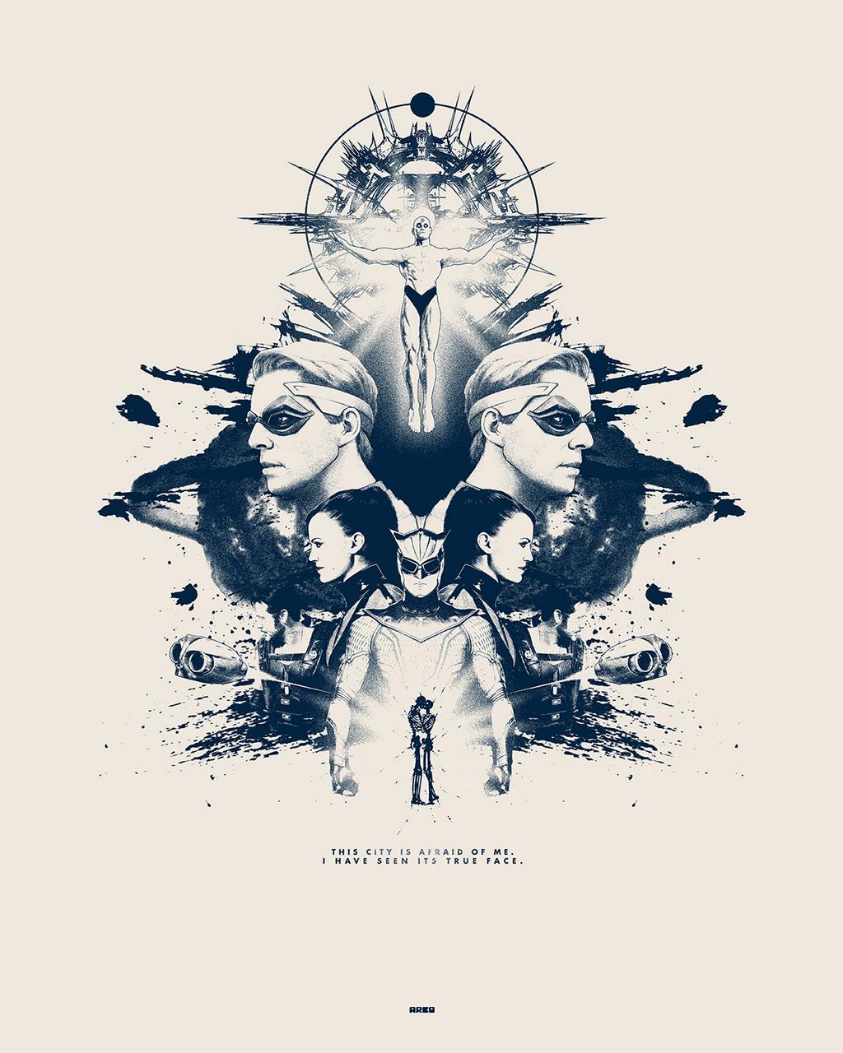
html/res/posters/saf7f9k.jpg
