dragland/Smart_Home/html/res/posters/SF5UjuM.jpg

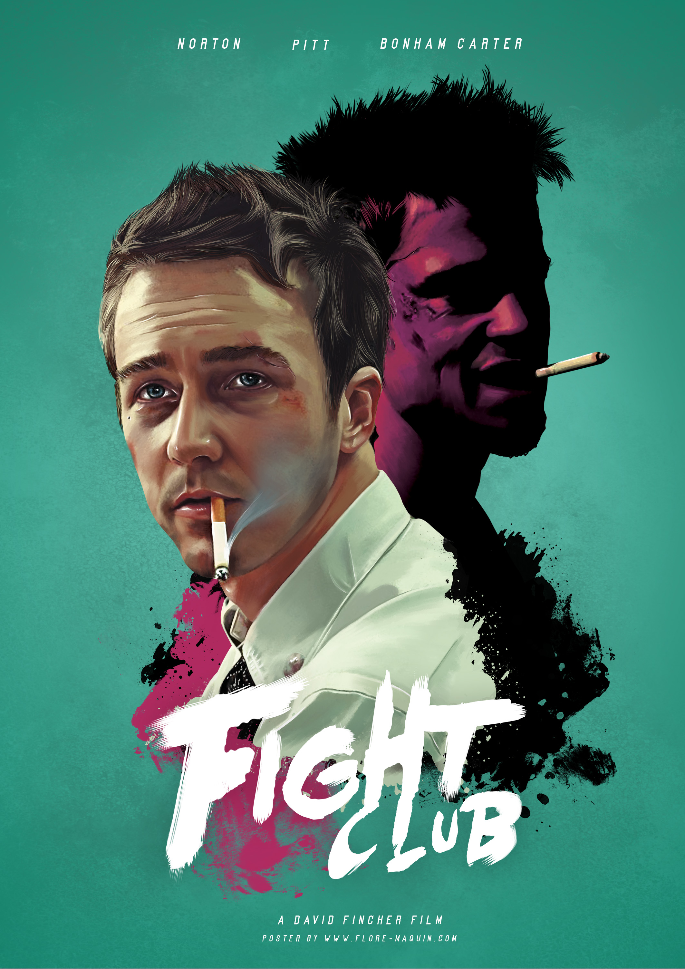
html/res/posters/SF5UjuM.jpg
