dragland/Smart_Home/html/res/posters/sJlPR9H.jpg

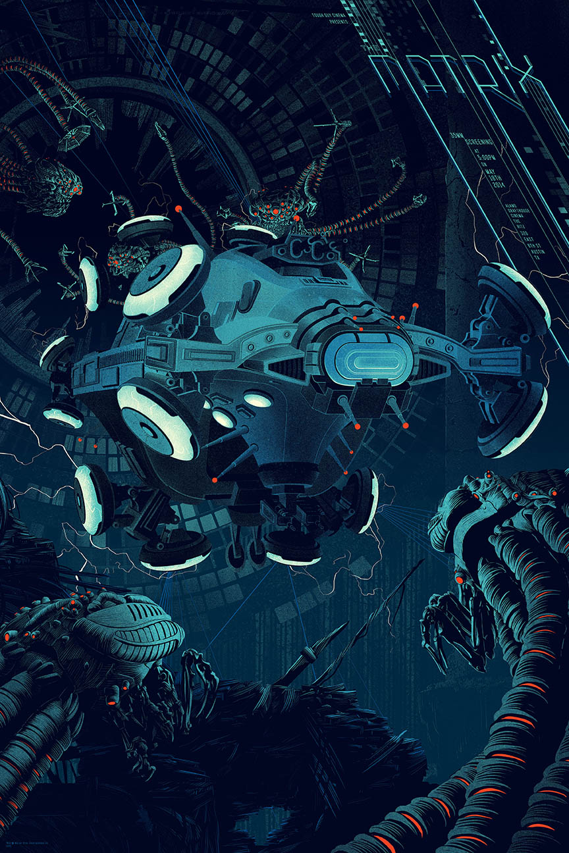
html/res/posters/sJlPR9H.jpg
