dragland/Smart_Home/html/res/posters/slCQupL.png

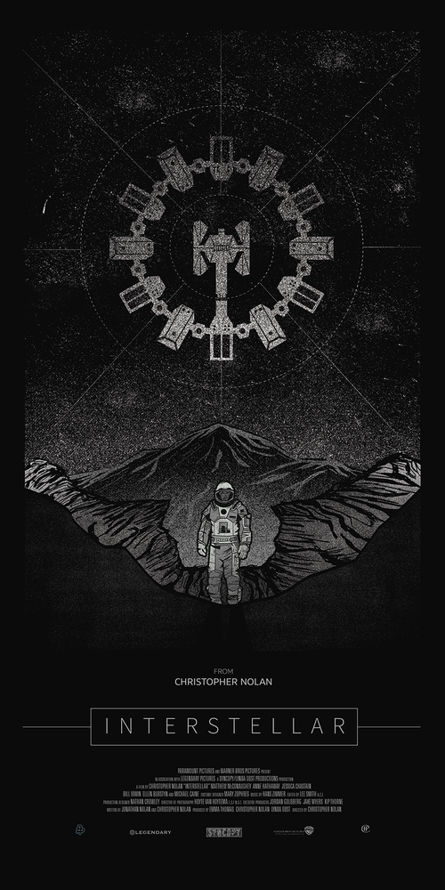
html/res/posters/slCQupL.png
