dragland/Smart_Home/html/res/posters/strangelove_goldB72.jpg

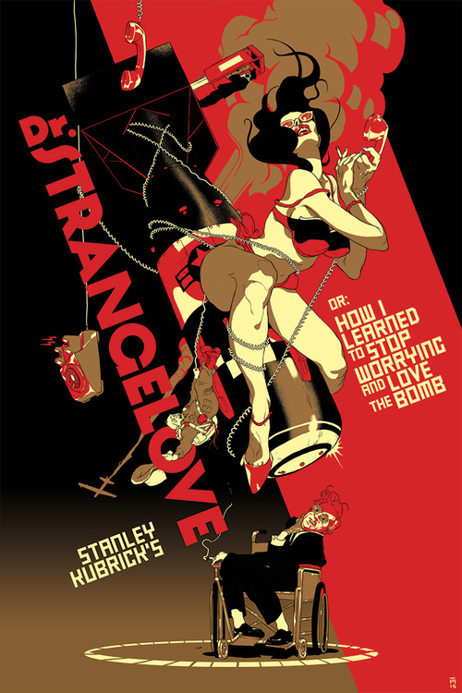
html/res/posters/strangelove_goldB72.jpg
