dragland/Smart_Home/html/res/posters/sxpRi2S.jpg

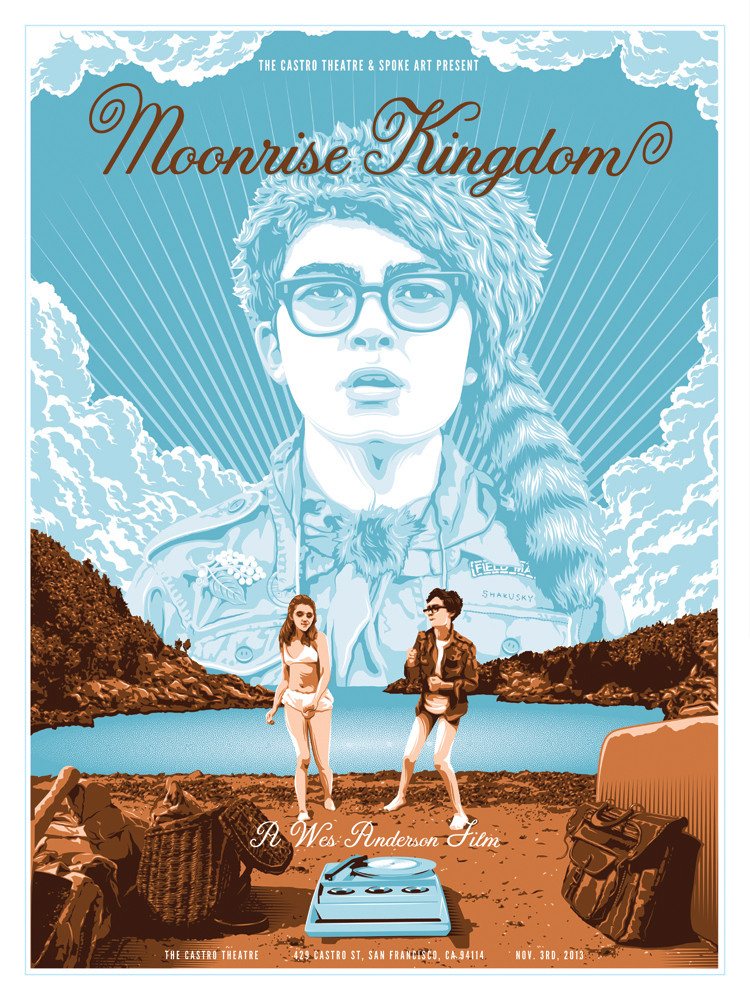
html/res/posters/sxpRi2S.jpg
