dragland/Smart_Home/html/res/posters/T0HjODE.jpg

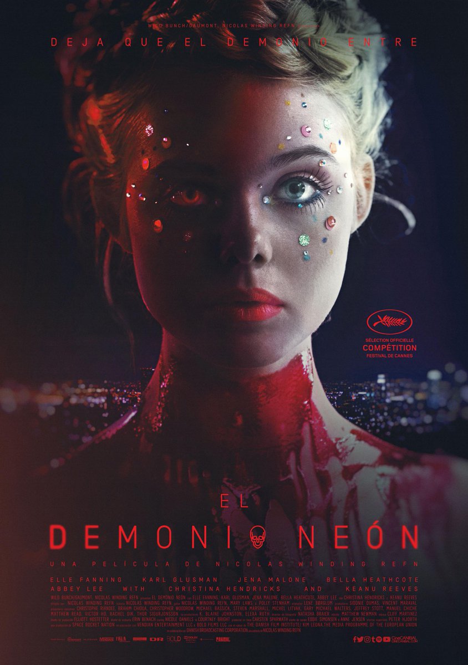
html/res/posters/T0HjODE.jpg
