dragland/Smart_Home/html/res/posters/thd5FWQ.jpg

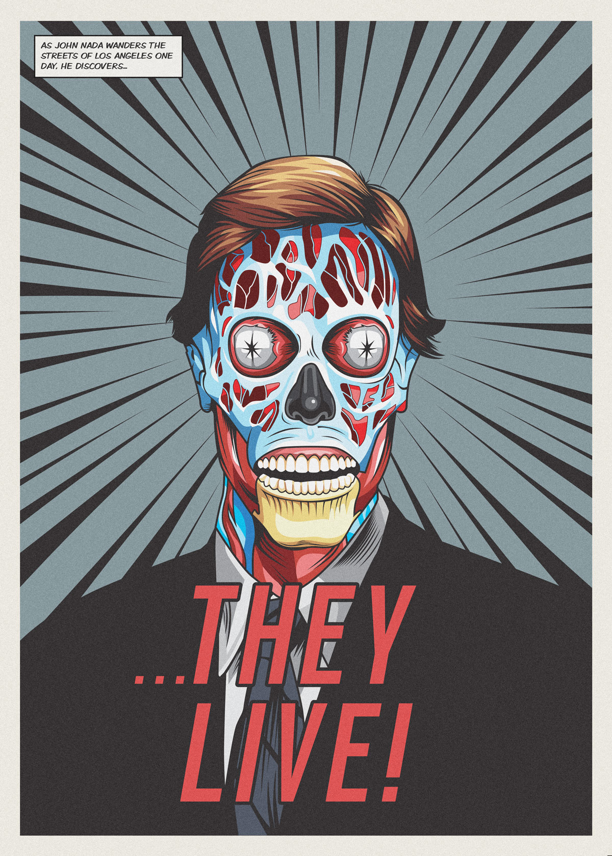
html/res/posters/thd5FWQ.jpg
