dragland/Smart_Home/html/res/posters/there_will_be_blood_movie_poster_rolling_roadshow_2010_olly_moss.jpg

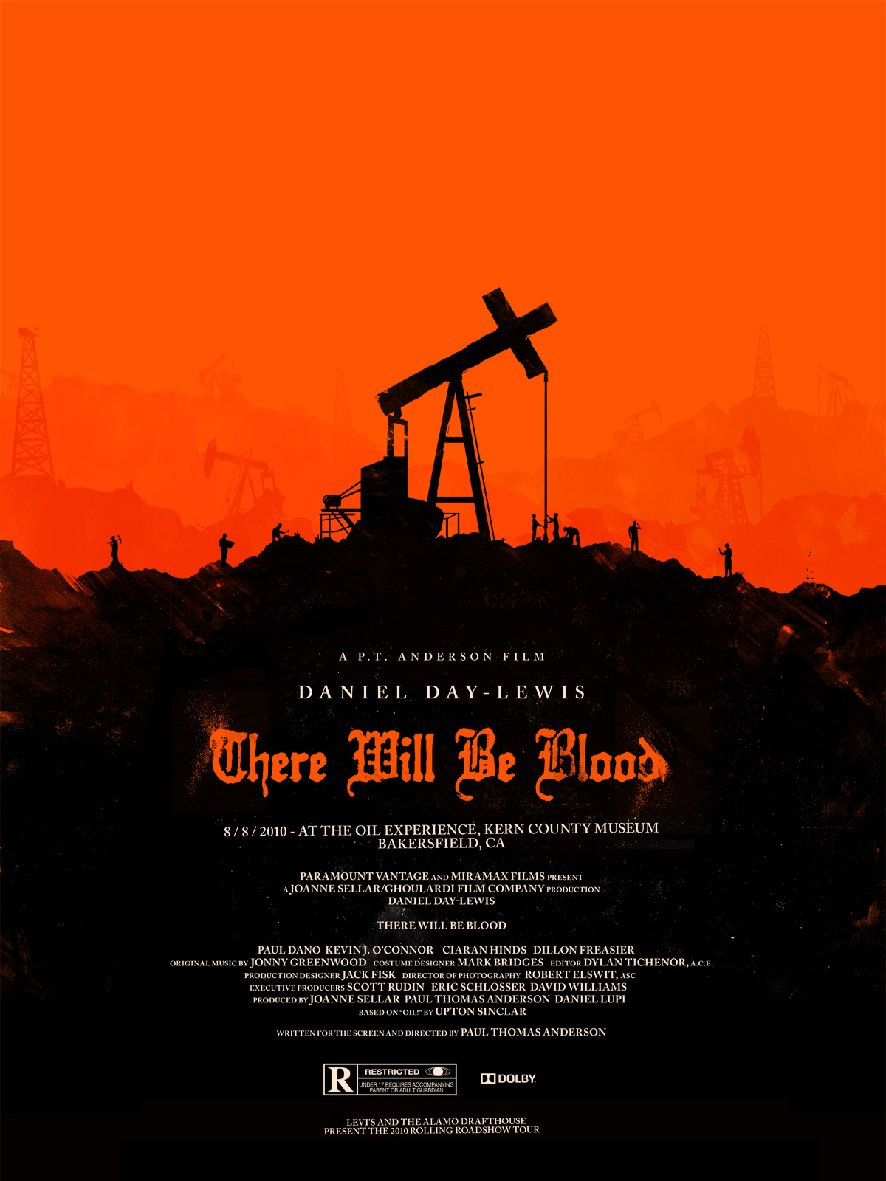
html/res/posters/there_will_be_blood_movie_poster_rolling_roadshow_2010_olly_moss.jpg
