dragland/Smart_Home/html/res/posters/tR6Mz6M.jpg

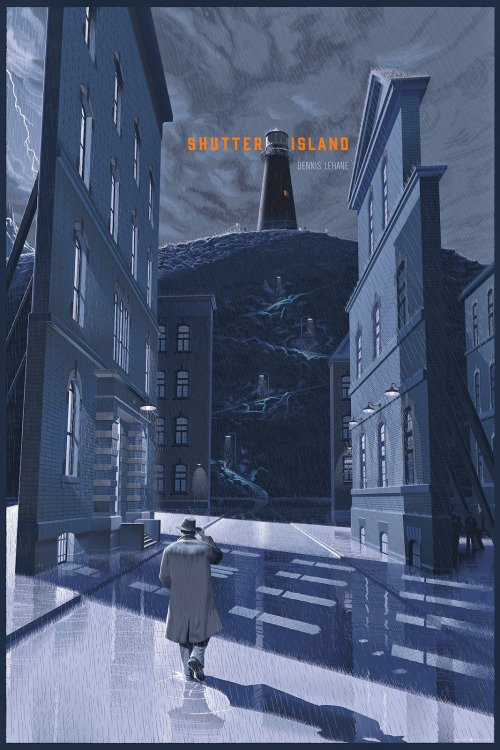
html/res/posters/tR6Mz6M.jpg
