dragland/Smart_Home/html/res/posters/tu4QC.jpg

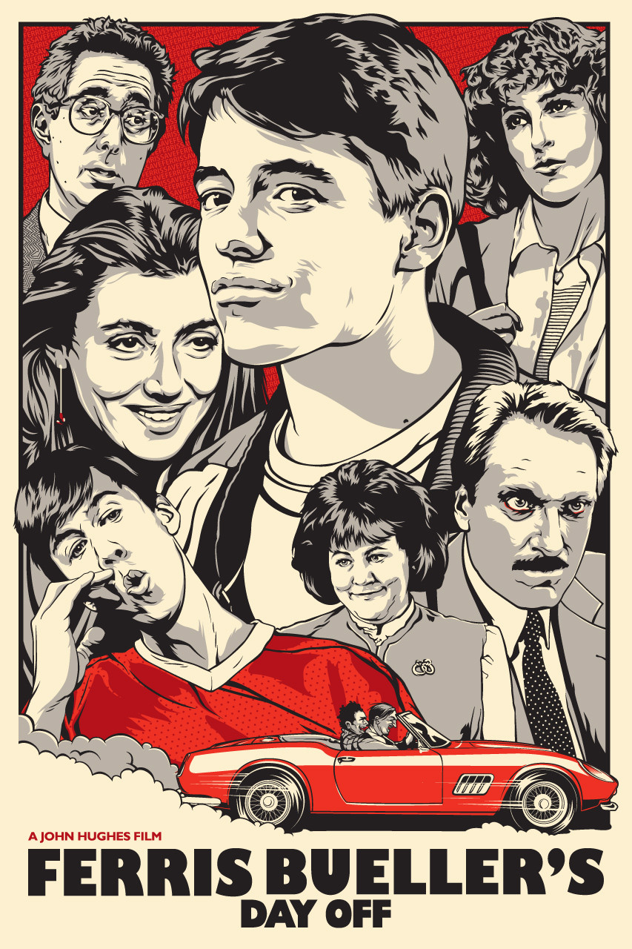
html/res/posters/tu4QC.jpg
