dragland/Smart_Home/html/res/posters/tYyq90B.jpg

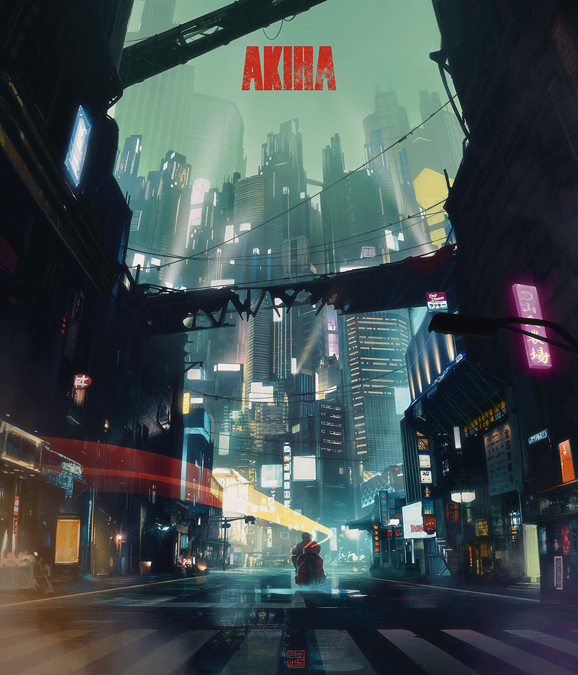
html/res/posters/tYyq90B.jpg
