dragland/Smart_Home/html/res/posters/Uc4pE2F.jpg

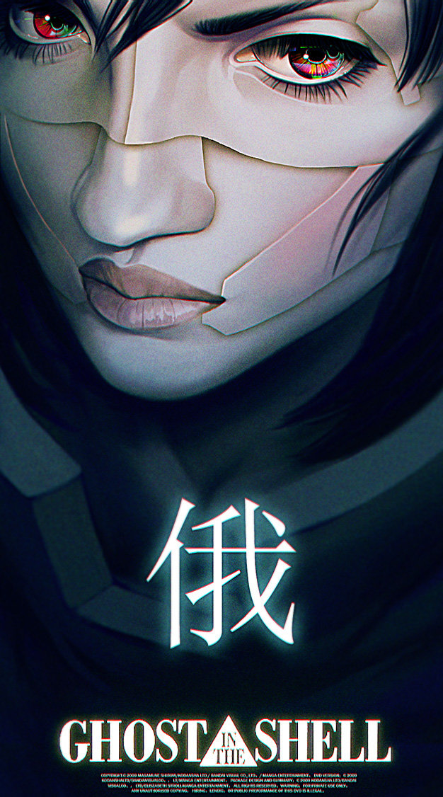
html/res/posters/Uc4pE2F.jpg
