dragland/Smart_Home/html/res/posters/UG1GAxP.jpg

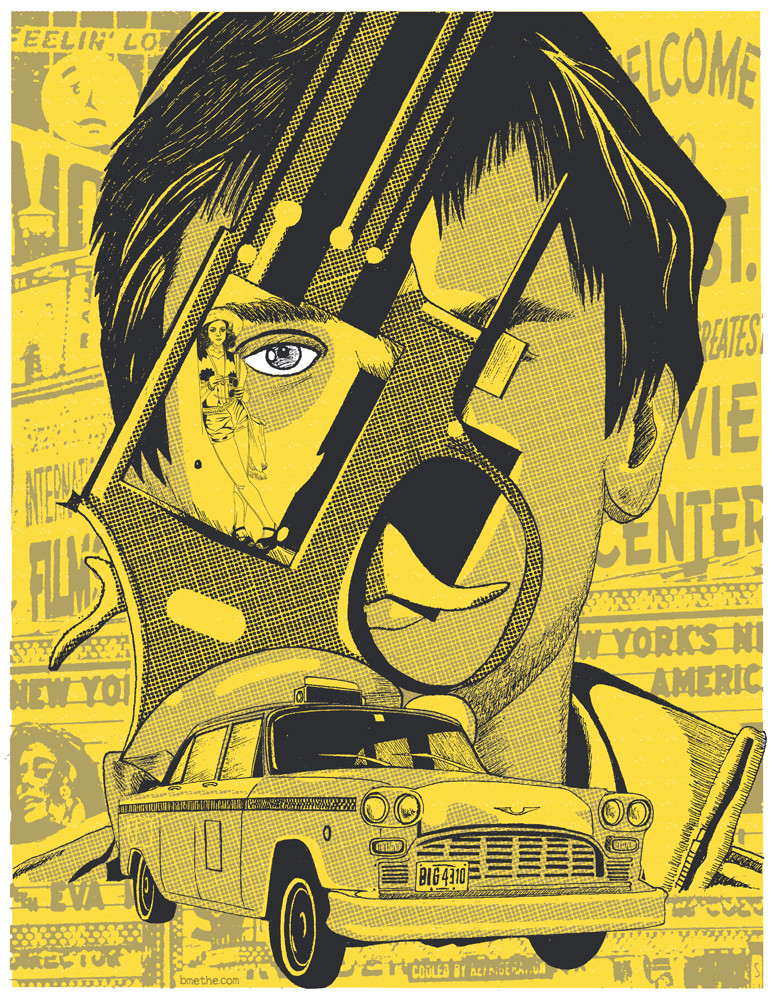
html/res/posters/UG1GAxP.jpg
