dragland/Smart_Home/html/res/posters/uohntjkpxfe01.jpg

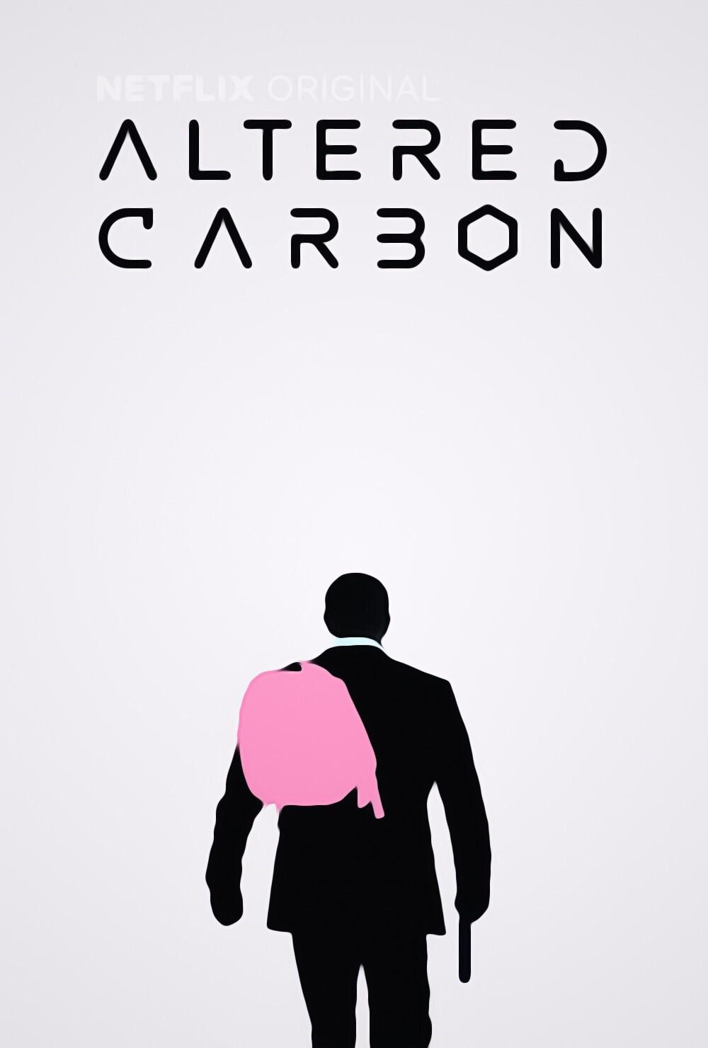
html/res/posters/uohntjkpxfe01.jpg
