dragland/Smart_Home/html/res/posters/v0l420i01hhy.jpg

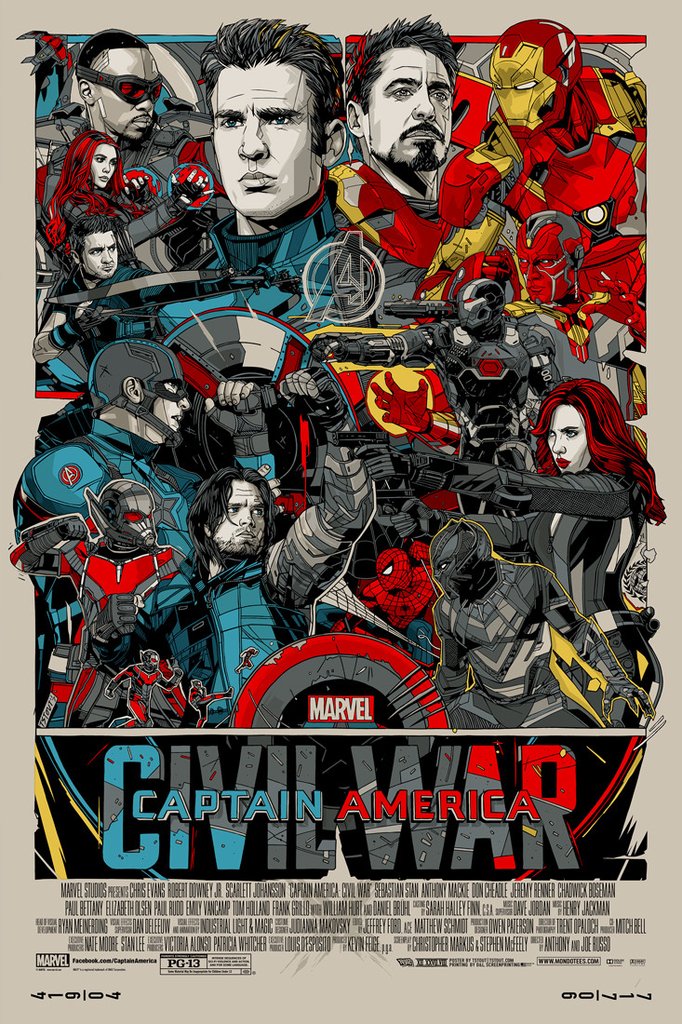
html/res/posters/v0l420i01hhy.jpg
