dragland/Smart_Home/html/res/posters/vjZ3W.jpg

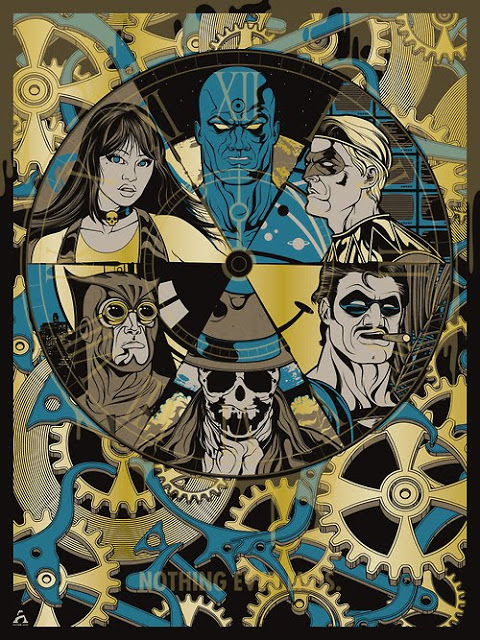
html/res/posters/vjZ3W.jpg
