dragland/Smart_Home/html/res/posters/VMM48aq.jpg

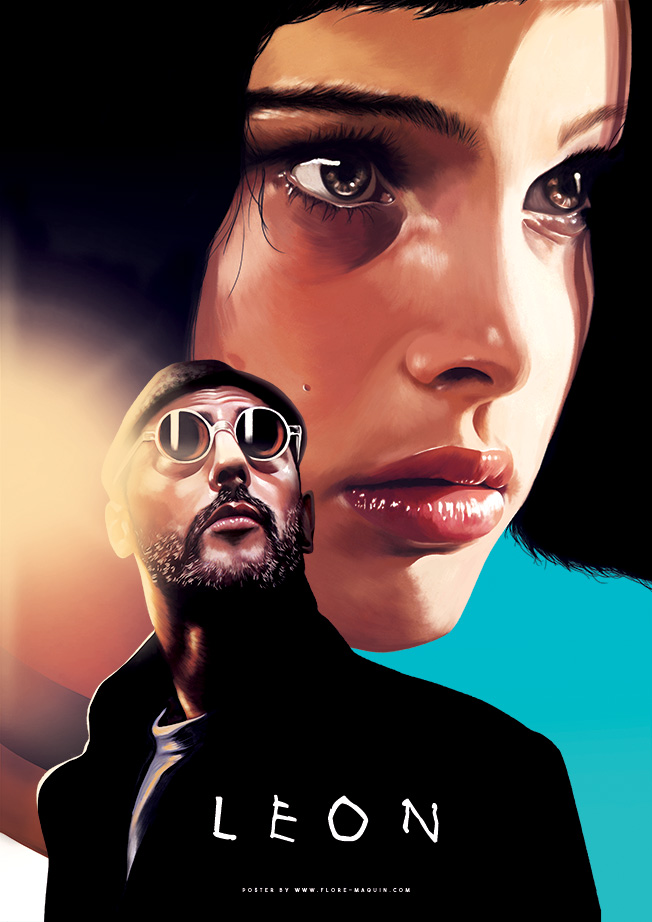
html/res/posters/VMM48aq.jpg
