dragland/Smart_Home/html/res/posters/w989bmslsxcy.jpg

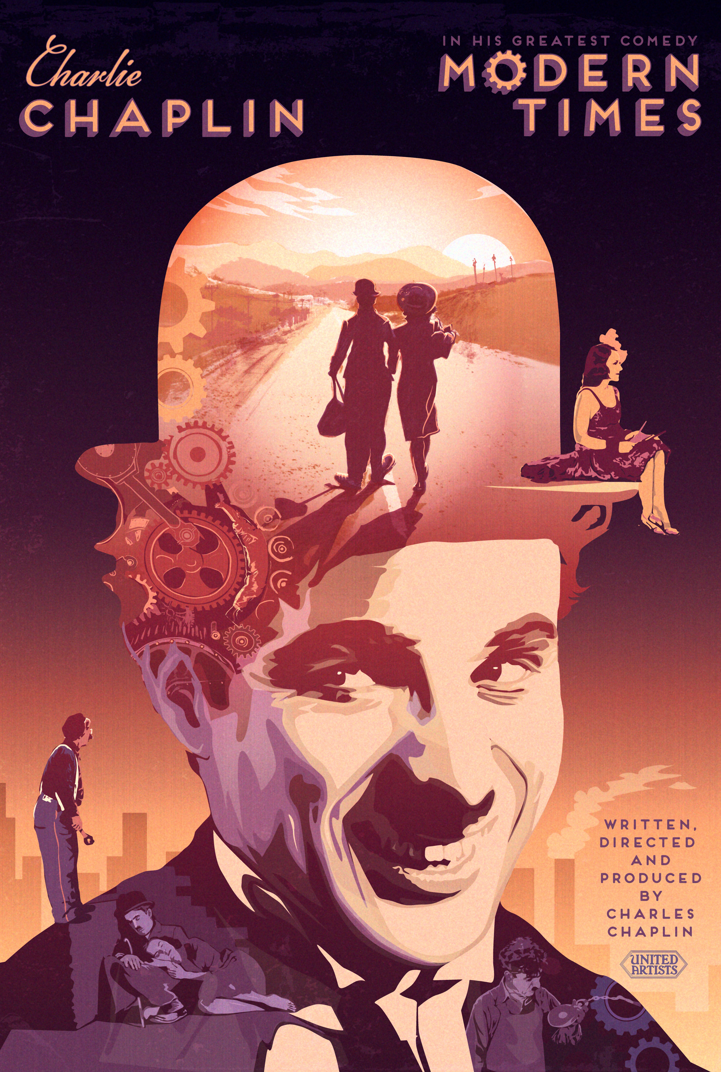
html/res/posters/w989bmslsxcy.jpg
