dragland/Smart_Home/html/res/posters/wqdqs7ggvmcx.jpg

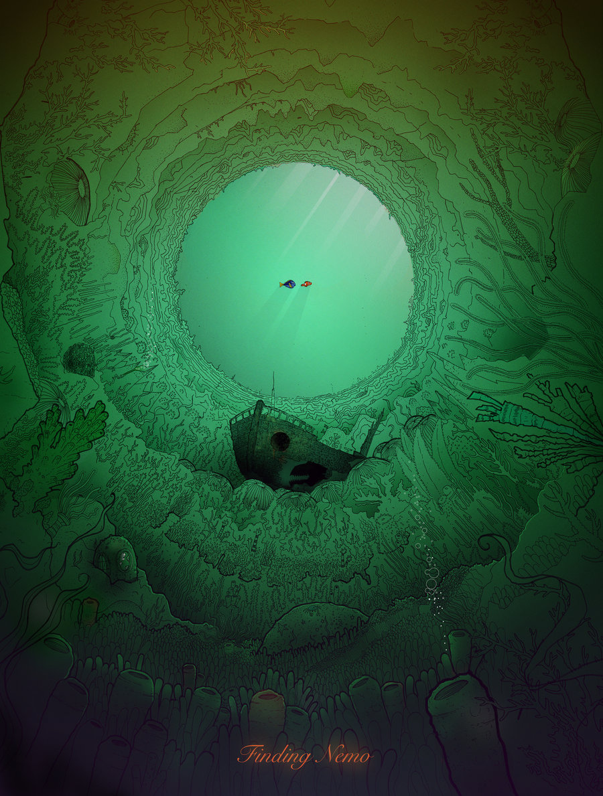
html/res/posters/wqdqs7ggvmcx.jpg
