dragland/Smart_Home/html/res/posters/XF5hDR6.jpg

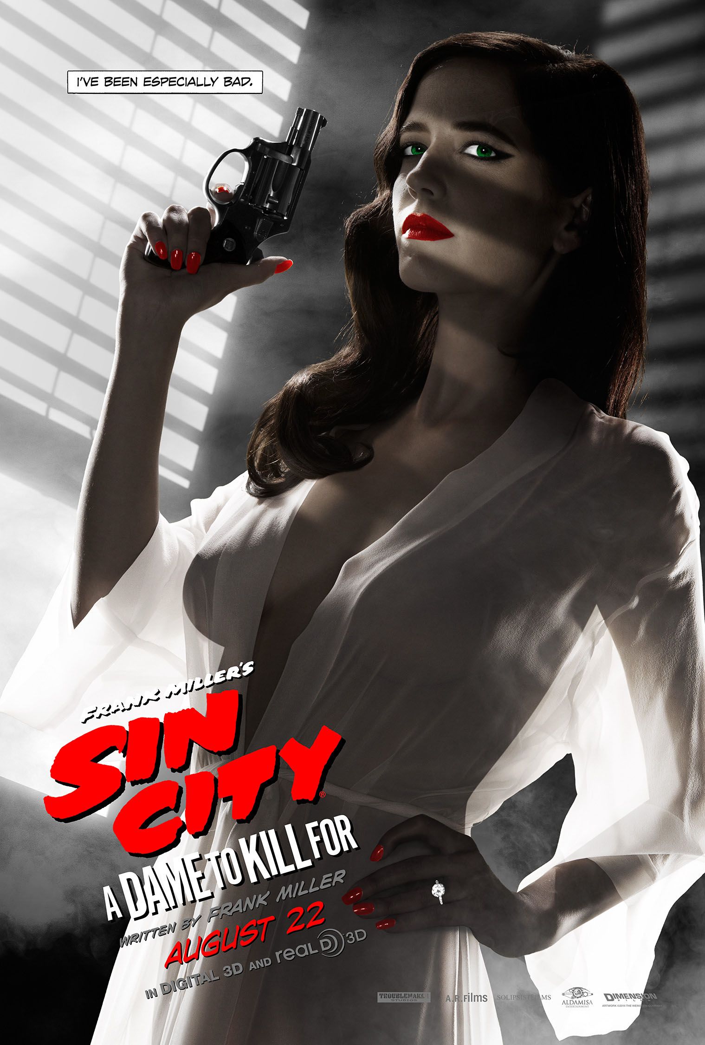
html/res/posters/XF5hDR6.jpg
