dragland/Smart_Home/html/res/posters/xyKWN5B.jpg

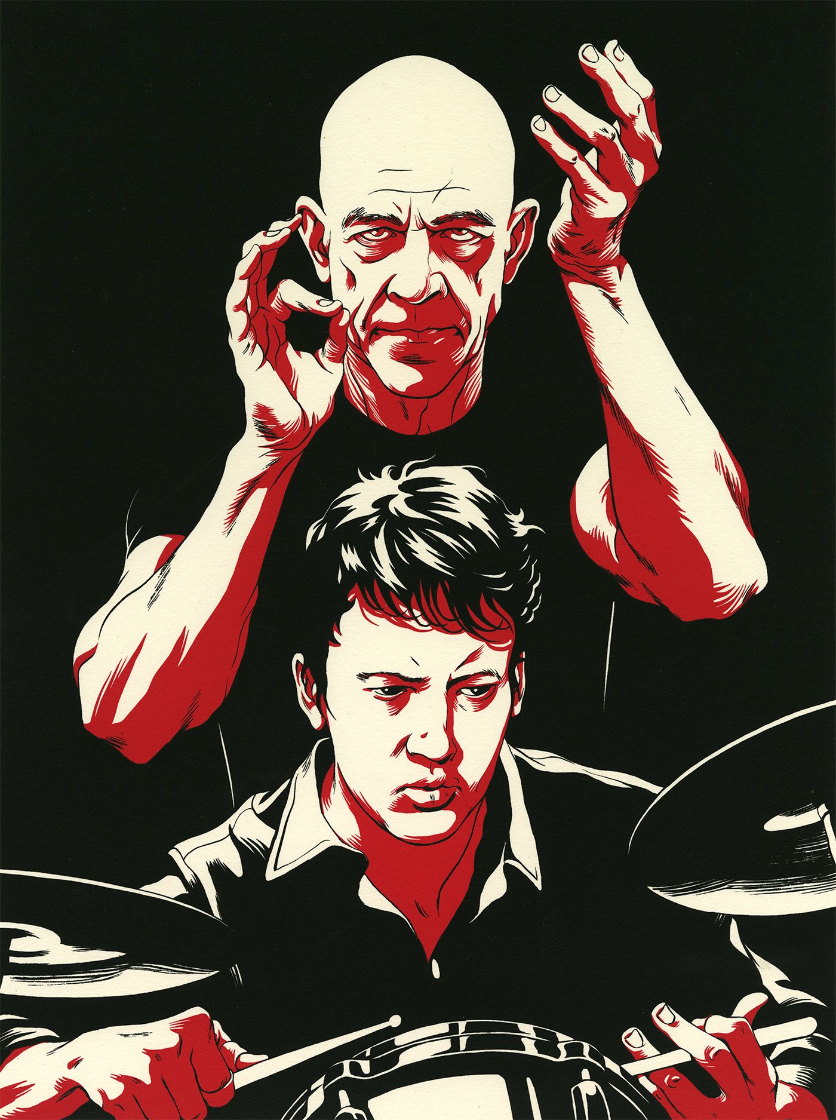
html/res/posters/xyKWN5B.jpg
