dragland/Smart_Home/html/res/posters/Y2ZUJIU.jpg

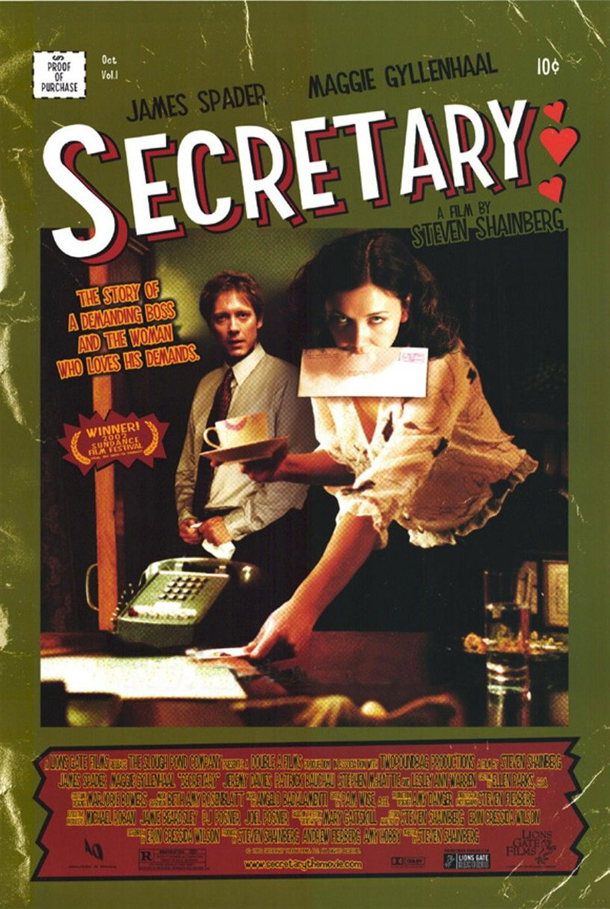
html/res/posters/Y2ZUJIU.jpg
