dragland/Smart_Home/html/res/posters/Y7CET.jpg

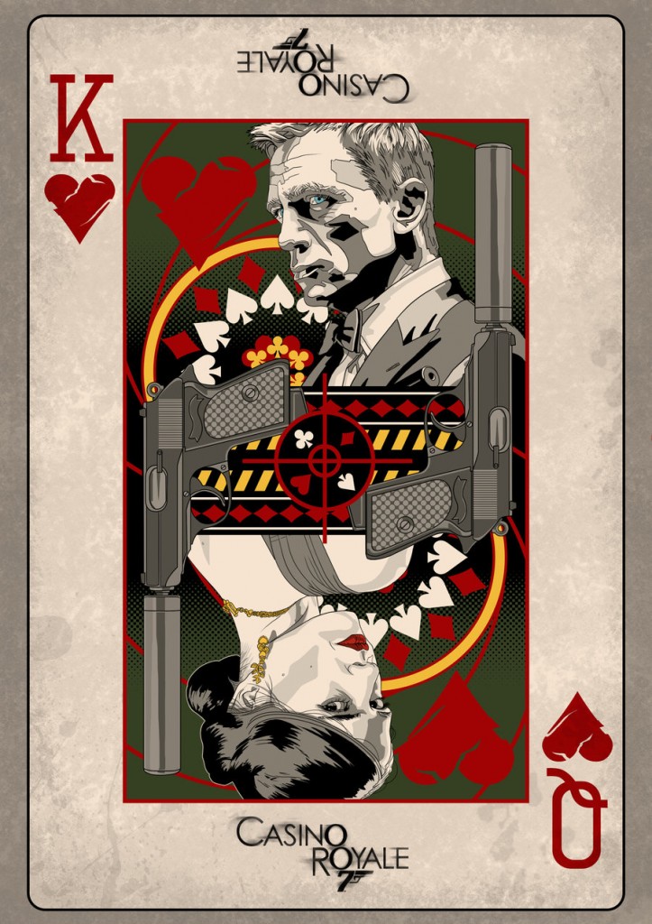
html/res/posters/Y7CET.jpg
