dragland/Smart_Home/html/res/posters/y38lz0yas3sx.jpg

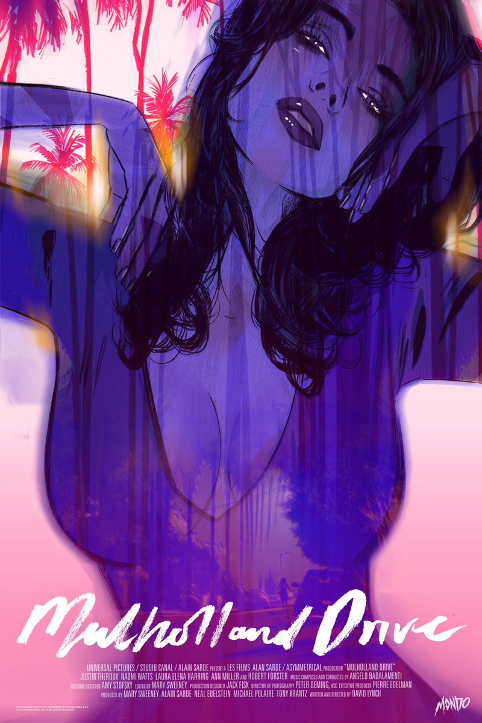
html/res/posters/y38lz0yas3sx.jpg
