dragland/Smart_Home/html/res/posters/Ye6wenY.jpg

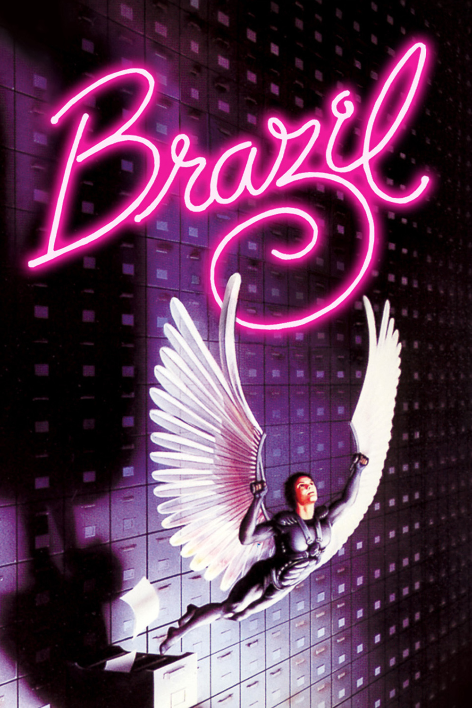
html/res/posters/Ye6wenY.jpg
