dragland/Smart_Home/html/res/posters/YIL3MRW.jpg

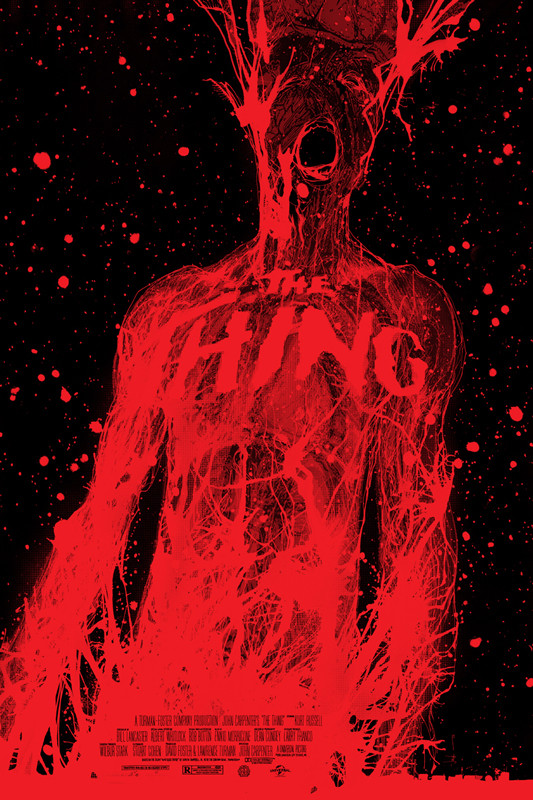
html/res/posters/YIL3MRW.jpg
