dragland/Smart_Home/html/res/posters/yweii4J.jpg

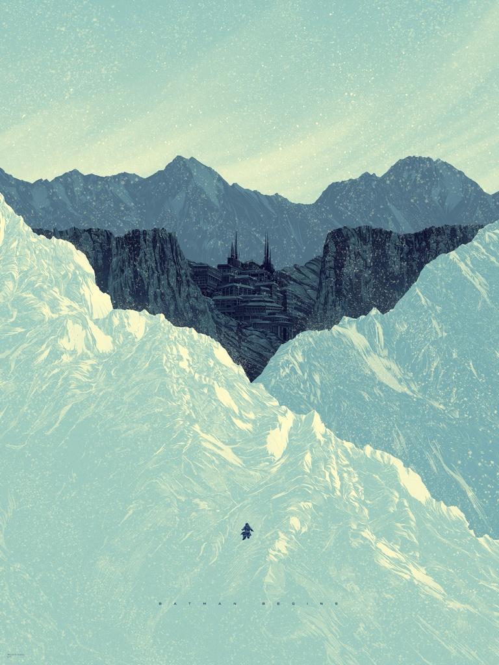
html/res/posters/yweii4J.jpg
