dragland/Smart_Home/html/res/posters/ZCizbzE.jpg

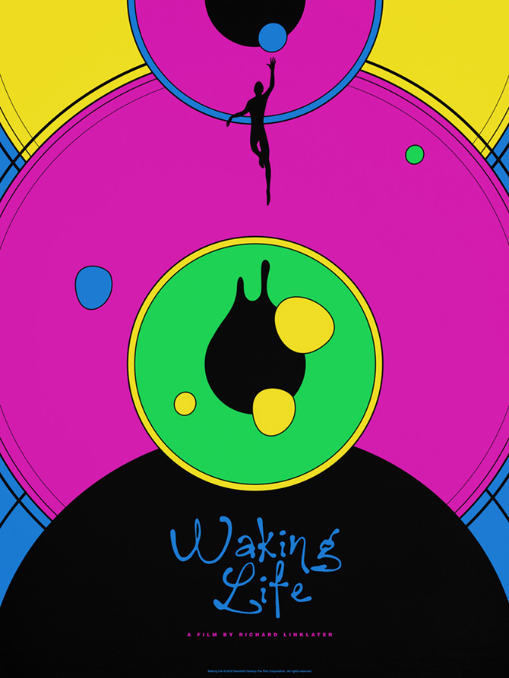
html/res/posters/ZCizbzE.jpg
