dragland/Smart_Home/html/res/posters/zeROMkw.png

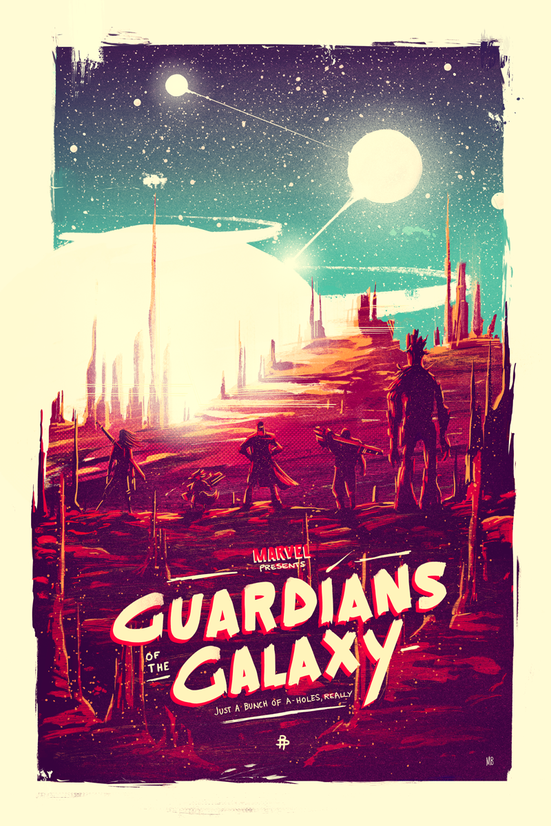
html/res/posters/zeROMkw.png
