dragland/Smart_Home/scripts/state.py

#!/usr/bin/env python
#Davy Ragland | dragland@stanford.edu
#Home Automation System version 3.0 | 2017

#*********************************** SETUP *************************************
temp_f       = 0
rh           = 0
co2          = 0
energy       = 0
cpu          = 0
memory       = 0
wifi         = 0
door         = 0
relay        = 0
